ooyang0325/Hi-Res-DAC/hardware/FUNCTIONAL_ECO_LAYOUT_REVIEW.md

# Functional-ECO board: manual placement and route review

**Capture baseline:** [DAC_HPA_120x100_FUNCTIONAL_ECO_STUDY_ONLY.kicad_pcb](DAC_HPA_120x100_FUNCTIONAL_ECO_STUDY_ONLY.kicad_pcb), 120 × 100 mm, four layers, aligned with the [v1.1-ECO1 schematic](FUNCTIONAL_ECO_2026-09-28.md). The newer [integrated-audio route study](INTEGRATED_AUDIO_ROUTE_STUDY.md) has the same footprint/pad population and is the preferred audio-routing review candidate; its bypass, power and L3 return remain open. The older `DAC_HPA.kicad_pcb`, macro study and separate J702 TVS option are historical comparisons.

The [machine-checked summary](FUNCTIONAL_ECO_LAYOUT_SUMMARY.json) records **544 footprints, 250 named nets, zero footprint bounding-box overlaps and zero KiCad error/warning DRC findings**. The KiCad DRC JSON lists 499 missing connections; the full `pcbnew` ratsnest counts **1,144**. All populated pad nets match the ECO schematic. The conservative JLC package-pair/body-edge screens report zero classified findings, but exact machine access and JLC order DFM remain open. All 478 component bodies resolve to STEP/VRML models; 66 copper-only items intentionally have none.

## Hand changes in this iteration

| Group | Exact change | Measured effect and limit |
| --- | --- | --- |
| U605 MCU readback | U621 and C667 were placed by U605. R688/R689 stayed at 470 kΩ and were moved beside U621; R952/R953 isolate its strong outputs and R954/R955 provide MCU-side fail-high pulls. | The two high-impedance R688/R689→U621 input pad distances are **1.687/1.856 mm**. C667 supply/return pad distances are **2.229/2.229 mm**. Actual traces, ground vias, rail corners and fault timing remain unverified. |
| U301 supply row | C305/C306/C307/C308/C309 were placed in a pin-ordered HF bypass row; C303/C304 sit behind it. | DAC pin-to-100 nF pad distances are **2.236/1.863/1.888/2.296/2.236 mm** for AVCC_L/AVCC_R/VCCA/DVCC/1V3. Supply-and-return loop inductance needs routed copper and L2 via inspection. |
| I/V hold-up | C442/C443 and D411/D412 moved south-east by explicit coordinates in `manual_functional_eco_layout.py`. | Opens the strip below K601 for audio routing while preserving zero courtyard/spacing findings. Diode-reservoir rail routing, access and voltage hold-up still require verification. |
| J702 ESD | D707/D708 are now captured on JACK_RP/JACK_LP. One RP relay→TVS→J702 trial and both local signal/GND-via branches are drawn. | The [independent named-pad audit](LOCAL_TVS_ROUTE_AUDIT.json) measures D707→J702 at **3.864 mm** and D708→J702 at **3.255 mm**, under the provisional 4.2 mm screen. It also checks all four J701 contacts. Full LP output, jack sleeves, return-current geometry and IEC system ESD remain open. |
| X201 80 MHz clock | R203 was rotated; R227 was moved beside its oscillator-side node and given a short L2 GND via. The X201→R203→U301 top-layer trunk now passes through TP711, and the R665→U607 monitor input is connected. R703 remains a distant DNF footprint without copper. | Routed X201→R203 is **1.832 mm**, R203→U301 **6.479 mm**, total **8.311 mm**, inside the 2/8/10 mm screens. The R227 signal branch is **1.509 mm**. The actual pad groups pass `pcbnew` connectivity and KiCad custom-rule DRC. Clock edge integrity, loading/duty, oscillator supply return, full monitor circuit and L2 return geometry still need extraction and measurement. |

The board has **28 F.Cu track segments, seven through vias** and one filled L2 GND zone. These are local TVS branches/returns and the clock trunk, pull-down return and monitor-input branch. There is no USB pair, I²S, complete DAC/I/V, output, power or protection routing. A clean DRC on this partial copper is only a geometry and rule result.

## Output-stage route blocker found by hand probes

U401/U402 output links and relay contacts are vertically opposed: LP/RP links leave above their lower relays K601/K603, while LN/RN links leave below their upper relays K602/K604. Four independent straight-line length checks therefore hid a topological crossing. The VSON-10 output pad pitch is 0.50 mm with 0.30 mm pads, so a 0.50 mm trace directly at a pad leaves only 0.10 mm to its neighbour, below the 0.20 mm rule. A **0.25 mm local escape** leaves 0.225 mm by ideal geometry; it must widen promptly to ≥0.50 mm. The current board's custom rule permits that local width, with final length/DFM inspection still required.

The older temporary route probes under `/private/tmp` are **not** part of the current KiCad board. Their initial "DRC-clean" reports were made in temporary projects that omitted the matching `.kicad_dru` file, so those reports checked only generic clearances. They cannot establish compliance with this board's L1-only headphone LEG/JACK policy or 2 mm left/right separation. I reran the 180° RP-bridge trial with the former rules: it had **15 physical errors** (three disallowed inner-layer/via items and 12 left/right clearance errors). A sixteenth `length` error counted an unrelated branch on `JACK_LP`; the current [named-pad TVS audit](LOCAL_TVS_ROUTE_AUDIT.json) replaces that unreliable branched-net rule. The newer, separate [270° output macro study](OUTPUT_MACRO_ROUTE_STUDY.md) passes the actual rules for four amplifier-to-relay inputs and local feedback; its jack, supply, return and remaining board routes are still open.

| Probe | Result | Disposition |
| --- | --- | --- |
| Original 0° amplifiers, all four LEG links | A roughly 31 mm L3 crossover for LP cleared generic spacing; the shorter LP crossing obstructed RN. | Violates the current L1-only/no-via policy and does not establish a compact complete output layout. |
| Older 270° amplifiers with A/B unit swaps | Four LEG links and Rf/Cf pairs could be drawn against generic clearances, but RN needed a 23.26 mm B.Cu crossover and T-node/bypass nets were still undrawn. | Violates the current L1-only/no-via policy. It would also require a schematic pin-net ECO. This is unrelated to the new 270° study, which keeps the original A/B pin mapping. |
| 180° amplifiers, corrected link ordering | An all-L1 RP detour forced JACK_LP through a 0.24 mm LP/RP pinch near K603. A separate trial used a **14.79 mm, 1.0 mm L3 RP bridge** with two Ø0.8/0.4 mm vias and kept the K601→J701/J702 JACK_LP branches about 18–19 mm. | Neither route is accepted. The bridge violates the current L1-only/no-via policy, and the rerun found 12 left/right spacing errors. Its L3 copper alone is estimated at **8.15 mΩ** at 50 °C, before vias/pad necks. The former 9.575 mm KiCad J702 TVS warning was a branched-net length artefact, not the direct named-pad path. |

No temporary trial was promoted to the captured baseline. The separate 270° macro study proved the amplifier-to-relay inputs; the [integrated study](INTEGRATED_AUDIO_ROUTE_STUDY.md) now connects them through both jack types. It still needs local VPOS/VNEG/EP bypass, input/T networks, L3/L4 return and measured R-15 before it can replace the baseline for full routing. The next accepted iteration must prove those networks **together** and pass DRC with the matching `.kicad_dru` file. Keep L2 continuous and measure actual widths, length, crosstalk and stability. The source 20 mm blanket audio rule is an engineering screen; [constraint disposition](CONSTRAINT_DISPOSITION_V2.md) explains the resistance and return-current criteria. Manual coordinate decisions are required; no placement search was used here.

## Remaining release holds

- [F01 all-rate SPI2 capture](MCU_SPI2_CAPTURE_ECO.md) is a feasible clock-rate *proposal*, with no firmware/RTL or proven DAC-side WS fault coverage. The R-28 high-rate frozen-word energy credit remains open.
- [F02/F04 schematic ECO](FUNCTIONAL_ECO_2026-09-28.md) passes netlist/ERC but needs rail/fault tests, JLC U621 G-3 land resolution, nonlinear TVS loading/THD and IEC system ESD.
- [3V3M charge](ATTACH_CHARGE_RECONCILIATION.json) is 6.5 µF nominal and 43.695 µC in the stated no-load-credit planning bound; measure C(V,T), U502 effective output capacitance and USB attach current/region overlap.
- G-3/G-4 sample overlays and polarity, connector soldering process, all critical concurrent routes, extracted clock/audio returns and JLC order DFM are open. **This is not Gerber/CPL/PCBA release data.**

For visual review, run [the command-line export](PCB_CLI_VISUAL_REVIEW.md) on this board. The GitLab `deliver_review_package` artifact includes a current zoomable SVG, GLB 3D assembly, schematic PDF and the audit JSON files for the same commit.
