ooyang0325/Hi-Res-DAC/hardware/LAYOUT_HANDOVER_REPORT.md

# DAC-HPA layout handover for engineering review

For an engineer **continuing** the layout, start with the
[29 September 2026 execution handoff](LAYOUT_ENGINEER_HANDOFF_2026-09-29.md).
This report remains the detailed area-by-area peer-review guide.

**Review snapshot:** 29 September 2026 · KiCad 10 · 120 × 100 mm, four layers. Review the commit accompanying this report and record its full SHA before making findings. Obtain the matching PDF, layer views, 3D model and audits from that commit's [GitLab pipeline](https://gitlab.com/ooyang0325/Hi-Res-DAC/-/pipelines?ref=codex%2Fschematic-v1.1).

**Release state: HOLD.** The [integrated study PCB](DAC_HPA_120x100_INTEGRATED_AUDIO_STUDY_ONLY.kicad_pcb) is the current schematic-aligned layout review candidate. It has **855 track/via items (143 vias), 864 full ratsnest links, zero KiCad DRC violations and 499 DRC-reported unconnected items**. It remains partial copper for engineering review, not a Gerber, CPL, or JLCPCB PCBA order package. Full routing, system ESD, EMI and audio tests remain open. The [functional-ECO board](DAC_HPA_120x100_FUNCTIONAL_ECO_STUDY_ONLY.kicad_pcb) is the earlier placement baseline; `DAC_HPA.kicad_pcb`, the 100 × 80/100 × 100 mm boards, and the older macro studies are comparisons.

A live working checkout may contain uncommitted workbook or KiCad project-setting changes. Record `git status --short` and review the board from the same commit or working tree as its audits; a pipeline archive represents only its source revision.

## Start the review

| Order | Open | Purpose |
| --- | --- | --- |
| 1 | [Reviewer start](REVIEWER_START_HERE.md), [nine-page schematic PDF](DAC_HPA_review_only.pdf), [schematic guide](SCHEMATIC_REVIEW_GUIDE.md), [schematic simplification review](SCHEMATIC_SIMPLIFICATION_REVIEW.md), [discharge capture review](DISCHARGE_CAPTURE_REVIEW.md) | Learn the signal chain and the v1.1-ECO1 pin map. Both headphone jacks and USB High mode remain required; the DNF reduction ideas are proposals only. Check the newly identified U303 EN calculation mismatch and use [source reconciliation](SOURCE_RECONCILIATION.md) and the [functional ECO](FUNCTIONAL_ECO_2026-09-28.md) where the older Office set differs. |
| 2 | [Integrated PCB](DAC_HPA_120x100_INTEGRATED_AUDIO_STUDY_ONLY.kicad_pcb), [DAC/core route checkpoint](DAC_CORE_ROUTE_STUDY.md), [integrated route study](INTEGRATED_AUDIO_ROUTE_STUDY.md), [constraint disposition](CONSTRAINT_DISPOSITION_V2.md), [Freerouting probe](FREEROUTING_PROBE.md) | Inspect the current DAC/CPLD paths and wider partial routes, returns, component access and provisional limits. The whole-board Freerouting result was rejected; two local low-speed paths were selected and validated separately. Compare the earlier functional-ECO board only when a placement change needs context. |
| 3 | [Placement review guide](PLACEMENT_REVIEW_GUIDE.md), [summary JSON](INTEGRATED_AUDIO_SUMMARY.json), [3D-model review](3D_MODEL_REVIEW.md) | Check the measured screens and their limits. The current board has 478 resolvable component bodies; four VRML film-capacitor envelopes show in KiCad's 3D Viewer but not the exported GLB. |
| 4 | [PCBA process review](PCBA_PROCESS_REVIEW.md), [JLC DFA/DFM rules](JLCPCB_DFA_DFM_RULES.md), [G-3 overlays](G3_OVERLAY_INDEX.md), [G-4 checklist](G4_POLARITY_CHECKLIST.md), [discharge fit option](DAC_HPA_120x100_DISCHARGE_FIT_OPTION_ONLY.kicad_pcb) | Separate physical sample and JLC order questions from KiCad geometry checks. The three-2512 option is a package trial only, with 0.05 mm nominal body-edge margin at R530 and no schematic/BOM ECO. |
| 5 | [Findings template](REVIEW_FINDINGS_TEMPLATE.md) | Return a disposition tied to the reviewed SHA, reference/pad/net, PCB coordinates and layer, evidence, and the action needed to close each issue. |

### Export and zoom into the PCB from a terminal

From the repository root, explicitly pass the **integrated** PCB. The script otherwise defaults to the older functional-ECO baseline:

```sh
git rev-parse HEAD
git status --short
KICAD_CLI=/Applications/KiCad/KiCad.app/Contents/MacOS/kicad-cli \
  bash hardware/make_review_views.sh /tmp/dac-hpa-integrated-review \
  hardware/DAC_HPA_120x100_INTEGRATED_AUDIO_STUDY_ONLY.kicad_pcb
```

On a KiCad 10 Linux installation, use `KICAD_CLI=kicad-cli`. Open `01_body_courtyard.svg`, `02_top_copper.svg`, `03_l2_ground.svg`, **`10_l3_power.svg`**, mirrored `07_bottom_copper.svg`, `08_board_3d.glb`, and `09_drc.json` in the output directory. The [CLI visual guide](PCB_CLI_VISUAL_REVIEW.md) explains mask, paste, legend, image tiling and the commands for rerunning the read-only audits. Inspect the L3 VPOS bridge together with L4, rather than inferring its coupling from the top plot. Open the PCB in KiCad's 3D Viewer for the film-capacitor envelopes omitted from GLB.

## What the present board establishes

| Checked fact | Current result and evidence boundary |
| --- | --- |
| Capture and geometry | 544 footprints, 250 named nets, 855 track/via items (143 vias) and one saved filled L2 GND polygon. The current [route delta](INTEGRATED_AUDIO_MANUAL_DELTA.json) contains 138 hand-chosen footprint moves, eight removed source-copper items and 828 added items. Seven added segments form two individually reviewed Freerouting-assisted low-speed paths; all other added waypoints were chosen manually. |
| DAC/CPLD and local power routes | BCLK/LRCLK/SDATA measure **22.213/22.324/22.879 mm**, with **0.666 mm** spread; MCLK is **8.381 mm** and R215→U202 FAM_CLK is **3.039 mm**. C213/C214/C215 local U202 paths measure **1.103/2.056/3.057 mm**; U302 VIN→C301 is **0.875 mm**, OUT→C302 **2.131 mm**; U303→DAC 1V3 is connected at **25.393 mm with two vias**. C622 at (108.65, 105.50) has a 4.615 mm U604.8→C622.1 path and a 1.020 mm C622.2→GND-via path; saved L2 supports both local paths, while the global 3V3D feed remains open. Thirty-five local GND pads reach L2. Two U202 and five U301 EP vias are filled/capped. The [via-pad audit](INTEGRATED_AUDIO_VIA_PAD_PROCESS_AUDIT.json) leaves 45 unfilled nearby sites for JLC mask/process review. See the [DAC/core route audit](DAC_CORE_ROUTE_AUDIT.json) and [study](DAC_CORE_ROUTE_STUDY.md). |
| Schematic and CAD checks | The pipeline verifies 34 documented workbook-to-schematic pin/net deltas, 0 ERC violations, pad/net identity and the manual board replay. KiCad DRC reports **0 violations and 499 unconnected items**; the full `pcbnew` ratsnest has **864** links. These are partial-board checks and do not prove full-board routability. |
| U609/U610 timer and film bypass | All 12 named-pad timer branches pass the ≤8 mm screen without timer-net vias. U609 LP C/Q/R routes measure **6.089/5.340/4.943 mm** and LN **6.038/5.814/6.685 mm**; U610 LP is **6.442/7.607/1.789 mm** and LN **7.177/7.712/7.787 mm**. KiCad's native U609.10→R921.2 rule measures **7.885 mm** because it includes 1.20 mm of the C632 sibling branch; both methods pass. R921's 0.055/0.092 mm courtyard gaps to U609/Q624 still need G-3 body overlay. C631/C632/C633/C634 GND returns reach L2 in **3.580/3.656/2.650/2.650 mm**. C635/C636 U609 VPOS/VNEG local bypasses connect through 11 new vias (six GND, three VPOS, two VNEG). Upstream rail feeds and U609 VT/control escapes remain open. C636 has a pair-specific **0.60 mm** side-courtyard gap to C631/C632; the four film-cap north/south solder approaches pass at ≥1.5 mm (minimum **3.045 mm**) in the [film solder-access audit](INTEGRATED_AUDIO_FILM_SOLDER_ACCESS_AUDIT.json). U605/R675/R676/R679/R677 moved left **1.2 mm** and C625 moved near R666, clearing six measured 5 mm I²S/protection gaps. C638 uses a two-via L3 VNEG bridge. |
| Track shape and placement screens | The integrated checker finds **0 exact or near-90° bends**, zero footprint bounding-box overlaps and zero classified JLC spacing findings. It counts eight near-orthogonal joins at component pad centres; straight-through T/cross junctions are classified separately. The timer pair-specific **0.60 mm** film-cap side-courtyard exception retains at least **1.5 mm** north/south solder approach per the [film solder-access audit](INTEGRATED_AUDIO_FILM_SOLDER_ACCESS_AUDIT.json). These screens do not replace JLC order review or assembly inspection. |
| Selective routing assist | The rejected whole-board [Freerouting probe](FREEROUTING_PROBE.md) supplied only two individually checked low-speed local paths: `N2_AUD_EN_MCU` R237.1→U201.51 at **4.285 mm** and `N7_LEDR_A` R702.2→D706.1 at **4.649 mm**. They add seven 0.20 mm F.Cu segments, no vias and no right-angle bends; saved L2 remains directly below both. |
| DAC and I/V | Four U301→U403/U404 input routes are 4.294/6.030/6.837/4.786 mm with no vias; DACR has only **0.163 mm** under the provisional 7 mm ceiling. Saved L2 lies beneath those routes at 0.01 mm centreline samples and ±0.05/0.10 mm offsets. The largest projected **2D** I/V feedback area is 4.875 mm². These screens do not extract stability or return impedance. |
| Output and ESD | Four amplifier legs reach their J701 contacts; LP/RP also branch to J702. Six named-pad TVS routes measure 3.255–4.03 mm against the provisional 4.2 mm limit. Loaded output impedance, ESD return and system tests remain open. |
| JLC/3D screens | The classified package/edge proxy and via-ring audit report zero findings. Of 463 JLC-placed references, **447** are classified by the package-spacing proxy and **16** need individual review. The model-path audit resolves 478 component bodies. None of these screens is JLC order approval or a physical fit measurement. |

The detailed measurements and conditional R-15 output-impedance model are in the [route study](INTEGRATED_AUDIO_ROUTE_STUDY.md) and [trace budget](INTEGRATED_AUDIO_TRACE_BUDGET.json). Treat those model values as planning estimates: the assumed 50 mΩ jack contact has no maker maximum, the 3.5 mm sleeve return is not extracted, and neither jack has a completed loaded measurement.

## Reviewer decisions to return

| Priority | Location and question | Evidence needed to close it |
| --- | --- | --- |
| 1 · Analog return and stability | U301 (90.5, 81), U403 (96.3, 77.2), U404 (96.3, 84.8). DACL's U403.6→C417.1 feedback branch lacks direct L2 under **1.9426 mm** of its centreline near the `N4_IVL_P` via at **(96.625, 78.170)**. The DACR input route is 6.837 mm, and VREF reaches 14.422 mm. Is the feedback, bypass and reference geometry acceptable after extraction? | Review the actual 3D feedback and return-current path, summing capacitance, VREF noise and I/V stability/step response. A new via or placement proposal must still pass the 7 mm DAC input screen, courtyard clearances and DRC. |
| 2 · Cross-layer audio and power | The `N4_IVR_P`→R409 feed is **47.752 mm**. L3 local VPOS crosses the two right I/V L4 feeds around **x = 115–121, y = 74–76 mm**. U501 is at **(72, 132)**; local copper exists but main VPOS/VNEG source feeds to U401/U402 and their exposed-pad thermal routes do not. The seven filled/capped EP vias are at U202/U301; they do not close U401/U402 EP thermal routes. | Co-route the rails and returns with the audio feeds, extract coupling and shared impedance, and test loaded stability, noise, THD+N and crosstalk. Examine U501 C510/C511 ground-via spacing of 8.160/6.767 mm as geometry, not an extracted loop length. Full audio/EMI tests remain open. |
| 3 · Remaining route feasibility | USB D+/D−, I²S branches beyond the drawn source-to-DAC paths, U609 VT/control escapes, upstream rail feeds, much of the power/protection network and most of the 864 ratsnest links remain. All 12 U609/U610 timer signal branches pass the named-pad 8 mm screen. | Trial the USB 90 Ω pair against the quoted JLC stack-up, complete remaining I²S branches and U609 VT/control escapes with L2 returns and timing checks, and draw remaining bleed/reset branches before accepting the placement. Demonstrate that critical paths coexist. |
| 4 · Connectors, DFA and JLC process | J701 (146.5, 76), J702 (150.84, 109.5), J101 (45, 75). J101 shell stakes and J702 plated slots 1/2 have **no F.Paste apertures**. J101 overhangs the left edge by 0.05 mm; J702 is 0.33 mm from the right edge. C423/C426 courtyard gaps are 0.150–0.194 mm. | Record G-3 1:1 physical overlays and remaining G-4 polarities; obtain JLC acceptance for slot soldering, enlarged lands, panel rails, mask and component access. Inspect the C437/J701/K602 corridor and 16 unclassified package references in the actual order preview. |
| 5 · Function and measured outputs | The all-rate post-CPLD capture/guard, DAC-side WS fault coverage, readback corners, attach current, 3V3D/1V3 discharge and system ESD are still qualification holds. R-15 depends on estimated contacts and an unextracted jack return. | Review [F01 capture proposal](MCU_SPI2_CAPTURE_ECO.md) as unimplemented, the [discharge capture/model mismatch](DISCHARGE_CAPTURE_REVIEW.md), [pre-layout gates](PRELAYOUT_GATES.md), and the [PCBA process record](PCBA_PROCESS_REVIEW.md). Require operating firmware/RTL, fault and power-sequence tests, jack impedance measurements and ESD results before functional or order release. |

G-1/G-2 connector continuity reports were accepted by the owner for layout planning with the raw measurement log waived. **That waiver does not close G-3 footprint overlays or G-4 polarity checks.** The 3.5 mm output is for TRS plugs only; J702 pins 5/6 are unused break contacts and must remain unconnected. J701 switch pads 9/10 likewise remain unconnected in this candidate.

Return each finding as **pass**, **issue**, **needs evidence**, or **not reviewed** in the [findings template](REVIEW_FINDINGS_TEMPLATE.md). A proposal to change the board should cite the affected schematic/PCB net and controlled constraint, preserve the explicit manual route record, and rerun the integrated checker and GitLab pipeline. Do not use the historical automatic `place_board.py --force` flow to regenerate this manual candidate.
