ooyang0325/Hi-Res-DAC/hardware/PRELAYOUT_GATES.md

# Pre-layout gate record — design set v1.1

Design Spec v1.1 permits **provisional placement on a 100 × 80 mm board**. The owner later selected 100 × 100 mm, then allowed the 120 × 100 mm manual placement. The [functional ECO](FUNCTIONAL_ECO_2026-09-28.md) makes the 544-footprint candidate schematic-aligned, including the explicit U403/U404 A/B-channel reassignment; the former primary is historical. The Spec originally held schematic freeze and routing until G-1–G-4 passed with signed measurement records. On 27 September 2026 the owner explicitly waived the G-1/G-2 measurement log after reporting the two-sample checks below. Treat G-1/G-2 as owner-accepted for layout planning, **not** as independently evidenced passes. The [integrated-audio study](INTEGRATED_AUDIO_ROUTE_STUDY.md) draws four DAC→I/V inputs, I/V feedback, eight I/V→first-T feeds, the local T cells, output paths through both jack types and U501 local switching/feedback copper. The newer [DAC/core checkpoint](DAC_CORE_ROUTE_STUDY.md) measures the U202→U301 I²S paths at 22.213/22.324/22.879 mm and MCLK at 8.381 mm, plus local U202/U302 and U303→DAC power paths. The current board has 855 track/via items (143 vias), 864 full ratsnest links, zero DRC violations and 499 DRC-reported unconnected items. True I/V loop and return extraction, upstream source feeds, U401/U402 output-amplifier EP thermal routing and L3/L4 returns remain open. Two U202 and five U301 EP vias are filled and capped; 45 unfilled via-to-SMT-pad sites remain for JLC mask/process review. Full routing, system ESD, EMI and audio tests, G-3/G-4, measured R-15 and F01–F04 continue to hold release. KiCad netlist/ERC and a passing GitLab pipeline establish capture consistency, not operating function or route quality.

| Gate | Evidence needed before schematic freeze and routing | Current record |
| --- | --- | --- |
| G-1 — J101 USB-C | Original protocol: two identified USB4105-GF-A samples; DMM continuity of all 12 GCT solder lands, the four shell stakes and both plug orientations against the 16 JLC pad IDs; signed pad-to-contact table. | **Owner-accepted with evidence waiver.** Owner reports both samples fully match the KiCad map, including both plug orientations. Sample IDs, raw readings and signed table were explicitly waived; no independent record exists. |
| G-2 — J701/J702 jacks | Original protocol: two identified samples of each jack; pad-to-plug contact table with no plug, fully inserted and slow insertion/removal; all internally common pairs; J701 tabs 11/12 versus sleeve/bushing; J702 break contacts 5/6. Only TRS use is permitted for J702. | **Owner-accepted with evidence waiver.** Owner reports both J702 samples match 3–5 and 4–6 closed without a plug and open with TRS inserted; pads 1/2 = sleeve, 3 = right ring, 4 = left tip. Both insertion sweeps showed only expected break transitions; pads 5/6 never touched sleeve or opposite channel; there is no accessible metal shell. Owner reports both J701 samples match pad 1 = sleeve, 2/3 = R−, 4/5 = R+, 6 = L−, 7/8 = L+; tabs 11↔12 and each ↔bushing short, each ↔sleeve open; pads 9↔10 short without plug, open inserted and change during insertion/removal while isolated from audio pads 1–8 in both end states. Sample IDs, raw readings and signed table were explicitly waived; no independent record exists. |
| G-3 — 1:1 footprints | Drawing/sample overlay of J101/J701/J702, K601–K604, X201–X203, U202 exposed pad, the other new/changed lands in Spec §9.6, including U611/U612, Q627, C647–C654, TI DGK U613–U620, and **new U621 C507231**. Record pin-1 marks, slots, pegs, copper clearance and ≥0.1 mm terminal overlap; obtain JLCPCB DFM acceptance of the enlarged jack copper and U621's TI/JLC DCK land difference. | Open. Owner reports all originally listed physical samples are ready. Two review-only 1:1 overlay sheets and a 30-footprint checklist are prepared, including U621 and D707/D708; no overlay results are recorded. Owner chose copper-only enlargement: J701 2.15 × 1.25 mm pads around unchanged 1.40 × 0.50 mm slots; J702 pads 1/2 2.25 × 1.35 mm around unchanged 1.50 × 0.60 mm slots. Both reach ≥0.31 mm worst copper ring at JLCPCB's +0.13 mm plated-slot tolerance. |
| G-4 — polarity | DMM diode/continuity checks on two samples against body/tape marks for D705/D706, BAT54S, D102, D104/D105, D411/D412, D609/D610, C442/C443, Q623–Q627, K601–K604 and the other pin-1 parts in Notes §9.6. | Partial: owner reports two physical samples each of D705 and D706 diode-test as pad 1 anode (+), pad 2 cathode (−), matching KiCad. Sample IDs/readings and the remaining polarity/pin-1 parts are still open. |

## Decisions already in force

- The owner allowed a 120 × 100 mm primary, four-layer manual placement after the 100 × 100 mm comparison. The 100 × 80 mm and 100 × 100 mm automatic boards remain review comparisons. Top-side Standard PCBA and the owner-fitted list remain as in Spec v1.1. The source document's outline needs revision before manufacturing freeze.
- U403/U404 use the owner-approved OPA2210IDGKR VSSOP-8, JLCPCB C2876414, with positive DAC legs on physical B and negative legs on A. DACL/DACLB/DACR/DACRB routed lengths are **4.294/6.030/6.837/4.786 mm** on F.Cu without vias, under the provisional ≤7 mm target; DACR has only **0.163 mm** margin. Saved L2 GND is directly beneath all four inputs at 0.01 mm route samples and offsets 0, ±0.05, ±0.10 mm. The source documents still specify SOIC-8, the earlier A/B assignment and ≤5 mm; extracted capacitance, 3D feedback/return geometry and step response must close the reassessment.
- The 3.5 mm output is for TRS plugs only. The HRO jack has a TRRS body, but TRRS headphones are outside the supported use; G-2 needs the intended TRS test, which the owner reports matched on both samples. The PCB silkscreen/user instructions should say “3.5 SE · TRS only”.
- The v1.1 defaults remain adopted: pairwise boot self-test with production per-leg injection, the Spec's DC-energy definition, and the High-mode 32 Ω frozen-full-scale engineering estimate with a bring-up energy test. Reopening self-test coverage would add parts and must happen before routing.
- The v1.1 model assumed 50 mΩ per jack contact and per 0 Ω output link. The [review-only R417–R420 BOM candidate](OUTPUT_LINK_BOM_ECO.md) has a 1 mΩ manufacturer maximum per link; the unchanged contact estimate has no maker maximum. With that candidate, the integrated board's conditional worst 4.4 mm estimates are **0.3862/0.3737 Ω (L/R) at 1 kHz** and **0.3990/0.3864 Ω at 20 kHz**. The latter is a model sensitivity if the same ≤0.5 Ω limit applies there. Measure both jacks over the intended audio band, extract the 3.5 mm sleeve return and confirm R-15's frequency scope; this is not a pre-layout measurement.
- The owner chose at least a 0.30 mm worst copper ring by enlarging copper only. Using JLCPCB's +0.13 mm plated-slot tolerance, J701/J702 now reach ≥0.31 mm worst ring. Slots, pad centres and peg holes do not move. G-3 overlay and JLCPCB DFM acceptance remain required.
- The ring calculation does not include slot-to-copper registration error; JLCPCB must confirm the final land in DFM. The nearest J701 pad-to-pad copper gap is 0.25 mm.
- The integrated study's custom DRC enforces **2 mm F.Cu left/right clearance for pre-link `N4_*_OUT` copper** against the opposite channel's output/leg/jack copper, in addition to the existing post-link 2 mm rule. The J701 fixed-contact fanout retains its narrow courtyard exception. This partial-copper screen does not close L4 coupling or measured crosstalk.
- The integrated board has **138 explicit moves, eight removed source-copper items and 828 added copper items** against the functional-ECO baseline. Eight local T triplets and amplifier input/shunt connections are drawn on F.Cu; R444/C433 rotations avoid T/ground crossings, while K601/R417 moved 2.4 mm with rerouted copper and J701/J702 stayed fixed. The longest local T branches are 6.53/7.25/8.29 mm (Rin→Rout/capacitor→Rout/Rout→amplifier). Four I/V outputs now feed all eight first T resistors; the longest is **47.752 mm** on the right, and R411/R413 feeds are **27.289/41.648 mm**. The projected 2D I/V feedback model reaches **4.875 mm²**, excluding vertical and return-current area. DACL's U403→C417 feedback branch still lacks direct L2 for **1.9426 mm** of centreline, **0.0597 mm** more than the like-for-like prior baseline, so its return/stability extraction remains on HOLD. Central VREF copper reaches **14.422 mm**. Inspect C423/C426's 0.150–0.194 mm courtyard gaps and the C437/J701/K602 corridor in JLC DFM; extract the long cross-layer feeds.
- U501 local switching, VIN, cap and feedback groups have copper, with three short **0.20 mm** WSON VIN escapes. Its B.Cu `5V_ANA_F` feeder now detours around F.Cu `N5_FBP`, removing projected track and unshielded pad-inclusive overlap; the original power-via antipad remains. VIN3→C507 is **6.014 mm** against a 6.1 mm bound. C510/C511 GND vias are **8.160/6.767 mm** from the IC GND via by straight L2 via spacing; this is not a return-current extraction or a completed source-to-amplifier rail route.
- All 12 U609/U610 timer signal branches now meet the named-pad ≤8 mm screen without timer-net vias. U609 LP C/Q/R routes are 6.089/5.340/4.943 mm and LN routes 6.038/5.814/6.685 mm; C631/C632 GND returns reach L2 in 3.580/3.656 mm. C635/C636 local bypasses connect through 11 new vias (six GND, three VPOS, two VNEG), while upstream rails and U609 VT/control escapes remain open.
- The owner approved a provisional ≤4.2 mm J701 TVS signal route with short L2 GND returns and a system IEC ESD test. The four J701 paths measure 3.83–4.03 mm; both J702 branches also meet the provisional screen. The functional-ECO baseline had an 8.311 mm hand-routed clock trunk and 1,144 full ratsnest gaps. The current board's MCLK is 8.381 mm and its BCLK/LRCLK/SDATA paths are 22.213/22.324/22.879 mm, with 0.666 mm spread. The current board has 544 footprints, 250 named nets, 855 track/via items (143 vias), zero DRC violations, 499 DRC-reported unconnected items and 864 full `pcbnew` ratsnest links; G-3/G-4 and the other functional gates keep routing release on HOLD.

## Holds after layout

| Gate | Remaining work |
| --- | --- |
| G-5 — netlist/BOM freeze | Re-run the design, stress and PCBA checks after layout; confirm value-locked Rf, VREF and leg parts; review routed geometry and manufacturing outputs. |
| G-6 — order release | Obtain JLCPCB's written method for soldering J101 stakes S1–S4 and J702 slots 1/2, or invoke the owner bottom-side solder fallback. Confirm J702 reflow suitability and C631–C634 film-capacitor dwell or owner fitting; resolve stock/private-library lines, order remarks, quote, X-ray and placement rotation. |

Although G-6 is later, provisional placement must leave L4 access to J101 stakes and J702 slots, allow hand-solder clearance if J702 becomes entirely owner-fitted, and preserve 1.5 mm iron clearance around C631–C634 for their owner-fit fallback. These choices prevent an order-stage answer from forcing a board redesign.

The 22 open qualification rows in the Evidence register are bring-up obligations, not 22 additional pre-layout gates. Important thin margins include Default current, X201 duty/load, High-mode 32 Ω fault energy, timer leakage/reset level, and output power; the designed-in tests and fallbacks remain in Spec §9.1 and Notes Chapter 10.

For physical G-3 work, print `G3_CONNECTOR_OVERLAY_REVIEW_ONLY.svg` and `G3_PART_OVERLAY_REVIEW_ONLY.svg` at actual size, verify the 10 mm bars, use `G3_OVERLAY_INDEX.md` for cell-to-part mapping, then enter sample IDs and measured results in `G3_OVERLAY_CHECKLIST.md`. This record does not substitute for G-1/G-2 continuity or G-4 polarity.

`G1_G2_CONTINUITY_RECORD.md` preserves the original measurement template for traceability, but the owner waived completing it for G-1/G-2. Use `G4_POLARITY_CHECKLIST.md` for the still-open diode, capacitor and pin-1 results; the waiver does not cover G-3 or G-4.
