ooyang0325/Hi-Res-DAC/hardware/REVIEWER_START_HERE.md

# DAC-HPA peer review: start here

For the layout review sequence and decisions to return, first read the [layout handover report](LAYOUT_HANDOVER_REPORT.md). An engineer resuming placement and routing should also read the [29 September execution handoff](LAYOUT_ENGINEER_HANDOFF_2026-09-29.md).

**Review snapshot:** schematic capture **v1.1-ECO1** and the current 120 × 100 mm partial-routing board. Record the Git commit SHA you review; use the PDF, board and documents from that revision. The board has 544 footprints, 250 named nets, 855 track/via items (143 vias), zero DRC violations, 499 DRC-unconnected items and **864 full `pcbnew` ratsnest links**. The manual delta is 138 moves, eight source-copper removals and 828 additions. The [DAC/core checkpoint](DAC_CORE_ROUTE_STUDY.md) records BCLK/LRCLK/SDATA at 22.213/22.324/22.879 mm, MCLK at 8.381 mm, U202 bypass paths at 1.103/2.056/3.057 mm, connected U303→DAC 1V3 at 25.393 mm with two vias, and local C622 3V3D/GND bypass paths; the global 3V3D feed remains open. All 12 U609/U610 timer branches pass the named-pad ≤8 mm screen without timer-net vias. U609 LP C/Q/R routes measure 6.089/5.340/4.943 mm and LN routes 6.038/5.814/6.685 mm; U610 values are unchanged. C631/C632/C633/C634 GND returns reach L2 in 3.580/3.656/2.650/2.650 mm. C635/C636 U609 bypasses connect with 11 added vias (six GND, three VPOS, two VNEG). The upstream rail feed and U609 VT/control escapes remain open. C636 has a pair-specific 0.60 mm side-courtyard gap to C631/C632; the four film-cap north/south solder approaches pass the audit at ≥1.5 mm (minimum 3.045 mm). U605/R675/R676/R679/R677 shifted left 1.2 mm and C625 moved near R666, clearing six measured 5 mm I²S/protection gaps. C638 uses a two-via L3 VNEG bridge. The current route/placement checks report zero exact/near-90° bends, zero footprint bbox overlaps and zero classified JLC spacing findings. Two U202 and five U301 EP vias are filled/capped; U401/U402 output-amplifier EP thermal routes remain open. The 45 preexisting unfilled near-pad sites still need process review; the audit reports zero overlap and zero sub-0.10 mm gaps. Full routing, system ESD, EMI and audio tests remain open; DRC 0 applies to this partial board only.

For a repository checkout, run `git rev-parse HEAD` and record the result in the findings template. The CI artifact's `REVIEW_COMMIT.txt` names its exact source revision; the source ZIP contains committed files from that revision. If a KiCad installation lacks its stock 3D library, set `KICAD10_3DMODEL_DIR` to this checkout's `hardware/KICAD_STOCK_MODELS` directory before opening the board.

## Open the design in five minutes

| Need | Open |
| --- | --- |
| Read the circuit without KiCad | [Nine-page schematic PDF](DAC_HPA_review_only.pdf), or the PDF regenerated in the GitLab `deliver_review_package` artifact for the reviewed commit. |
| Edit or inspect the schematic | [KiCad project](DAC_HPA.kicad_pro) → [root schematic](DAC_HPA.kicad_sch), with eight linked sheets. |
| Inspect current DAC/CPLD routes and the wider audio placement | [DAC/core route checkpoint](DAC_CORE_ROUTE_STUDY.md), [integrated-audio board](DAC_HPA_120x100_INTEGRATED_AUDIO_STUDY_ONLY.kicad_pcb), [integrated route study](INTEGRATED_AUDIO_ROUTE_STUDY.md), [routing constraints](CONSTRAINT_DISPOSITION_V2.md), and the zoomable SVG/GLB from the `deliver_review_package` CI artifact. |
| Understand the routing experiment | [Freerouting probe](FREEROUTING_PROBE.md). The whole-board session was rejected; two short low-speed local paths were individually verified and added to the current board. |
| Review component reduction proposals | [Schematic simplification review](SCHEMATIC_SIMPLIFICATION_REVIEW.md). Both headphone jacks and USB High mode remain required; the three small DNF options are documented for later disposition. |
| Review the discharge functional hold | [Discharge capture review](DISCHARGE_CAPTURE_REVIEW.md), [source-derived audit](DISCHARGE_CAPTURE_AUDIT.json), and the separate [2512 physical fit option](DAC_HPA_120x100_DISCHARGE_FIT_OPTION_ONLY.kicad_pcb). U303 EN is intentionally tied to 3V3D, while the shipped C06/C12 scripts assume AUD_EN; their 1V3 timing claim is not validated for this capture. The option board is not schematic/BOM aligned. |
| Compare the capture baseline and intermediate macro | [Functional-ECO board](DAC_HPA_120x100_FUNCTIONAL_ECO_STUDY_ONLY.kicad_pcb), [2D baseline preview](DAC_HPA_FUNCTIONAL_ECO_PLACEMENT_REVIEW.png), [layout review](FUNCTIONAL_ECO_LAYOUT_REVIEW.md), and the [earlier output-macro study](OUTPUT_MACRO_ROUTE_STUDY.md). All share the same schematic pad map. |
| Compare the earlier placement | [Former primary PCB](DAC_HPA.kicad_pcb) and [macro-placement study](DAC_HPA_120x100_MACRO_STUDY_ONLY.kicad_pcb). Both have 536 footprints and predate the new schematic ECO. |
| Export zoomable PCB layer views from a terminal | Follow [CLI visual inspection](PCB_CLI_VISUAL_REVIEW.md) to generate courtyard, copper, mask, paste, legend, 3D and DRC views from the reviewed commit. |
| Inspect J101 at the mating edge | [USB-C 3D closeup](DAC_HPA_J101_3D_detail.png). Its model offset was corrected; the copper footprint stayed at the maker's PCB-edge datum. |
| Obtain a portable snapshot | Use the `deliver_review_package` artifact for the reviewed GitLab pipeline. It contains a current PDF, GLB 3D view, key audits and a ZIP of the committed source. The editable KiCad project is also in the Git repository. |

The signal chain is USB-C input → USB audio bridge/CPLD and clocks → ES9018K2M DAC → I/V and output legs → protection/output switching → 4.4 mm balanced and 3.5 mm single-ended jacks. The power and protection sheets cross these blocks. The 3.5 mm output supports **TRS only**.

## Choose a review path

1. **Circuit and pin mapping:** follow [Schematic review guide](SCHEMATIC_REVIEW_GUIDE.md). Check datasheet pin functions, signal paths, power sequencing, protection fail states, and the explicit source-document corrections. ERC and workbook agreement are already checked, but do not establish electrical correctness.
2. **Placement, routing feasibility, audio/EMI and PCBA:** follow [Placement review guide](PLACEMENT_REVIEW_GUIDE.md). Inspect the integrated board for physical access and realistic simultaneous routes, especially clocks, DACR's tight 7 mm margin, DACL's feedback return detour, long right-side I/V→T feeds, U501's remaining via antipad and supply return, headphone outputs and JLCPCB assembly exceptions. Check the 0.150–0.194 mm courtyard gaps near C423/C426, the tight C437/J701/K602 corridor and via mask. D707/D708 at J702 are now in the schematic/BOM; the [older board-only trial](J702_LOCAL_TVS_OPTION.md) is a historical geometry comparison.
3. **Physical samples:** use the [G-3 overlay checklist](G3_OVERLAY_CHECKLIST.md) and [G-4 polarity checklist](G4_POLARITY_CHECKLIST.md). The two-sample connector results for G-1/G-2 were reported by the owner and accepted for layout planning with the raw log waived; G-3/G-4 are still open.

Put each actionable issue in [Review findings template](REVIEW_FINDINGS_TEMPLATE.md). State the reference/net or board coordinate and layer, the expected condition, what you found, the evidence, and whether it blocks routing, fabrication or assembly. A review can conclude “conditional” when a physical measurement or JLCPCB answer is still required.

## Baseline and decision record

The pin-level baseline is [Parts List v0.9](../doc/DAC_HPA_Parts_List_v0.9.xlsx) and [Calculation Package v1.1](../doc/DAC_HPA_Calculation_Package_v1.1.zip); functional requirements also come from [Design Spec v1.1](../doc/DAC_HPA_Design_Spec_v1.1.docx), [Schematic Design Notes v1.0](../doc/DAC_HPA_Schematic_Design_Notes_v1.0.docx) and [Capture Update Note v1.0](../doc/DAC_HPA_Capture_Update_Note_v1.0.docx). The current KiCad capture applies the explicit [functional ECO](FUNCTIONAL_ECO_2026-09-28.md) after asserting that baseline. Use [Source reconciliation](SOURCE_RECONCILIATION.md) and [Pre-layout gates](PRELAYOUT_GATES.md) to distinguish a controlled change from a new defect.

The controlled changes include VSSOP OPA2210IDGKR at U403/U404, their equivalent A/B-channel reassignment, a **provisional** 7 mm DAC-to-I/V route target, a **provisional** 4.2 mm J701 TVS path, no J703 PCB pads, enlarged J701/J702 slot copper, the D705/D706 polarity correction, the buffered U605 readbacks and D707/D708 local J702 TVS. The [R417–R420 YAGEO output-link substitution](OUTPUT_LINK_BOM_ECO.md) is a review-only BOM candidate with a 1 mΩ manufacturer maximum per link; it retains the 0 Ω value and footprint. The CH32V307 I²S limit and [proposed SPI2 capture path](MCU_SPI2_CAPTURE_ECO.md) remain a functional hold. The [attach-charge reconciliation](ATTACH_CHARGE_RECONCILIATION.json) is a planning bound pending measurement.

## What the existing checks establish

The GitLab pipeline checks schematic regeneration, the exact **34-pin/net** ECO delta, **1,002** selected design-note assertions, critical footprints, 3V3M charge arithmetic, the SPI2 rate/framing contract, pad/net identity, placement geometry, JLC spacing/fabrication proxies, local TVS and clock copper, 3D model paths and KiCad DRC. The integrated-audio job also checks the current manual record of **138 moves, eight removed source copper items and 828 added copper items**; four no-via DAC→I/V routes under 7 mm with saved-L2 support sampled at 0.01 mm and ±0.05/0.10 mm offsets, projected 2D I/V feedback areas under 5 mm², eight I/V→first-T feeds, U501 local switching/feedback connectivity and three bounded 0.20 mm VIN escapes, output-amplifier feedback, relay-to-jack paths, local bypass/EN copper, all 12 U609/U610 timer branches and the conditional output-impedance budget. Local geometry gates include zero exact/near-90° bends, zero bbox overlaps and zero classified JLC spacing findings. A successful pipeline does not close DACL's 1.9426 mm feedback L2 gap, true 3D I/V feedback/return extraction, long right-side feed coupling, U501 return-current extraction, the remaining U609 VT/control escapes and upstream rail feeds, F01's physical WS fault coverage, G-3/G-4, the **864** remaining ratsnest links, upstream source feeds and output-amplifier EP thermal routing, L3/L4 return, measured R-15, system ESD, EMI/audio tests, or JLCPCB's order-specific DFM and via process review. With the review output-link candidate, the conditional 4.4 mm worst paths are 0.3862/0.3737 Ω (L/R) at 1 kHz and 0.3990/0.3864 Ω in the 20 kHz model sensitivity. Jack-contact maxima and complete return paths remain open.

**Review decision requested:** identify defects and required changes before routing proceeds, and mark each open physical or manufacturing condition with the evidence needed to close it. The current source is not a Gerber/CPL/PCBA release.
