ooyang0325/Hi-Res-DAC/hardware/SCHEMATIC_SIMPLIFICATION_REVIEW.md

# Schematic simplification review — 29 September 2026

## Conclusion

Only three high-confidence **review candidates** emerged from the current capture: the DNF MCLK monitor link R703, DNF debugger power link R241, and DNF shield capacitor C101. Each occupies one small PCB footprint while unpopulated. Removing one would also discard its stated measurement, debugging, or EMI option, so treat these as candidates for an owner decision and board-level review, not as approved deletions. Their combined gain is small and cannot resolve the main layout work.

Keep J701 (4.4 mm) and J702 (3.5 mm), and retain USB High power mode, per the owner's decisions. Retain the populated R417–R420 output links, output relays and TVS protection, protection comparators/timers, and amplifier hold-up parts unless a separate functional redesign is analyzed and validated.

## Candidates

| Ref. | Current capture and board evidence | Option lost if removed | Physical and routing gain |
| --- | --- | --- | --- |
| **R703**, 1 kΩ, DNF | On `07_outputs.kicad_sch`, between `MCLK` and `N7_MCLK_MON`. The current integrated study board carries the 0402 at (95, 93.5) mm with those same pad nets. The monitor bus reaches TP732; J703 is schematic-only (`on_board no`). | Optional series-isolated MCLK access at the monitor/test bus. The main MCLK path remains required; R703 provides the branch to TP732. | Frees one 0402 courtyard (1.86 × 0.94 mm, about 1.75 mm²) and its two pad sites; removes this optional branch from netlist and routing. |
| **R241**, 0 Ω, DNF | On `02_usb_bridge.kicad_sch`, between `3V3M` and `N2_J201_3V3`. The current integrated study board carries the 0402 at (54.5, 46.5) mm with those same pad nets. J201 is the debugger pad block. Its symbol description says the link is DNF because the WCH-LinkE 3V3 pin is a power output. | Optional board-side 3V3M reference at J201 pin 1 for a debugger. The DNF state avoids tying the board rail to the WCH-LinkE power output; confirm the debugger's electrical direction and current limits before fitting the link. | Frees one 0402 courtyard (1.86 × 0.94 mm, about 1.75 mm²) and two pad sites; removes this optional power branch while retaining debugger signal access. |
| **C101**, 4.7 nF, DNF | On `01_usb_input.kicad_sch`, between `N1_SHIELD` and GND, in parallel with fitted R107 (0 Ω) on the same nets. The current integrated study board places C101 at (41, 81) mm next to R107 at (43, 81) mm; both footprints confirm the same two nets. The schematic description limits C101's role to the case where R107 becomes a bleed resistor. | An optional high-frequency shield-to-ground bypass for an alternate R107 bleed-resistor experiment. With the present fitted 0 Ω bond, C101 is redundant in the nominal captured configuration; parasitic RF behavior still needs measurement to rule out a useful bypass. | Frees one 0402 capacitor courtyard (1.82 × 0.92 mm, about 1.67 mm²) and two pad sites beside R107; removes one optional parallel branch. The shield bond through R107 remains. |

All three are currently marked DNF in the schematic. Their removal would reclaim PCB courtyard and routing space, not remove three assembled parts from the populated BOM. The current board is only partially routed, so do not count the un-routed option branch as measured track-length savings. Actual usable space depends on neighboring clearances and any replacement routing.

## Congestion evidence

The [`DAC_HPA_120x100_INTEGRATED_AUDIO_STUDY_ONLY.kicad_pcb`](DAC_HPA_120x100_INTEGRATED_AUDIO_STUDY_ONLY.kicad_pcb) is the current 544-footprint, 250-net routing candidate. The review snapshot reports 864 remaining ratsnest links and identifies tight placement/routing areas around C423/C426, C437/J701/K602, the DAC/I/V paths, and output routing ([reviewer start](REVIEWER_START_HERE.md), [integrated audio study](INTEGRATED_AUDIO_ROUTE_STUDY.md)). The dominant congestion is placement and routing. These three DNF 0402 sites, each with roughly 1.7–1.75 mm² of courtyard, are local cleanup opportunities among a small number of unpopulated options. Their removal offers little area beside the larger escape, return-path, and simultaneous-routing constraints.

Board-version limit: the root [`DAC_HPA.kicad_pcb`](DAC_HPA.kicad_pcb) and its 536-footprint / 246-net review are historical and predate the eight-part schematic ECO ([reviewer start](REVIEWER_START_HERE.md)). Candidate pad nets and coordinates above were checked on the 544-footprint integrated study board and against the linked live schematic sheets. These checks establish capture/board identity and footprint occupancy; they do not prove that deleting any branch improves a completed route, EMC, debugger compatibility, or audio performance. The integrated board remains a routing study, not a release board.

## If a candidate is approved later

The sheets are generated: [`generate_schematic.py`](generate_schematic.py) reads the workbook, asserts the pin maps and ECO, and rewrites schematic sources. Represent an approved change in the controlled source/generator flow; a sheet-only edit will be overwritten. Then regenerate and review the schematic/netlist and assembly exports; run `verify_schematic.py`, `verify_design_notes.py`, critical-footprint and ERC checks; update the current integrated-board source/manifest and pad-map checks; and rerun the relevant placement, DRC, route/connectivity, DFM and CI gates. Confirm the three removed refs and affected nets in the netlist-to-board pad comparison, and refresh the PDF and BOM/assembly outputs from the same capture. The existing schematic CI job performs generation and capture checks, while the functional-ECO/integrated-board jobs verify board pad nets and layout assumptions ([`.gitlab-ci.yml`](../.gitlab-ci.yml)). ERC/CI establish capture consistency; functional acceptability of a discarded option requires separate evidence.
