ooyang0325/Hi-Res-DAC/hardware/sim/ems_budget_summary.txt

Headphone-output RF demodulation (output-referred, OPA2210 EMIRR proxy / proxy-10 dB)
noise reference 1.56 uV rms (20 kHz); CM->DM conversion -20 dB; square law invalid above ~0.1 V RF
as built (R417 = 0 \Omega)   E= 3 V/m VHF 30-80 MHz              EMIRR-0   worst      711 uV  ( +53.2 dB re noise)
as built (R417 = 0 \Omega)   E= 3 V/m FM broadcast               EMIRR-0   worst 1.63e+03 uV  ( +60.4 dB re noise)
as built (R417 = 0 \Omega)   E= 3 V/m VHF 150-300 MHz            EMIRR-0   worst      345 uV  ( +46.9 dB re noise)
as built (R417 = 0 \Omega)   E= 3 V/m TETRA/433 ISM/DVB-T        EMIRR-0   worst      519 uV  ( +50.4 dB re noise)
as built (R417 = 0 \Omega)   E= 3 V/m LTE800/GSM900              EMIRR-0   worst    0.542 uV  (  -9.2 dB re noise)
as built (R417 = 0 \Omega)   E= 3 V/m GSM1800/DECT               EMIRR-0   worst  9.8e-07 uV  (-124.0 dB re noise)
as built (R417 = 0 \Omega)   E= 3 V/m Wi-Fi 2.4                  EMIRR-0   worst 3.12e-07 uV  (-134.0 dB re noise)
as built (R417 = 0 \Omega)   E= 3 V/m Wi-Fi 5                    EMIRR-0   worst 3.49e-07 uV  (-133.0 dB re noise)
as built (R417 = 0 \Omega)   E= 3 V/m VHF 30-80 MHz              EMIRR-10  worst 2.25e+03 uV  ( +63.2 dB re noise)
as built (R417 = 0 \Omega)   E= 3 V/m FM broadcast               EMIRR-10  worst 5.15e+03 uV  ( +70.4 dB re noise)
as built (R417 = 0 \Omega)   E= 3 V/m VHF 150-300 MHz            EMIRR-10  worst 1.09e+03 uV  ( +56.9 dB re noise)
as built (R417 = 0 \Omega)   E= 3 V/m TETRA/433 ISM/DVB-T        EMIRR-10  worst 1.64e+03 uV  ( +60.4 dB re noise)
as built (R417 = 0 \Omega)   E= 3 V/m LTE800/GSM900              EMIRR-10  worst     1.71 uV  (  +0.8 dB re noise)
as built (R417 = 0 \Omega)   E= 3 V/m GSM1800/DECT               EMIRR-10  worst  3.1e-06 uV  (-114.0 dB re noise)
as built (R417 = 0 \Omega)   E= 3 V/m Wi-Fi 2.4                  EMIRR-10  worst 9.87e-07 uV  (-124.0 dB re noise)
as built (R417 = 0 \Omega)   E= 3 V/m Wi-Fi 5                    EMIRR-10  worst  1.1e-06 uV  (-123.0 dB re noise)
as built (R417 = 0 \Omega)   E=10 V/m VHF 30-80 MHz              EMIRR-0   worst 7.91e+03 uV  ( +74.1 dB re noise)
as built (R417 = 0 \Omega)   E=10 V/m FM broadcast               EMIRR-0   worst 1.81e+04 uV  ( +81.3 dB re noise)
as built (R417 = 0 \Omega)   E=10 V/m VHF 150-300 MHz            EMIRR-0   worst 3.83e+03 uV  ( +67.8 dB re noise)
as built (R417 = 0 \Omega)   E=10 V/m TETRA/433 ISM/DVB-T        EMIRR-0   worst 5.76e+03 uV  ( +71.3 dB re noise)
as built (R417 = 0 \Omega)   E=10 V/m LTE800/GSM900              EMIRR-0   worst     6.02 uV  ( +11.7 dB re noise)
as built (R417 = 0 \Omega)   E=10 V/m GSM1800/DECT               EMIRR-0   worst 1.09e-05 uV  (-103.1 dB re noise)
as built (R417 = 0 \Omega)   E=10 V/m Wi-Fi 2.4                  EMIRR-0   worst 3.47e-06 uV  (-113.1 dB re noise)
as built (R417 = 0 \Omega)   E=10 V/m Wi-Fi 5                    EMIRR-0   worst 3.88e-06 uV  (-112.1 dB re noise)
as built (R417 = 0 \Omega)   E=10 V/m VHF 30-80 MHz              EMIRR-10  worst  2.5e+04 uV  ( +84.1 dB re noise)
as built (R417 = 0 \Omega)   E=10 V/m FM broadcast               EMIRR-10  worst 5.73e+04 uV  ( +91.3 dB re noise)
as built (R417 = 0 \Omega)   E=10 V/m VHF 150-300 MHz            EMIRR-10  worst 1.21e+04 uV  ( +77.8 dB re noise)
as built (R417 = 0 \Omega)   E=10 V/m TETRA/433 ISM/DVB-T        EMIRR-10  worst 1.82e+04 uV  ( +81.3 dB re noise)
as built (R417 = 0 \Omega)   E=10 V/m LTE800/GSM900              EMIRR-10  worst       19 uV  ( +21.7 dB re noise)
as built (R417 = 0 \Omega)   E=10 V/m GSM1800/DECT               EMIRR-10  worst 3.44e-05 uV  ( -93.1 dB re noise)
as built (R417 = 0 \Omega)   E=10 V/m Wi-Fi 2.4                  EMIRR-10  worst  1.1e-05 uV  (-103.1 dB re noise)
as built (R417 = 0 \Omega)   E=10 V/m Wi-Fi 5                    EMIRR-10  worst 1.23e-05 uV  (-102.1 dB re noise)
as built (R417 = 0 \Omega)   E=30 V/m VHF 30-80 MHz              EMIRR-0   worst 7.11e+04 uV  ( +93.2 dB re noise)
as built (R417 = 0 \Omega)   E=30 V/m FM broadcast               EMIRR-0   worst 1.63e+05 uV  (+100.4 dB re noise)
as built (R417 = 0 \Omega)   E=30 V/m VHF 150-300 MHz            EMIRR-0   worst 3.45e+04 uV  ( +86.9 dB re noise)
as built (R417 = 0 \Omega)   E=30 V/m TETRA/433 ISM/DVB-T        EMIRR-0   worst 5.19e+04 uV  ( +90.4 dB re noise)
as built (R417 = 0 \Omega)   E=30 V/m LTE800/GSM900              EMIRR-0   worst     54.2 uV  ( +30.8 dB re noise)
as built (R417 = 0 \Omega)   E=30 V/m GSM1800/DECT               EMIRR-0   worst  9.8e-05 uV  ( -84.0 dB re noise)
as built (R417 = 0 \Omega)   E=30 V/m Wi-Fi 2.4                  EMIRR-0   worst 3.12e-05 uV  ( -94.0 dB re noise)
as built (R417 = 0 \Omega)   E=30 V/m Wi-Fi 5                    EMIRR-0   worst 3.49e-05 uV  ( -93.0 dB re noise)
as built (R417 = 0 \Omega)   E=30 V/m VHF 30-80 MHz              EMIRR-10  worst 2.25e+05 uV  (+103.2 dB re noise)
as built (R417 = 0 \Omega)   E=30 V/m FM broadcast               EMIRR-10  worst 5.15e+05 uV  (+110.4 dB re noise)
as built (R417 = 0 \Omega)   E=30 V/m VHF 150-300 MHz            EMIRR-10  worst 1.09e+05 uV  ( +96.9 dB re noise)
as built (R417 = 0 \Omega)   E=30 V/m TETRA/433 ISM/DVB-T        EMIRR-10  worst 1.64e+05 uV  (+100.4 dB re noise)
as built (R417 = 0 \Omega)   E=30 V/m LTE800/GSM900              EMIRR-10  worst      171 uV  ( +40.8 dB re noise)
as built (R417 = 0 \Omega)   E=30 V/m GSM1800/DECT               EMIRR-10  worst  0.00031 uV  ( -74.0 dB re noise)
as built (R417 = 0 \Omega)   E=30 V/m Wi-Fi 2.4                  EMIRR-10  worst 9.87e-05 uV  ( -84.0 dB re noise)
as built (R417 = 0 \Omega)   E=30 V/m Wi-Fi 5                    EMIRR-10  worst  0.00011 uV  ( -83.0 dB re noise)
bead in R417                 E= 3 V/m VHF 30-80 MHz              EMIRR-0   worst      146 uV  ( +39.4 dB re noise)
bead in R417                 E= 3 V/m FM broadcast               EMIRR-0   worst      121 uV  ( +37.8 dB re noise)
bead in R417                 E= 3 V/m VHF 150-300 MHz            EMIRR-0   worst     44.9 uV  ( +29.2 dB re noise)
bead in R417                 E= 3 V/m TETRA/433 ISM/DVB-T        EMIRR-0   worst     70.6 uV  ( +33.1 dB re noise)
bead in R417                 E= 3 V/m LTE800/GSM900              EMIRR-0   worst   0.0784 uV  ( -26.0 dB re noise)
bead in R417                 E= 3 V/m GSM1800/DECT               EMIRR-0   worst 1.66e-06 uV  (-119.5 dB re noise)
bead in R417                 E= 3 V/m Wi-Fi 2.4                  EMIRR-0   worst 4.83e-07 uV  (-130.2 dB re noise)
bead in R417                 E= 3 V/m Wi-Fi 5                    EMIRR-0   worst    4e-07 uV  (-131.8 dB re noise)
bead in R417                 E= 3 V/m VHF 30-80 MHz              EMIRR-10  worst      463 uV  ( +49.4 dB re noise)
bead in R417                 E= 3 V/m FM broadcast               EMIRR-10  worst      381 uV  ( +47.8 dB re noise)
bead in R417                 E= 3 V/m VHF 150-300 MHz            EMIRR-10  worst      142 uV  ( +39.2 dB re noise)
bead in R417                 E= 3 V/m TETRA/433 ISM/DVB-T        EMIRR-10  worst      223 uV  ( +43.1 dB re noise)
bead in R417                 E= 3 V/m LTE800/GSM900              EMIRR-10  worst    0.248 uV  ( -16.0 dB re noise)
bead in R417                 E= 3 V/m GSM1800/DECT               EMIRR-10  worst 5.25e-06 uV  (-109.5 dB re noise)
bead in R417                 E= 3 V/m Wi-Fi 2.4                  EMIRR-10  worst 1.53e-06 uV  (-120.2 dB re noise)
bead in R417                 E= 3 V/m Wi-Fi 5                    EMIRR-10  worst 1.27e-06 uV  (-121.8 dB re noise)
bead in R417                 E=10 V/m VHF 30-80 MHz              EMIRR-0   worst 1.63e+03 uV  ( +60.4 dB re noise)
bead in R417                 E=10 V/m FM broadcast               EMIRR-0   worst 1.34e+03 uV  ( +58.7 dB re noise)
bead in R417                 E=10 V/m VHF 150-300 MHz            EMIRR-0   worst      499 uV  ( +50.1 dB re noise)
bead in R417                 E=10 V/m TETRA/433 ISM/DVB-T        EMIRR-0   worst      784 uV  ( +54.0 dB re noise)
bead in R417                 E=10 V/m LTE800/GSM900              EMIRR-0   worst    0.871 uV  (  -5.1 dB re noise)
bead in R417                 E=10 V/m GSM1800/DECT               EMIRR-0   worst 1.84e-05 uV  ( -98.6 dB re noise)
bead in R417                 E=10 V/m Wi-Fi 2.4                  EMIRR-0   worst 5.37e-06 uV  (-109.3 dB re noise)
bead in R417                 E=10 V/m Wi-Fi 5                    EMIRR-0   worst 4.45e-06 uV  (-110.9 dB re noise)
bead in R417                 E=10 V/m VHF 30-80 MHz              EMIRR-10  worst 5.14e+03 uV  ( +70.4 dB re noise)
bead in R417                 E=10 V/m FM broadcast               EMIRR-10  worst 4.24e+03 uV  ( +68.7 dB re noise)
bead in R417                 E=10 V/m VHF 150-300 MHz            EMIRR-10  worst 1.58e+03 uV  ( +60.1 dB re noise)
bead in R417                 E=10 V/m TETRA/433 ISM/DVB-T        EMIRR-10  worst 2.48e+03 uV  ( +64.0 dB re noise)
bead in R417                 E=10 V/m LTE800/GSM900              EMIRR-10  worst     2.75 uV  (  +4.9 dB re noise)
bead in R417                 E=10 V/m GSM1800/DECT               EMIRR-10  worst 5.83e-05 uV  ( -88.6 dB re noise)
bead in R417                 E=10 V/m Wi-Fi 2.4                  EMIRR-10  worst  1.7e-05 uV  ( -99.3 dB re noise)
bead in R417                 E=10 V/m Wi-Fi 5                    EMIRR-10  worst 1.41e-05 uV  (-100.9 dB re noise)
bead in R417                 E=30 V/m VHF 30-80 MHz              EMIRR-0   worst 1.46e+04 uV  ( +79.4 dB re noise)
bead in R417                 E=30 V/m FM broadcast               EMIRR-0   worst 1.21e+04 uV  ( +77.8 dB re noise)
bead in R417                 E=30 V/m VHF 150-300 MHz            EMIRR-0   worst 4.49e+03 uV  ( +69.2 dB re noise)
bead in R417                 E=30 V/m TETRA/433 ISM/DVB-T        EMIRR-0   worst 7.06e+03 uV  ( +73.1 dB re noise)
bead in R417                 E=30 V/m LTE800/GSM900              EMIRR-0   worst     7.84 uV  ( +14.0 dB re noise)
bead in R417                 E=30 V/m GSM1800/DECT               EMIRR-0   worst 0.000166 uV  ( -79.5 dB re noise)
bead in R417                 E=30 V/m Wi-Fi 2.4                  EMIRR-0   worst 4.83e-05 uV  ( -90.2 dB re noise)
bead in R417                 E=30 V/m Wi-Fi 5                    EMIRR-0   worst    4e-05 uV  ( -91.8 dB re noise)
bead in R417                 E=30 V/m VHF 30-80 MHz              EMIRR-10  worst 4.63e+04 uV  ( +89.4 dB re noise)
bead in R417                 E=30 V/m FM broadcast               EMIRR-10  worst 3.81e+04 uV  ( +87.8 dB re noise)
bead in R417                 E=30 V/m VHF 150-300 MHz            EMIRR-10  worst 1.42e+04 uV  ( +79.2 dB re noise)
bead in R417                 E=30 V/m TETRA/433 ISM/DVB-T        EMIRR-10  worst 2.23e+04 uV  ( +83.1 dB re noise)
bead in R417                 E=30 V/m LTE800/GSM900              EMIRR-10  worst     24.8 uV  ( +24.0 dB re noise)
bead in R417                 E=30 V/m GSM1800/DECT               EMIRR-10  worst 0.000525 uV  ( -69.5 dB re noise)
bead in R417                 E=30 V/m Wi-Fi 2.4                  EMIRR-10  worst 0.000153 uV  ( -80.2 dB re noise)
bead in R417                 E=30 V/m Wi-Fi 5                    EMIRR-10  worst 0.000127 uV  ( -81.8 dB re noise)
220 pF at LEG                E= 3 V/m VHF 30-80 MHz              EMIRR-0   worst      222 uV  ( +43.1 dB re noise)
220 pF at LEG                E= 3 V/m FM broadcast               EMIRR-0   worst     19.9 uV  ( +22.1 dB re noise)
220 pF at LEG                E= 3 V/m VHF 150-300 MHz            EMIRR-0   worst     46.5 uV  ( +29.5 dB re noise)
220 pF at LEG                E= 3 V/m TETRA/433 ISM/DVB-T        EMIRR-0   worst   0.0851 uV  ( -25.3 dB re noise)
220 pF at LEG                E= 3 V/m LTE800/GSM900              EMIRR-0   worst   0.0107 uV  ( -43.3 dB re noise)
220 pF at LEG                E= 3 V/m GSM1800/DECT               EMIRR-0   worst  6.8e-11 uV  (-207.2 dB re noise)
220 pF at LEG                E= 3 V/m Wi-Fi 2.4                  EMIRR-0   worst 4.21e-12 uV  (-231.4 dB re noise)
220 pF at LEG                E= 3 V/m Wi-Fi 5                    EMIRR-0   worst 3.28e-13 uV  (-253.5 dB re noise)
220 pF at LEG                E= 3 V/m VHF 30-80 MHz              EMIRR-10  worst      701 uV  ( +53.1 dB re noise)
220 pF at LEG                E= 3 V/m FM broadcast               EMIRR-10  worst     62.8 uV  ( +32.1 dB re noise)
220 pF at LEG                E= 3 V/m VHF 150-300 MHz            EMIRR-10  worst      147 uV  ( +39.5 dB re noise)
220 pF at LEG                E= 3 V/m TETRA/433 ISM/DVB-T        EMIRR-10  worst    0.269 uV  ( -15.3 dB re noise)
220 pF at LEG                E= 3 V/m LTE800/GSM900              EMIRR-10  worst   0.0339 uV  ( -33.3 dB re noise)
220 pF at LEG                E= 3 V/m GSM1800/DECT               EMIRR-10  worst 2.15e-10 uV  (-197.2 dB re noise)
220 pF at LEG                E= 3 V/m Wi-Fi 2.4                  EMIRR-10  worst 1.33e-11 uV  (-221.4 dB re noise)
220 pF at LEG                E= 3 V/m Wi-Fi 5                    EMIRR-10  worst 1.04e-12 uV  (-243.5 dB re noise)
220 pF at LEG                E=10 V/m VHF 30-80 MHz              EMIRR-0   worst 2.46e+03 uV  ( +64.0 dB re noise)
220 pF at LEG                E=10 V/m FM broadcast               EMIRR-0   worst      221 uV  ( +43.0 dB re noise)
220 pF at LEG                E=10 V/m VHF 150-300 MHz            EMIRR-0   worst      516 uV  ( +50.4 dB re noise)
220 pF at LEG                E=10 V/m TETRA/433 ISM/DVB-T        EMIRR-0   worst    0.945 uV  (  -4.4 dB re noise)
220 pF at LEG                E=10 V/m LTE800/GSM900              EMIRR-0   worst    0.119 uV  ( -22.4 dB re noise)
220 pF at LEG                E=10 V/m GSM1800/DECT               EMIRR-0   worst 7.56e-10 uV  (-186.3 dB re noise)
220 pF at LEG                E=10 V/m Wi-Fi 2.4                  EMIRR-0   worst 4.68e-11 uV  (-210.5 dB re noise)
220 pF at LEG                E=10 V/m Wi-Fi 5                    EMIRR-0   worst 3.65e-12 uV  (-232.6 dB re noise)
220 pF at LEG                E=10 V/m VHF 30-80 MHz              EMIRR-10  worst 7.79e+03 uV  ( +74.0 dB re noise)
220 pF at LEG                E=10 V/m FM broadcast               EMIRR-10  worst      698 uV  ( +53.0 dB re noise)
220 pF at LEG                E=10 V/m VHF 150-300 MHz            EMIRR-10  worst 1.63e+03 uV  ( +60.4 dB re noise)
220 pF at LEG                E=10 V/m TETRA/433 ISM/DVB-T        EMIRR-10  worst     2.99 uV  (  +5.6 dB re noise)
220 pF at LEG                E=10 V/m LTE800/GSM900              EMIRR-10  worst    0.376 uV  ( -12.4 dB re noise)
220 pF at LEG                E=10 V/m GSM1800/DECT               EMIRR-10  worst 2.39e-09 uV  (-176.3 dB re noise)
220 pF at LEG                E=10 V/m Wi-Fi 2.4                  EMIRR-10  worst 1.48e-10 uV  (-200.5 dB re noise)
220 pF at LEG                E=10 V/m Wi-Fi 5                    EMIRR-10  worst 1.15e-11 uV  (-222.6 dB re noise)
220 pF at LEG                E=30 V/m VHF 30-80 MHz              EMIRR-0   worst 2.22e+04 uV  ( +83.1 dB re noise)
220 pF at LEG                E=30 V/m FM broadcast               EMIRR-0   worst 1.99e+03 uV  ( +62.1 dB re noise)
220 pF at LEG                E=30 V/m VHF 150-300 MHz            EMIRR-0   worst 4.65e+03 uV  ( +69.5 dB re noise)
220 pF at LEG                E=30 V/m TETRA/433 ISM/DVB-T        EMIRR-0   worst     8.51 uV  ( +14.7 dB re noise)
220 pF at LEG                E=30 V/m LTE800/GSM900              EMIRR-0   worst     1.07 uV  (  -3.3 dB re noise)
220 pF at LEG                E=30 V/m GSM1800/DECT               EMIRR-0   worst  6.8e-09 uV  (-167.2 dB re noise)
220 pF at LEG                E=30 V/m Wi-Fi 2.4                  EMIRR-0   worst 4.21e-10 uV  (-191.4 dB re noise)
220 pF at LEG                E=30 V/m Wi-Fi 5                    EMIRR-0   worst 3.28e-11 uV  (-213.5 dB re noise)
220 pF at LEG                E=30 V/m VHF 30-80 MHz              EMIRR-10  worst 7.01e+04 uV  ( +93.1 dB re noise)
220 pF at LEG                E=30 V/m FM broadcast               EMIRR-10  worst 6.28e+03 uV  ( +72.1 dB re noise)
220 pF at LEG                E=30 V/m VHF 150-300 MHz            EMIRR-10  worst 1.47e+04 uV  ( +79.5 dB re noise)
220 pF at LEG                E=30 V/m TETRA/433 ISM/DVB-T        EMIRR-10  worst     26.9 uV  ( +24.7 dB re noise)
220 pF at LEG                E=30 V/m LTE800/GSM900              EMIRR-10  worst     3.39 uV  (  +6.7 dB re noise)
220 pF at LEG                E=30 V/m GSM1800/DECT               EMIRR-10  worst 2.15e-08 uV  (-157.2 dB re noise)
220 pF at LEG                E=30 V/m Wi-Fi 2.4                  EMIRR-10  worst 1.33e-09 uV  (-181.4 dB re noise)
220 pF at LEG                E=30 V/m Wi-Fi 5                    EMIRR-10  worst 1.04e-10 uV  (-203.5 dB re noise)
bead + 220 pF (ECO)          E= 3 V/m VHF 30-80 MHz              EMIRR-0   worst     12.1 uV  ( +17.8 dB re noise)
bead + 220 pF (ECO)          E= 3 V/m FM broadcast               EMIRR-0   worst     1.57 uV  (  +0.1 dB re noise)
bead + 220 pF (ECO)          E= 3 V/m VHF 150-300 MHz            EMIRR-0   worst     14.4 uV  ( +19.3 dB re noise)
bead + 220 pF (ECO)          E= 3 V/m TETRA/433 ISM/DVB-T        EMIRR-0   worst   0.0214 uV  ( -37.3 dB re noise)
bead + 220 pF (ECO)          E= 3 V/m LTE800/GSM900              EMIRR-0   worst    1e-05 uV  (-103.8 dB re noise)
bead + 220 pF (ECO)          E= 3 V/m GSM1800/DECT               EMIRR-0   worst 2.87e-11 uV  (-214.7 dB re noise)
bead + 220 pF (ECO)          E= 3 V/m Wi-Fi 2.4                  EMIRR-0   worst 1.05e-11 uV  (-223.5 dB re noise)
bead + 220 pF (ECO)          E= 3 V/m Wi-Fi 5                    EMIRR-0   worst 6.41e-13 uV  (-247.7 dB re noise)
bead + 220 pF (ECO)          E= 3 V/m VHF 30-80 MHz              EMIRR-10  worst     38.4 uV  ( +27.8 dB re noise)
bead + 220 pF (ECO)          E= 3 V/m FM broadcast               EMIRR-10  worst     4.96 uV  ( +10.1 dB re noise)
bead + 220 pF (ECO)          E= 3 V/m VHF 150-300 MHz            EMIRR-10  worst     45.6 uV  ( +29.3 dB re noise)
bead + 220 pF (ECO)          E= 3 V/m TETRA/433 ISM/DVB-T        EMIRR-10  worst   0.0677 uV  ( -27.3 dB re noise)
bead + 220 pF (ECO)          E= 3 V/m LTE800/GSM900              EMIRR-10  worst 3.17e-05 uV  ( -93.8 dB re noise)
bead + 220 pF (ECO)          E= 3 V/m GSM1800/DECT               EMIRR-10  worst 9.09e-11 uV  (-204.7 dB re noise)
bead + 220 pF (ECO)          E= 3 V/m Wi-Fi 2.4                  EMIRR-10  worst 3.31e-11 uV  (-213.5 dB re noise)
bead + 220 pF (ECO)          E= 3 V/m Wi-Fi 5                    EMIRR-10  worst 2.03e-12 uV  (-237.7 dB re noise)
bead + 220 pF (ECO)          E=10 V/m VHF 30-80 MHz              EMIRR-0   worst      135 uV  ( +38.7 dB re noise)
bead + 220 pF (ECO)          E=10 V/m FM broadcast               EMIRR-0   worst     17.4 uV  ( +21.0 dB re noise)
bead + 220 pF (ECO)          E=10 V/m VHF 150-300 MHz            EMIRR-0   worst      160 uV  ( +40.2 dB re noise)
bead + 220 pF (ECO)          E=10 V/m TETRA/433 ISM/DVB-T        EMIRR-0   worst    0.238 uV  ( -16.3 dB re noise)
bead + 220 pF (ECO)          E=10 V/m LTE800/GSM900              EMIRR-0   worst 0.000111 uV  ( -82.9 dB re noise)
bead + 220 pF (ECO)          E=10 V/m GSM1800/DECT               EMIRR-0   worst 3.19e-10 uV  (-193.8 dB re noise)
bead + 220 pF (ECO)          E=10 V/m Wi-Fi 2.4                  EMIRR-0   worst 1.16e-10 uV  (-202.6 dB re noise)
bead + 220 pF (ECO)          E=10 V/m Wi-Fi 5                    EMIRR-0   worst 7.12e-12 uV  (-226.8 dB re noise)
bead + 220 pF (ECO)          E=10 V/m VHF 30-80 MHz              EMIRR-10  worst      427 uV  ( +48.7 dB re noise)
bead + 220 pF (ECO)          E=10 V/m FM broadcast               EMIRR-10  worst     55.2 uV  ( +31.0 dB re noise)
bead + 220 pF (ECO)          E=10 V/m VHF 150-300 MHz            EMIRR-10  worst      506 uV  ( +50.2 dB re noise)
bead + 220 pF (ECO)          E=10 V/m TETRA/433 ISM/DVB-T        EMIRR-10  worst    0.752 uV  (  -6.3 dB re noise)
bead + 220 pF (ECO)          E=10 V/m LTE800/GSM900              EMIRR-10  worst 0.000352 uV  ( -72.9 dB re noise)
bead + 220 pF (ECO)          E=10 V/m GSM1800/DECT               EMIRR-10  worst 1.01e-09 uV  (-183.8 dB re noise)
bead + 220 pF (ECO)          E=10 V/m Wi-Fi 2.4                  EMIRR-10  worst 3.67e-10 uV  (-192.6 dB re noise)
bead + 220 pF (ECO)          E=10 V/m Wi-Fi 5                    EMIRR-10  worst 2.25e-11 uV  (-216.8 dB re noise)
bead + 220 pF (ECO)          E=30 V/m VHF 30-80 MHz              EMIRR-0   worst 1.21e+03 uV  ( +57.8 dB re noise)
bead + 220 pF (ECO)          E=30 V/m FM broadcast               EMIRR-0   worst      157 uV  ( +40.1 dB re noise)
bead + 220 pF (ECO)          E=30 V/m VHF 150-300 MHz            EMIRR-0   worst 1.44e+03 uV  ( +59.3 dB re noise)
bead + 220 pF (ECO)          E=30 V/m TETRA/433 ISM/DVB-T        EMIRR-0   worst     2.14 uV  (  +2.7 dB re noise)
bead + 220 pF (ECO)          E=30 V/m LTE800/GSM900              EMIRR-0   worst    0.001 uV  ( -63.8 dB re noise)
bead + 220 pF (ECO)          E=30 V/m GSM1800/DECT               EMIRR-0   worst 2.87e-09 uV  (-174.7 dB re noise)
bead + 220 pF (ECO)          E=30 V/m Wi-Fi 2.4                  EMIRR-0   worst 1.05e-09 uV  (-183.5 dB re noise)
bead + 220 pF (ECO)          E=30 V/m Wi-Fi 5                    EMIRR-0   worst 6.41e-11 uV  (-207.7 dB re noise)
bead + 220 pF (ECO)          E=30 V/m VHF 30-80 MHz              EMIRR-10  worst 3.84e+03 uV  ( +67.8 dB re noise)
bead + 220 pF (ECO)          E=30 V/m FM broadcast               EMIRR-10  worst      496 uV  ( +50.1 dB re noise)
bead + 220 pF (ECO)          E=30 V/m VHF 150-300 MHz            EMIRR-10  worst 4.56e+03 uV  ( +69.3 dB re noise)
bead + 220 pF (ECO)          E=30 V/m TETRA/433 ISM/DVB-T        EMIRR-10  worst     6.77 uV  ( +12.7 dB re noise)
bead + 220 pF (ECO)          E=30 V/m LTE800/GSM900              EMIRR-10  worst  0.00317 uV  ( -53.8 dB re noise)
bead + 220 pF (ECO)          E=30 V/m GSM1800/DECT               EMIRR-10  worst 9.09e-09 uV  (-164.7 dB re noise)
bead + 220 pF (ECO)          E=30 V/m Wi-Fi 2.4                  EMIRR-10  worst 3.31e-09 uV  (-173.5 dB re noise)
bead + 220 pF (ECO)          E=30 V/m Wi-Fi 5                    EMIRR-10  worst 2.03e-10 uV  (-197.7 dB re noise)

USB 100 Hz ripple 50 mV p-p -> ±rail 62.80 uV pk -> output 0.0247 nV; via 3V3A/VREF 7.91 nV
