ooyang0325/Hi-Res-DAC/doc/DAC_HPA_Capture_Update_Note_v1.0.docx

# DAC HPA Capture Update Note

Schematic capture v1.0 → Design Spec v1.1 / Notes v1.0 / Parts List v0.9

Author: Diego Yang (owner) Date: 27 Sep 2026 Note version: 1.0

For: the schematic engineer who captured the design in KiCad

# 1 Purpose and baseline

Your Schematic capture v1.0 (9 pages: a sheet index plus eight circuit sheets) was drawn from Design Spec v1.0, Schematic Design Notes v0.9 and Parts List v0.8. The design set is now Design Spec v1.1, Schematic Design Notes v1.0 and Parts List v0.9. This note lists what changed between the two sets and how to adjust the capture, sheet by sheet.

The connectivity reference is the Parts List v0.9 “Netlist” sheet. Its “Changes vs v0.8” sheet lists the part changes, and its “Nets” sheet gives the per-net pin counts. Where this note and the Netlist sheet appear to differ, follow the Netlist sheet and tell the owner.

Item | Capture v1.0 was built from | Current design set
Design Spec | v1.0 | v1.1
Schematic Design Notes | v0.9 | v1.0
Parts List | v0.8 | v0.9 (Netlist sheet = connectivity reference)
Designators | 483 (431 parts + 52 test pads) | 526 (474 parts + 52 one-pin test pads)
Designator changes | – | 22 removed, 65 added (all on sheet 6)
Part-number changes | – | 4 (Q623–Q626, same symbol, pinout and land)

A check of the capture PDF against the v1.0 release set found exactly its 483 designators. The capture still contains the retired leg-window stage (U601/U602, R601–R604, R607–R610, R649–R652, C601–C604, C612–C615) and none of the new parts. The capture was accurate to its baseline: every change below comes from the design update.

# 2 At a glance

Work through the sheets in the order 6, 2, 7, 4, then the rest. Sheet 6 carries almost all of the change; sheets 2 and 7 each need a small, exact edit. Every sheet also gets the new title-block reference and revision (Section 5).

Sheet | What changes | How much | Action
6 Protection, output switch | Retired leg-window stage out; per-leg over-range, low-level persistence and over-range self-test stages in; new part number on Q623–Q626 | 22 parts removed, 65 added, 4 part numbers; 23 nets added, 10 removed | Recapture (3.1)
2 USB audio bridge, CPLD, clocks | U201 pin 4 (PC15) joins N6_ORTEST | 1 pin | Remove the no-connect flag, add the label (3.2)
7 Outputs, indicators | J702 contact map from the maker drawing; J701 pad check; banner | J702: 6 pins; J701: 4 no-connect flags | Recapture J702, check J701 (3.3, 4.1, 4.2)
4 I/V converters, output legs | LEG_LP/LN/RP/RN gain the new sheet-6 loads | No part change | Confirm the leg nets leave by label (3.4)
1 USB-C input, OVP, sensing | No connectivity change; J101 footprint notes | None | Title block; footprint check (4.3)
3 ES9018K2M DAC | No change | None | Title block
5 Power domains, rails | No change | None | Title block
8 Test pads, PCB items | No change | None | Title block
Sheet index | Banner wording, title block | – | Section 5

# 3 Step-by-step changes per sheet

## 3.1 Sheet 6: protection and output switch (06_protection.kicad_sch)

Sheet 6 replaces the retired leg-window stage with two new detector types per leg and a self-test path for the over-range stages. Do the steps in order. Pin-to-net detail for every new part is in Appendix A; the former nets of every removed part are in Appendix B.

### Step 6.1 Delete the retired leg-window stage (22 parts)

Designators | Qty | Part | Role in the v1.0 set
U601, U602 | 2 | TLV1704, TI TLV1704AIPWR, TSSOP-14 | Leg-window comparators, outputs on N6_H
R601–R604 | 4 | 115 kΩ 0402 | Leg taps LEG_xx → N6_FLP/FLN/FRP/FRN
C601–C604 | 4 | 2.2 µF 0603 | Tap filters N6_Fxx → GND
R649–R652 | 4 | 100 kΩ 0402 | Series N6_Fxx → comparator inputs N6_CLP/CLN/CRP/CRN
R607–R610 | 4 | 121 kΩ, 115 kΩ, 10.0 kΩ, 10.0 kΩ, 0402 | Window threshold dividers N6_VTHP / N6_VTHN
C612–C615 | 4 | 100 nF 0402 | U601/U602 decoupling, VPOS/VNEG → GND

Delete the symbols with their wires and local labels. The ten nets N6_FLP, N6_FLN, N6_FRP, N6_FRN, N6_CLP, N6_CLN, N6_CRP, N6_CRN, N6_VTHP and N6_VTHN are left without members; remove any label that still carries one of these names. Keep N6_H: it loses only the U601/U602 output pins (1, 2, 13 and 14 of each) and keeps 18 members.

### Step 6.2 Set the new part number on Q623–Q626

Change the part-number field of Q623–Q626 from JSCJ MMBT3904 to onsemi MMBT3904LT1G (LCSC C81464). Symbol, pinout (1 B, 2 E, 3 C) and SOT-23 land stay the same, and the nets do not change. The onsemi datasheet gives VCE(sat) ≤ 0.2 V at 10 mA / 1 mA.

### Step 6.3 Place the per-leg over-range stages (U611, U612)

Each leg is tapped through 330 kΩ with a 1 nF C0G filter (τ 0.33 ms). A TLV1704 channel pair compares the tap with the upper threshold V_OR+ (N6_VORP) and the lower threshold V_OR− (N6_VORN). U611 serves the left legs, U612 the right legs. The open-collector outputs sink the reset-transistor bases through the existing timer-reset nets N6_OLP_L, N6_OLN_L, N6_OLP_R and N6_OLN_R of the pair-difference detectors (U609/U610 with Q623–Q626), so no new output net is created.

Designators | Value / part number (LCSC) | Pkg | Connection
U611, U612 | TLV1704, TI TLV1704AIPWR (C181596) | TSSOP-14 | Pin table below
R926–R929 | 330 kΩ 1 %, UNI-ROYAL 0402WGF3303TCE (C25778) | 0402 | LEG_LP/LN/RP/RN → N6_ORLP/ORLN/ORRP/ORRN
C639–C642 | 1 nF C0G 50 V, Samsung CL05C102JB5NNNC (C307441) | 0402 | N6_ORLP/ORLN/ORRP/ORRN → GND
R934 | 360 kΩ 1 %, UNI-ROYAL 0402WGF3603TCE (C45956) | 0402 | 3V3A → N6_VORP (V_OR+ divider top)
R935 | 470 kΩ 1 %, UNI-ROYAL 0402WGF4703TCE (C25790) | 0402 | N6_VORP → GND (V_OR+ divider bottom)
R936 | 470 kΩ 1 %, UNI-ROYAL 0402WGF4703TCE (C25790) | 0402 | VNEG → N6_VORN (V_OR− divider)
R937 | 470 kΩ 1 %, UNI-ROYAL 0402WGF4703TCE (C25790) | 0402 | N6_VORN → N6_ORTEST (V_OR− divider, returned to the self-test net)

U611/U612 pin table. Capture pin by pin: the outputs do not follow channel order. Channels 1 and 4 (pins 2 and 13) drive the P reset net; channels 2 and 3 (pins 1 and 14) drive the N reset net.

Pin | Name | U611 (left legs) | U612 (right legs)
1 | 2OUT | N6_OLN_L | N6_OLN_R
2 | 1OUT | N6_OLP_L | N6_OLP_R
3 | V+ | VPOS | VPOS
4 | 1IN− | N6_ORLP | N6_ORRP
5 | 1IN+ | N6_VORP | N6_VORP
6 | 2IN− | N6_VORN | N6_VORN
7 | 2IN+ | N6_ORLP | N6_ORRP
8 | 3IN− | N6_ORLN | N6_ORRN
9 | 3IN+ | N6_VORP | N6_VORP
10 | 4IN− | N6_VORN | N6_VORN
11 | 4IN+ | N6_ORLN | N6_ORRN
12 | V− | VNEG | VNEG
13 | 4OUT | N6_OLP_L | N6_OLP_R
14 | 3OUT | N6_OLN_L | N6_OLN_R

### Step 6.4 Place the low-level persistence stages (U613–U620)

Each leg gets two low-level persistence stages, one per polarity, each on a dual TLV3402 (VSSOP-8, DGK). Channel 1 compares the leg’s low-level tap (1.00 MΩ with a 3.3 nF C0G filter, τ 3.3 ms) with the threshold V_LL+ (N6_VLLP) or V_LL− (N6_VLLN) and drives its own timer node. The timer node charges from VPOS through 910 kΩ into 100 nF C0G. Channel 2 compares the timer node with GND and drives the pair-difference detector’s timer-reset net.

Designators | Value / part number (LCSC) | Pkg | Connection
U613–U620 | TLV3402, TI TLV3402IDGKR (C140314) | VSSOP-8 (DGK), 3.0 × 3.0 mm, 0.65 mm pitch | Stage table below
R930–R933 | 1.00 MΩ 1 %, UNI-ROYAL 0402WGF1004TCE (C26083) | 0402 | LEG_LP/LN/RP/RN → N6_LWLP/LWLN/LWRP/LWRN
C643–C646 | 3.3 nF C0G 50 V, FH 0603CG332J500NT (C190576) | 0603 | N6_LWLP/LWLN/LWRP/LWRN → GND
R938 | 1.00 MΩ 1 %, UNI-ROYAL 0402WGF1004TCE (C26083) | 0402 | 3V3A → N6_VLLP (V_LL+ divider top)
R939 | 100 kΩ 1 %, UNI-ROYAL 0402WGF1003TCE (C25741) | 0402 | N6_VLLP → GND (V_LL+ divider bottom)
R940 | 1.00 MΩ 1 %, UNI-ROYAL 0402WGF1004TCE (C26083) | 0402 | VNEG → N6_VLLN (V_LL− divider top)
R941 | 88.7 kΩ 1 %, UNI-ROYAL 0402WGF8872TCE (C25922) | 0402 | N6_VLLN → GND (V_LL− divider bottom)
R942–R949 | 910 kΩ 1 %, UNI-ROYAL 0402WGF9103TCE (C25800) | 0402 | VPOS → timer node (stage table)
C647–C654 | 100 nF C0G 50 V, FH 1206CG104J500NT (C46348) | 1206 | Timer node → GND (stage table)

Stage table. The stage names follow the Parts List (leg LP, LN, RP or RN; + or − polarity). Pins 1 and 6 of each IC share the timer node.

IC | Stage | Timer node (pins 1, 6) | IN1− (pin 2) | IN1+ (pin 3) | OUT2 (pin 7) | R_T / C_T
U613 | LP+ | N6_TWLPP | N6_VLLP | N6_LWLP | N6_OLP_L | R942 / C647
U614 | LP− | N6_TWLPN | N6_LWLP | N6_VLLN | N6_OLN_L | R943 / C648
U615 | LN+ | N6_TWLNP | N6_VLLP | N6_LWLN | N6_OLN_L | R944 / C649
U616 | LN− | N6_TWLNN | N6_LWLN | N6_VLLN | N6_OLP_L | R945 / C650
U617 | RP+ | N6_TWRPP | N6_VLLP | N6_LWRP | N6_OLP_R | R946 / C651
U618 | RP− | N6_TWRPN | N6_LWRP | N6_VLLN | N6_OLN_R | R947 / C652
U619 | RN+ | N6_TWRNP | N6_VLLP | N6_LWRN | N6_OLN_R | R948 / C653
U620 | RN− | N6_TWRNN | N6_LWRN | N6_VLLN | N6_OLP_R | R949 / C654

Common to all eight: pin 4 (GND) = VNEG, pin 5 (IN2+) = GND, pin 8 (VCC) = VPOS.

Three points need care. The TLV3402 GND pin goes to VNEG, not to GND. The LN and RN stages cross over: U615 (LN+) drives N6_OLN_L and U616 (LN−) drives N6_OLP_L, and U619/U620 do the same on the right; capture exactly as listed. C647–C654 must stay C0G in 1206 (the timer window needs C0G; X7R is too wide). The TLV3402 DGK pinout is checked against the TI drawing at G-3.

### Step 6.5 Place the over-range self-test (Q627, R950, R951)

The MCU tests the over-range stages through PC15 (U201 pin 4, net N6_ORTEST, Section 3.2). N6_ORTEST drives the Q627 base through R950; when Q627 conducts it pulls N6_VORP down through R951, which sets a defined positive test threshold V_OR+ of 0.086–0.141 V. In normal operation Q627 is off and R951 carries no current. N6_ORTEST is also the return of the V_OR− divider (R937).

Designator | Value / part number (LCSC) | Pkg | Pins → nets
Q627 | MMBT3904, onsemi MMBT3904LT1G (C81464) | SOT-23 | 1 (B) = N6_ORTB; 2 (E) = GND; 3 (C) = N6_ORQC
R950 | 100 kΩ 1 %, UNI-ROYAL 0402WGF1003TCE (C25741) | 0402 | 1 = N6_ORTEST; 2 = N6_ORTB (base resistor)
R951 | 10 kΩ 1 %, UNI-ROYAL 0402WGF1002TCE (C25744) | 0402 | 1 = N6_VORP; 2 = N6_ORQC (collector series resistor)

### Step 6.6 Place the decoupling (C655–C666)

All twelve are 100 nF X7R 16 V, Samsung CL05B104KO5NNNC (LCSC C1525), 0402. C659–C666 sit between VPOS and VNEG because the TLV3402 GND pin is on VNEG.

Designators | Pin 1 | Pin 2 | Decouples
C655, C657 | VPOS | GND | U611/U612 V+
C656, C658 | VNEG | GND | U611/U612 V−
C659–C666 | VPOS | VNEG | U613–U620, VCC to GND pin

### Step 6.7 Check the sheet-6 nets

After steps 6.1–6.6, sheet 6 has 23 new nets and 10 fewer. N6_ORTEST is the only new net that leaves the sheet (to sheet 2). The existing nets 3V3A (R934, R938), VPOS, VNEG, GND and N6_OLP_L / N6_OLN_L / N6_OLP_R / N6_OLN_R gain pins on this sheet, and LEG_LP/LN/RP/RN gain R926–R933. Target pin counts are in Section 6.

| Nets
Added (23) | N6_ORLP, N6_ORLN, N6_ORRP, N6_ORRN, N6_VORP, N6_VORN, N6_ORTB, N6_ORQC, N6_ORTEST (sheets 2 and 6), N6_LWLP, N6_LWLN, N6_LWRP, N6_LWRN, N6_VLLP, N6_VLLN, N6_TWLPP, N6_TWLPN, N6_TWLNP, N6_TWLNN, N6_TWRPP, N6_TWRPN, N6_TWRNP, N6_TWRNN
Removed (10) | N6_FLP, N6_FLN, N6_FRP, N6_FRN, N6_CLP, N6_CLN, N6_CRP, N6_CRN, N6_VTHP, N6_VTHN

## 3.2 Sheet 2: USB audio bridge, CPLD and clocks (02_usb_bridge.kicad_sch)

Pin | Name | Capture v1.0 | Now | Action
U201 pin 4 | PC15-OSC32_OUT | No-connect flag | N6_ORTEST (over-range self-test drive) | Remove the no-connect flag; wire pin 4 to a cross-sheet label N6_ORTEST

N6_ORTEST then has three members: U201 pin 4 here, and R937 pin 2 and R950 pin 1 on sheet 6. Use the same label type as the capture’s other cross-sheet nets. Nothing else changes on sheet 2.

## 3.3 Sheet 7: outputs and indicators (07_outputs.kicad_sch)

The capture’s J702 uses the old map (tip on pin 1, sleeve on pin 4, “Mount” GND on pins 5/6). The HRO PJ-332A drawing shows that map was wrong on pins 1–4: it would have put both driven legs on the plug’s sleeve contacts. J701 already uses the correct 12-pad G-Switch symbol and needs only a check.

Step | Action
7.1 Recapture J702 | Set the pins to the maker-drawing map (table in 4.1): 1 Sleeve → GND; 2 Ring 2 → GND; 3 Ring 1 → JACK_RP; 4 Tip → JACK_LP; 5 and 6 (break contacts) → no-connect flags. Rename the symbol pins to match the Netlist sheet.
7.2 Check J701 | Check every pad number and net against the table in 4.2. Put no-connect flags on pads 9–12. Pads 11/12 are the “Contact H” mounting tabs: no connection, but soldered.
7.3 Banner | Replace the out-of-date J702 banner text (Section 5).

Never tie J702 pins 5/6 to GND. They are break contacts that close to pins 3 and 4 when no plug is inserted. Tied to GND, they short JACK_LP and JACK_RP, which the 4.4 mm jack J701 shares, whenever the 3.5 mm jack is empty.

## 3.4 Sheet 4: I/V converters and output legs (04_iv_output_legs.kicad_sch)

No part changes. The four leg nets lose the retired taps and gain the new over-range and low-level taps on sheet 6. If LEG_LP, LEG_LN, LEG_RP and LEG_RN already leave sheet 4 by label, nothing changes on this sheet.

Net | Removed (sheet 6) | Added (sheet 6) | Pins now
LEG_LP | R601.1 | R926.1, R930.1 | 7
LEG_LN | R602.1 | R927.1, R931.1 | 7
LEG_RP | R603.1 | R928.1, R932.1 | 7
LEG_RN | R604.1 | R929.1, R933.1 | 7

## 3.5 Sheets 1, 3, 5 and 8

No part or connectivity change. Update the title block (Section 5). J101 on sheet 1 keeps its netlist; only the footprint notes in Section 4.3 apply.

# 4 Connectors and footprints

None of the footprint points below changes a net. They are listed so that the symbols carry the right footprint and paste settings before provisional placement.

Ref | Part | Footprint | Pads and holes | Paste and soldering
J701 | 4.4 mm 5-pole balanced jack, G-Switch GT-3321667P-01 (C2762984) | JLC_Imported:AUDIO-TH_GT-3321667P-01 | 12 plated slots 0.50 × 1.40 mm (+0.10/0) in 1.00 × 1.90 mm pads; two Ø1.20 mm locating holes for Ø1.00 mm pegs | Owner-fitted, hand-soldered: 12 through-hole joints including pads 11/12
J702 | 3.5 mm jack (TRRS body used with TRS plugs), HRO PJ-332A-6A (C2848643) | The JLCPCB footprint for C2848643 | Pads 1/2: plated slots 0.60 × 1.5 mm in 1.00 × 1.9 mm pads (the two GND terminals); pads 3–6: 1.6 × 1.5 mm lands; two Ø1.20 mm pegs | No F.Paste on pads 1/2 until JLCPCB confirms in writing (G-6); fallback: the owner hand-solders pads 1/2 from the bottom side
J101 | USB-C receptacle (USB 2.0), GCT USB4105-GF-A | DAC_HPA:J101_USB4105-GF-A_12lands_4stakes | 16 JLCPCB pad IDs on the 12 GCT lands (each shared land is two touching pads on one net); shell stakes S1–S4; two Ø0.65 mm NPTH | No F.Paste on S1–S4 until JLCPCB confirms in writing (G-6); fallback: the owner hand-solders S1–S4 from the bottom side before the first plug-in

Before the order, the owner asks JLCPCB whether it can solder the J101 shell stakes S1–S4 and the J702 slot pads 1/2 on a top-side Standard PCBA order, and which paste apertures or order remark it needs. The J702 reflow rating is also still open with JLCPCB (the maker drawing gives none).

## 4.1 J702 pin map (HRO PJ-332A drawing)

Pin | In capture v1.0 | Now: contact | Now: net | Note
1 | Tip (L+) → JACK_LP | Sleeve | GND | Plated slot terminal; dedicated sleeve return, ≥ 4 vias
2 | Ring 1 (R+) → JACK_RP | Ring 2 | GND | Plated slot terminal; TRRS body used with TRS plugs
3 | Ring 2 → GND | Ring 1 (R+) | JACK_RP
4 | Sleeve (GND) → GND | Tip (L+) | JACK_LP
5 | Mount → GND | Ring-1 break contact | No connection (flag) | Closed to pin 3 with no plug; never GND
6 | Mount → GND | Tip break contact | No connection (flag) | Closed to pin 4 with no plug; never GND

The map comes from the drawing’s PJ-332A-A schematic and PCB layout, and the JLCPCB footprint matches it. G-2 confirms it on two samples: continuity of tip, ring 1, ring 2 and sleeve, and the break contacts opening on insertion.

## 4.2 J701 pad map (G-Switch drawing C-GT03321667P-01)

Pad | Contact | Net | Note
1 | GND (sleeve) | GND | Dedicated sleeve return, ≥ 4 vias
2, 3 | R− | JACK_RN | Switched by K604
4, 5 | R+ | JACK_RP | Switched by K603
6 | L− | JACK_LN | Switched by K602
7, 8 | L+ | JACK_LP | Switched by K601
9 | SWITCH | No connection (flag) | No detect circuit
10 | DETECT | No connection (flag) | No detect circuit
11, 12 | EP (“Contact H” mounting tabs, Ni-plated) | No connection (flags) | Soldered; not in the maker schematic. G-2 checks whether they are common with the sleeve or bushing

The G-Switch drawing confirms the owner-approved map. G-2 confirms it on two samples, including pads 11/12. The hole and peg sizes are confirmed at the G-3 overlay.

## 4.3 J101 (sheet 1): netlist unchanged

J101 keeps the 12 composite GCT land labels plus S1–S4 in the netlist. Only the footprint carries 16 JLCPCB pad IDs, where each shared land is two touching pads on one net. The shell connects to GND through R107. G-1 (continuity on two samples) and the G-3 1:1 overlay decide the footprint.

Label (contact) | Net | Label (contact) | Net
A1/B12 (GND) | GND | B1/A12 (GND) | GND
A4/B9 (VBUS) | VBUS | B4/A9 (VBUS) | VBUS
A5 (CC1) | CC1 | B5 (CC2) | CC2
A6 (DP1) | USB_DP | B6 (DP2) | USB_DP
A7 (DN1) | USB_DN | B7 (DN2) | USB_DN
A8 (SBU1) | No connection | B8 (SBU2) | No connection
S1 (shell stake) | N1_SHIELD | S3 (shell stake) | N1_SHIELD
S2 (shell stake) | N1_SHIELD | S4 (shell stake) | N1_SHIELD

## 4.4 Open point for the owner: slot-pad copper ring

The maker slot pads leave a narrow copper ring around each plated slot. The ring is above JLCPCB’s 0.18 mm minimum, at or below its 0.25 mm recommendation, and below this design’s 0.30 mm rule. The owner decides this before the G-3 overlay. Until then, keep the J701 and J702 pads exactly as the maker drawings give them: do not enlarge the pads or shrink the slots.

Connector | Slot (mm) | Pad (mm) | Copper ring (mm) | JLCPCB min. 0.18 | JLCPCB rec. 0.25 | Design rule 0.30
J701 (all 12) | 0.50 × 1.40 (+0.10/0) | 1.00 × 1.90 | 0.25 nominal; 0.20 at +0.10 mm | Above | At (nominal); below (+0.10) | Below
J702 pads 1/2 | 0.60 × 1.5 | 1.00 × 1.9 | 0.20 | Above | Below | Below

# 5 Title block, banners and revision

Where | Capture v1.0 text | Change to
Title block, all sheets: reference | Design Spec v1.0 / Notes v0.9 / Parts List v0.8 | Design Spec v1.1 / Notes v1.0 / Parts List v0.9
Title block, all sheets: revision | Rev: Schematic capture v1.0 | Raise the revision; suggested: Rev: Schematic capture v1.1
Sheet index banner | Connector pin maps and footprint/polarity gates remain open | Suggested: J701/J702 contact maps documented from the maker drawings (G-2 confirms on two samples); G-1 to G-4 remain open
Sheet 7 banner | REVIEW ONLY: G-1 to G-4 and J702 contact map remain open | Suggested: REVIEW ONLY: G-1 to G-4 remain open; J701/J702 contact maps documented from the maker drawings, G-2 confirms on two samples

The J702 part of the sheet-7 banner is out of date: the J701 and J702 contact maps are now documented from the maker drawings, and G-2 confirms them on two samples. The gates themselves are still open (Section 7), so the review-only marking stays. The revision number and banner wording are suggestions; keep your own revision scheme if it differs.

# 6 Checks after recapture

1. Run ERC. It must be clean.
2. Export the netlist and compare it with the Parts List v0.9 Netlist sheet against the target figures below.
3. Compare the per-net pin counts with the Nets sheet; the new and changed nets are listed in the second table.
4. Check that the J701 and J702 rows (pin number, pin name, net) match the Netlist sheet exactly.

Figure | Target | Note
Designators | 526 | 474 parts + 52 one-pin test pads (TP701–TP731, TP733–TP753; TP732 counts as a part)
Nets | 247 | As on the Nets sheet, where the 43 no-connect pins form one NC entry (246 named nets + NC). A KiCad export may list each no-connect pin as its own unconnected net; exclude those before comparing
Pin rows | 1445 | 1393 component pins + 52 test-pad pins
No-connect pins | 43 | Includes J701 pads 9–12 and J702 pins 5/6
Change vs capture v1.0 | −22 / +65 | 483 − 22 + 65 = 526; plus 4 part-number changes (Q623–Q626)
ERC | Clean

Per-net targets for the new nets and for the existing nets this update touches.

Net | Pins | Members (Netlist sheet)
N6_ORLP | 4 | C639.1, R926.2, U611.4, U611.7
N6_ORLN | 4 | C640.1, R927.2, U611.8, U611.11
N6_ORRP | 4 | C641.1, R928.2, U612.4, U612.7
N6_ORRN | 4 | C642.1, R929.2, U612.8, U612.11
N6_VORP | 7 | R934.2, R935.1, R951.1, U611.5, U611.9, U612.5, U612.9
N6_VORN | 6 | R936.2, R937.1, U611.6, U611.10, U612.6, U612.10
N6_ORTB | 2 | Q627.1, R950.2
N6_ORQC | 2 | Q627.3, R951.2
N6_ORTEST | 3 | R937.2, R950.1, U201.4
N6_LWLP | 4 | C643.1, R930.2, U613.3, U614.2
N6_LWLN | 4 | C644.1, R931.2, U615.3, U616.2
N6_LWRP | 4 | C645.1, R932.2, U617.3, U618.2
N6_LWRN | 4 | C646.1, R933.2, U619.3, U620.2
N6_VLLP | 6 | R938.2, R939.1, U613.2, U615.2, U617.2, U619.2
N6_VLLN | 6 | R940.2, R941.1, U614.3, U616.3, U618.3, U620.3
N6_TWLPP | 4 | C647.1, R942.2, U613.1, U613.6
N6_TWLPN | 4 | C648.1, R943.2, U614.1, U614.6
N6_TWLNP | 4 | C649.1, R944.2, U615.1, U615.6
N6_TWLNN | 4 | C650.1, R945.2, U616.1, U616.6
N6_TWRPP | 4 | C651.1, R946.2, U617.1, U617.6
N6_TWRPN | 4 | C652.1, R947.2, U618.1, U618.6
N6_TWRNP | 4 | C653.1, R948.2, U619.1, U619.6
N6_TWRNN | 4 | C654.1, R949.2, U620.1, U620.6
N6_OLP_L (existing) | 7 | Q623.1, R916.2, U609.2, U611.2, U611.13, U613.7, U616.7
N6_OLN_L (existing) | 7 | Q624.1, R917.2, U609.1, U611.1, U611.14, U614.7, U615.7
N6_OLP_R (existing) | 7 | Q625.1, R918.2, U610.2, U612.2, U612.13, U617.7, U620.7
N6_OLN_R (existing) | 7 | Q626.1, R919.2, U610.1, U612.1, U612.14, U618.7, U619.7
LEG_LP (existing) | 7 | K601.4, R417.2, R624.1, R900.1, R904.1, R926.1, R930.1
LEG_LN (existing) | 7 | K602.4, R418.2, R625.1, R902.1, R906.1, R927.1, R931.1
LEG_RP (existing) | 7 | K603.4, R419.2, R626.1, R908.1, R912.1, R928.1, R932.1
LEG_RN (existing) | 7 | K604.4, R420.2, R627.1, R910.1, R914.1, R929.1, R933.1
JACK_LP (existing) | 5 | D701.1, J701.7, J701.8, J702.4, K601.6
JACK_LN (existing) | 3 | D703.1, J701.6, K602.6
JACK_RP (existing) | 5 | D702.1, J701.4, J701.5, J702.3, K603.6
JACK_RN (existing) | 4 | D704.1, J701.2, J701.3, K604.6
N6_H (existing) | 18 | Loses U601/U602 pins 1, 2, 13, 14; members otherwise unchanged
3V3A (existing) | 21 | Gains R934.1 and R938.1
VPOS (existing) | 67 | Changes with the removed and added sheet-6 parts
VNEG (existing) | 43 | Changes with the removed and added sheet-6 parts
GND (existing) | 286 | Changes with the removed and added sheet-6 parts; J702 now has pins 1/2 on GND instead of pins 3–6

ERC and a netlist compare confirm that the capture is consistent with the Parts List. They do not verify a connector’s physical contact map; that is G-2.

# 7 What stays on hold

The stage table is unchanged by this update.

Stage | Verdict | Condition
Schematic capture | GO | Update the capture to Parts List v0.9 as described in this note
Provisional placement | GO | 100 × 80 mm
Schematic freeze | HOLD | G-1…G-4. J701 and J702 contact maps are documented from the maker drawings and confirmed on two samples at G-2 (including J701 pads 11/12 and the J702 break contacts); J101 at G-1
Routing | HOLD | No manufacturing data from provisional connector assignments
Fabrication and assembly order | HOLD | Layout review and G-5/G-6, including JLCPCB’s written confirmation of how the J101 shell stakes S1–S4 and the J702 pads 1/2 are soldered (or the owner fallback), and the 2416 film-capacitor reflow

If G-2 finds a contact that differs from the maker drawings, the nets are revised from the G-2 record before routing.

# Appendix A Added parts (65, all on sheet 6)

Pin → net exactly as on the Parts List v0.9 Netlist sheet. Resistors are 1 %.

Ref | Value | Part number | Pkg | LCSC | Pins → nets
C639 | 1 nF C0G 50 V | Samsung CL05C102JB5NNNC | 0402 | C307441 | 1=N6_ORLP; 2=GND
C640 | 1 nF C0G 50 V | Samsung CL05C102JB5NNNC | 0402 | C307441 | 1=N6_ORLN; 2=GND
C641 | 1 nF C0G 50 V | Samsung CL05C102JB5NNNC | 0402 | C307441 | 1=N6_ORRP; 2=GND
C642 | 1 nF C0G 50 V | Samsung CL05C102JB5NNNC | 0402 | C307441 | 1=N6_ORRN; 2=GND
C643 | 3.3 nF C0G 50 V | FH 0603CG332J500NT | 0603 | C190576 | 1=N6_LWLP; 2=GND
C644 | 3.3 nF C0G 50 V | FH 0603CG332J500NT | 0603 | C190576 | 1=N6_LWLN; 2=GND
C645 | 3.3 nF C0G 50 V | FH 0603CG332J500NT | 0603 | C190576 | 1=N6_LWRP; 2=GND
C646 | 3.3 nF C0G 50 V | FH 0603CG332J500NT | 0603 | C190576 | 1=N6_LWRN; 2=GND
C647 | 100 nF C0G 50 V | FH 1206CG104J500NT | 1206 | C46348 | 1=N6_TWLPP; 2=GND
C648 | 100 nF C0G 50 V | FH 1206CG104J500NT | 1206 | C46348 | 1=N6_TWLPN; 2=GND
C649 | 100 nF C0G 50 V | FH 1206CG104J500NT | 1206 | C46348 | 1=N6_TWLNP; 2=GND
C650 | 100 nF C0G 50 V | FH 1206CG104J500NT | 1206 | C46348 | 1=N6_TWLNN; 2=GND
C651 | 100 nF C0G 50 V | FH 1206CG104J500NT | 1206 | C46348 | 1=N6_TWRPP; 2=GND
C652 | 100 nF C0G 50 V | FH 1206CG104J500NT | 1206 | C46348 | 1=N6_TWRPN; 2=GND
C653 | 100 nF C0G 50 V | FH 1206CG104J500NT | 1206 | C46348 | 1=N6_TWRNP; 2=GND
C654 | 100 nF C0G 50 V | FH 1206CG104J500NT | 1206 | C46348 | 1=N6_TWRNN; 2=GND
C655 | 100 nF X7R 16 V | Samsung CL05B104KO5NNNC | 0402 | C1525 | 1=VPOS; 2=GND
C656 | 100 nF X7R 16 V | Samsung CL05B104KO5NNNC | 0402 | C1525 | 1=VNEG; 2=GND
C657 | 100 nF X7R 16 V | Samsung CL05B104KO5NNNC | 0402 | C1525 | 1=VPOS; 2=GND
C658 | 100 nF X7R 16 V | Samsung CL05B104KO5NNNC | 0402 | C1525 | 1=VNEG; 2=GND
C659 | 100 nF X7R 16 V | Samsung CL05B104KO5NNNC | 0402 | C1525 | 1=VPOS; 2=VNEG
C660 | 100 nF X7R 16 V | Samsung CL05B104KO5NNNC | 0402 | C1525 | 1=VPOS; 2=VNEG
C661 | 100 nF X7R 16 V | Samsung CL05B104KO5NNNC | 0402 | C1525 | 1=VPOS; 2=VNEG
C662 | 100 nF X7R 16 V | Samsung CL05B104KO5NNNC | 0402 | C1525 | 1=VPOS; 2=VNEG
C663 | 100 nF X7R 16 V | Samsung CL05B104KO5NNNC | 0402 | C1525 | 1=VPOS; 2=VNEG
C664 | 100 nF X7R 16 V | Samsung CL05B104KO5NNNC | 0402 | C1525 | 1=VPOS; 2=VNEG
C665 | 100 nF X7R 16 V | Samsung CL05B104KO5NNNC | 0402 | C1525 | 1=VPOS; 2=VNEG
C666 | 100 nF X7R 16 V | Samsung CL05B104KO5NNNC | 0402 | C1525 | 1=VPOS; 2=VNEG
Q627 | MMBT3904 | onsemi MMBT3904LT1G | SOT-23 | C81464 | 1 B=N6_ORTB; 2 E=GND; 3 C=N6_ORQC
R926 | 330 kΩ | UNI-ROYAL 0402WGF3303TCE | 0402 | C25778 | 1=LEG_LP; 2=N6_ORLP
R927 | 330 kΩ | UNI-ROYAL 0402WGF3303TCE | 0402 | C25778 | 1=LEG_LN; 2=N6_ORLN
R928 | 330 kΩ | UNI-ROYAL 0402WGF3303TCE | 0402 | C25778 | 1=LEG_RP; 2=N6_ORRP
R929 | 330 kΩ | UNI-ROYAL 0402WGF3303TCE | 0402 | C25778 | 1=LEG_RN; 2=N6_ORRN
R930 | 1.00 MΩ | UNI-ROYAL 0402WGF1004TCE | 0402 | C26083 | 1=LEG_LP; 2=N6_LWLP
R931 | 1.00 MΩ | UNI-ROYAL 0402WGF1004TCE | 0402 | C26083 | 1=LEG_LN; 2=N6_LWLN
R932 | 1.00 MΩ | UNI-ROYAL 0402WGF1004TCE | 0402 | C26083 | 1=LEG_RP; 2=N6_LWRP
R933 | 1.00 MΩ | UNI-ROYAL 0402WGF1004TCE | 0402 | C26083 | 1=LEG_RN; 2=N6_LWRN
R934 | 360 kΩ | UNI-ROYAL 0402WGF3603TCE | 0402 | C45956 | 1=3V3A; 2=N6_VORP
R935 | 470 kΩ | UNI-ROYAL 0402WGF4703TCE | 0402 | C25790 | 1=N6_VORP; 2=GND
R936 | 470 kΩ | UNI-ROYAL 0402WGF4703TCE | 0402 | C25790 | 1=VNEG; 2=N6_VORN
R937 | 470 kΩ | UNI-ROYAL 0402WGF4703TCE | 0402 | C25790 | 1=N6_VORN; 2=N6_ORTEST
R938 | 1.00 MΩ | UNI-ROYAL 0402WGF1004TCE | 0402 | C26083 | 1=3V3A; 2=N6_VLLP
R939 | 100 kΩ | UNI-ROYAL 0402WGF1003TCE | 0402 | C25741 | 1=N6_VLLP; 2=GND
R940 | 1.00 MΩ | UNI-ROYAL 0402WGF1004TCE | 0402 | C26083 | 1=VNEG; 2=N6_VLLN
R941 | 88.7 kΩ | UNI-ROYAL 0402WGF8872TCE | 0402 | C25922 | 1=N6_VLLN; 2=GND
R942 | 910 kΩ | UNI-ROYAL 0402WGF9103TCE | 0402 | C25800 | 1=VPOS; 2=N6_TWLPP
R943 | 910 kΩ | UNI-ROYAL 0402WGF9103TCE | 0402 | C25800 | 1=VPOS; 2=N6_TWLPN
R944 | 910 kΩ | UNI-ROYAL 0402WGF9103TCE | 0402 | C25800 | 1=VPOS; 2=N6_TWLNP
R945 | 910 kΩ | UNI-ROYAL 0402WGF9103TCE | 0402 | C25800 | 1=VPOS; 2=N6_TWLNN
R946 | 910 kΩ | UNI-ROYAL 0402WGF9103TCE | 0402 | C25800 | 1=VPOS; 2=N6_TWRPP
R947 | 910 kΩ | UNI-ROYAL 0402WGF9103TCE | 0402 | C25800 | 1=VPOS; 2=N6_TWRPN
R948 | 910 kΩ | UNI-ROYAL 0402WGF9103TCE | 0402 | C25800 | 1=VPOS; 2=N6_TWRNP
R949 | 910 kΩ | UNI-ROYAL 0402WGF9103TCE | 0402 | C25800 | 1=VPOS; 2=N6_TWRNN
R950 | 100 kΩ | UNI-ROYAL 0402WGF1003TCE | 0402 | C25741 | 1=N6_ORTEST; 2=N6_ORTB
R951 | 10 kΩ | UNI-ROYAL 0402WGF1002TCE | 0402 | C25744 | 1=N6_VORP; 2=N6_ORQC
U611 | TLV1704 | TI TLV1704AIPWR | TSSOP-14 | C181596 | 1 2OUT=N6_OLN_L; 2 1OUT=N6_OLP_L; 3 V+=VPOS; 4 1IN−=N6_ORLP; 5 1IN+=N6_VORP; 6 2IN−=N6_VORN; 7 2IN+=N6_ORLP; 8 3IN−=N6_ORLN; 9 3IN+=N6_VORP; 10 4IN−=N6_VORN; 11 4IN+=N6_ORLN; 12 V−=VNEG; 13 4OUT=N6_OLP_L; 14 3OUT=N6_OLN_L
U612 | TLV1704 | TI TLV1704AIPWR | TSSOP-14 | C181596 | 1 2OUT=N6_OLN_R; 2 1OUT=N6_OLP_R; 3 V+=VPOS; 4 1IN−=N6_ORRP; 5 1IN+=N6_VORP; 6 2IN−=N6_VORN; 7 2IN+=N6_ORRP; 8 3IN−=N6_ORRN; 9 3IN+=N6_VORP; 10 4IN−=N6_VORN; 11 4IN+=N6_ORRN; 12 V−=VNEG; 13 4OUT=N6_OLP_R; 14 3OUT=N6_OLN_R
U613 | TLV3402 | TI TLV3402IDGKR | VSSOP-8 (DGK) | C140314 | 1 OUT1=N6_TWLPP; 2 IN1−=N6_VLLP; 3 IN1+=N6_LWLP; 4 GND=VNEG; 5 IN2+=GND; 6 IN2−=N6_TWLPP; 7 OUT2=N6_OLP_L; 8 VCC=VPOS
U614 | TLV3402 | TI TLV3402IDGKR | VSSOP-8 (DGK) | C140314 | 1 OUT1=N6_TWLPN; 2 IN1−=N6_LWLP; 3 IN1+=N6_VLLN; 4 GND=VNEG; 5 IN2+=GND; 6 IN2−=N6_TWLPN; 7 OUT2=N6_OLN_L; 8 VCC=VPOS
U615 | TLV3402 | TI TLV3402IDGKR | VSSOP-8 (DGK) | C140314 | 1 OUT1=N6_TWLNP; 2 IN1−=N6_VLLP; 3 IN1+=N6_LWLN; 4 GND=VNEG; 5 IN2+=GND; 6 IN2−=N6_TWLNP; 7 OUT2=N6_OLN_L; 8 VCC=VPOS
U616 | TLV3402 | TI TLV3402IDGKR | VSSOP-8 (DGK) | C140314 | 1 OUT1=N6_TWLNN; 2 IN1−=N6_LWLN; 3 IN1+=N6_VLLN; 4 GND=VNEG; 5 IN2+=GND; 6 IN2−=N6_TWLNN; 7 OUT2=N6_OLP_L; 8 VCC=VPOS
U617 | TLV3402 | TI TLV3402IDGKR | VSSOP-8 (DGK) | C140314 | 1 OUT1=N6_TWRPP; 2 IN1−=N6_VLLP; 3 IN1+=N6_LWRP; 4 GND=VNEG; 5 IN2+=GND; 6 IN2−=N6_TWRPP; 7 OUT2=N6_OLP_R; 8 VCC=VPOS
U618 | TLV3402 | TI TLV3402IDGKR | VSSOP-8 (DGK) | C140314 | 1 OUT1=N6_TWRPN; 2 IN1−=N6_LWRP; 3 IN1+=N6_VLLN; 4 GND=VNEG; 5 IN2+=GND; 6 IN2−=N6_TWRPN; 7 OUT2=N6_OLN_R; 8 VCC=VPOS
U619 | TLV3402 | TI TLV3402IDGKR | VSSOP-8 (DGK) | C140314 | 1 OUT1=N6_TWRNP; 2 IN1−=N6_VLLP; 3 IN1+=N6_LWRN; 4 GND=VNEG; 5 IN2+=GND; 6 IN2−=N6_TWRNP; 7 OUT2=N6_OLN_R; 8 VCC=VPOS
U620 | TLV3402 | TI TLV3402IDGKR | VSSOP-8 (DGK) | C140314 | 1 OUT1=N6_TWRNN; 2 IN1−=N6_LWRN; 3 IN1+=N6_VLLN; 4 GND=VNEG; 5 IN2+=GND; 6 IN2−=N6_TWRNN; 7 OUT2=N6_OLP_R; 8 VCC=VPOS

# Appendix B Removed parts (22, all on sheet 6)

Former pin → net as in the v1.0 release set (Parts List v0.8); see Step 6.1. Makers: Samsung (capacitors), UNI-ROYAL (R601–R604, R649–R652), YAGEO (R607–R610), TI (U601/U602).

Ref | Value | Part number | Pkg | Former pins → nets
C601 | 2.2 µF | CL10A225KO8NNNC | 0603 | 1=N6_FLP; 2=GND
C602 | 2.2 µF | CL10A225KO8NNNC | 0603 | 1=N6_FLN; 2=GND
C603 | 2.2 µF | CL10A225KO8NNNC | 0603 | 1=N6_FRP; 2=GND
C604 | 2.2 µF | CL10A225KO8NNNC | 0603 | 1=N6_FRN; 2=GND
C612 | 100 nF | CL05B104KO5NNNC | 0402 | 1=VPOS; 2=GND
C613 | 100 nF | CL05B104KO5NNNC | 0402 | 1=VNEG; 2=GND
C614 | 100 nF | CL05B104KO5NNNC | 0402 | 1=VPOS; 2=GND
C615 | 100 nF | CL05B104KO5NNNC | 0402 | 1=VNEG; 2=GND
R601 | 115 kΩ | 0402WGF1153TCE | 0402 | 1=LEG_LP; 2=N6_FLP
R602 | 115 kΩ | 0402WGF1153TCE | 0402 | 1=LEG_LN; 2=N6_FLN
R603 | 115 kΩ | 0402WGF1153TCE | 0402 | 1=LEG_RP; 2=N6_FRP
R604 | 115 kΩ | 0402WGF1153TCE | 0402 | 1=LEG_RN; 2=N6_FRN
R607 | 121 kΩ | RT0402BRD07121KL | 0402 | 1=VPOS; 2=N6_VTHP
R608 | 115 kΩ | RT0402BRD07115KL | 0402 | 1=VNEG; 2=N6_VTHN
R609 | 10.0 kΩ | RT0402BRD0710KL | 0402 | 1=N6_VTHP; 2=GND
R610 | 10.0 kΩ | RT0402BRD0710KL | 0402 | 1=N6_VTHN; 2=GND
R649 | 100 kΩ | 0402WGF1003TCE | 0402 | 1=N6_FLP; 2=N6_CLP
R650 | 100 kΩ | 0402WGF1003TCE | 0402 | 1=N6_FLN; 2=N6_CLN
R651 | 100 kΩ | 0402WGF1003TCE | 0402 | 1=N6_FRP; 2=N6_CRP
R652 | 100 kΩ | 0402WGF1003TCE | 0402 | 1=N6_FRN; 2=N6_CRN
U601 | TLV1704 | TLV1704AIPWR | TSSOP-14 | 1=N6_H; 2=N6_H; 3=VPOS; 4=N6_CLP; 5=N6_VTHP; 6=N6_VTHN; 7=N6_CLP; 8=N6_CLN; 9=N6_VTHP; 10=N6_VTHN; 11=N6_CLN; 12=VNEG; 13=N6_H; 14=N6_H
U602 | TLV1704 | TLV1704AIPWR | TSSOP-14 | 1=N6_H; 2=N6_H; 3=VPOS; 4=N6_CRP; 5=N6_VTHP; 6=N6_VTHN; 7=N6_CRP; 8=N6_CRN; 9=N6_VTHP; 10=N6_VTHN; 11=N6_CRN; 12=VNEG; 13=N6_H; 14=N6_H
