ooyang0325/Hi-Res-DAC/hardware/sim/dac_1v3_bypass_sweep.csv

frequency_hz | local_5nH_ohm | remote_20nH_ohm
100000 | 0.477758703613598 | 0.476903368619039
100167.255008615 | 0.476945845070234 | 0.476089113329385
100334.78975961 | 0.476134318660467 | 0.475276188006708
100502.604720867 | 0.475324122118707 | 0.474464590382642
100670.700361052 | 0.474515253183079 | 0.473654318192534
100839.077149614 | 0.473707709595425 | 0.47284536917545
101007.735556788 | 0.47290148910129 | 0.472037741074154
101176.676053596 | 0.472096589449922 | 0.471231431635117
101345.899111847 | 0.471293008394259 | 0.470426438608497
101515.405204138 | 0.470490743690929 | 0.469622759748144
101685.194803858 | 0.469689793100241 | 0.468820392811586
101855.268385188 | 0.468890154386179 | 0.468019335560027
102025.626423101 | 0.468091825316394 | 0.467219585758338
102196.269393365 | 0.467294803662202 | 0.466421141175056
102367.197772544 | 0.466499087198574 | 0.465623999582369
102538.412037998 | 0.465704673704133 | 0.46482815875612
102709.912667886 | 0.464911560961142 | 0.464033616475791
102881.700141168 | 0.464119746755507 | 0.463240370524507
103053.774937603 | 0.463329228876761 | 0.462448418689019
103226.137537753 | 0.462540005118067 | 0.461657758759709
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
