ooyang0325/Hi-Res-DAC/hardware/sim/ems_rf_demod.csv

10000000 | 5.52318522758982e-06 | 5.58661132509287e-06 | 6.1658494677635e-06 | 8.75075559954103e-06
10115794.542599 | 5.67268946765116e-06 | 5.73930127338054e-06 | 6.34943068140871e-06 | 9.09155722439282e-06
10232929.9228075 | 5.82732973679042e-06 | 5.89729892143279e-06 | 6.54012168195968e-06 | 9.45023376864514e-06
10351421.6667934 | 5.98730022230199e-06 | 6.06080818894258e-06 | 6.73823947423864e-06 | 9.82791768737642e-06
10471285.480509 | 6.15280283998007e-06 | 6.23004120736832e-06 | 6.94411692100784e-06 | 1.02258243090785e-05
10592537.2517729 | 6.32404735546558e-06 | 6.4052186561321e-06 | 7.15810338327619e-06 | 1.06452585671716e-05
10715193.0523761 | 6.50125190026019e-06 | 6.58657011265219e-06 | 7.38056589219594e-06 | 1.1087622306638e-05
10839269.140212 | 6.6846431157812e-06 | 6.77433441647142e-06 | 7.61188989549487e-06 | 1.15544222117264e-05
10964781.9614319 | 6.87445659316698e-06 | 6.96876004818657e-06 | 7.85248042004537e-06 | 1.20472784036501e-05
11091748.152624 | 7.0709373077242e-06 | 7.1701055237957e-06 | 8.10276327953501e-06 | 1.25679337589885e-05
11220184.5430196 | 7.27433975357983e-06 | 7.37863980492605e-06 | 8.36318594774476e-06 | 1.31182640006246e-05
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
