ooyang0325/Hi-Res-DAC/doc/DAC_HPA_Design_Spec_v0.7.docx

# USB DAC + Balanced Headphone Amplifier — Design Specification v0.7

Product requirements and architecture for a personal PCB project

Author | Date | Version | Document type
Diego Yang | 24 Sep 2026 | v0.7 (draft for review) | Product requirements + architecture

Companion documents: “Schematic Design Notes v0.6” holds the block-level circuit guidance, and “Parts List v0.5” (DAC_HPA_Parts_List_v0.5.xlsx) is the source of truth for cost. This specification states the requirements and architecture they implement.

# 1. Purpose and scope

This specification defines the requirements and architecture of a single USB-C, bus-powered Hi-Res DAC with one ESS ES9018K2M DAC chip and a balanced headphone amplifier. The outputs are a 3.5 mm unbalanced jack and a 4.4 mm balanced jack, for one headphone at a time.

v0.7 answers the sixth review round (R6-A, R6-B, R6-C and R6-D of Spec v0.6: four reviews; Appendix C). The architecture stays: CH32V307 + AGRV2K USB bridge with our own USB firmware and CPLD logic, ES9018K2M in differential current mode with one OPA2210 I/V converter per pin, 2 × OPA1622 difference-amplifier legs, LM27762 charge-pump rails and a hardware fault latch. What changed: the latch captures a PGOOD fault in ≈ 35 µs and stretches every set request (C605 moved to node F), Q609 becomes a slow interlock and the new Q611 also turns the DAC analog supply off; the DC detector is specified by its worst case (R601–R604 100 kΩ, R609/R610 10 kΩ) and a slow firmware DC tier on every leg sets the same latch; the firmware captures the fault cause first at the interrupt; VREF tracks AVCC (C421 330 pF; D401 and C422 removed); a new power order enables the legs before AVCC and turns the DAC analog supply off first, so a controlled power-down, including USB suspend, completes within 4 ms; USB suspend ≤ 2.5 mA is a v1 requirement; pop is defined separately from the DC offset; a regulator dissipation table adds a 3V3D input dropper (R519, R520) and bulk capacitor (C512); the MCU–CPLD link is SPI with chip-select framing; and the Stage 2 board carries the real regulators with dummy loads.

Goal: “best measured performance for the money”, proven by published measurements; not “beats every product”, which a hobby analyzer cannot prove (QuantAsylum itself says its QA403 won’t match a US$30,000 analyzer).

Budget: the target is ≤ 1,500 NTD per board for the 5-board sample run (what the owner actually pays: ≈ 7,500 NTD for five assembled boards at the target, including the bare PCBs and JLCPCB assembly fees); it is not a 100-unit average. Ceiling 1,700 NTD per board, set when the third oscillator was added; on 24 Sep 2026 the owner confirmed the budget is flexible as long as it does not surge. The ceiling is the hard order gate and covers every JLCPCB line of the real quote: PCBs, PCBA fees (including any fixture or other assembly line that appears in the quote) and parts; when the quote is approved, both the gated subtotal and the total payable (gated subtotal + shipping + tax from the quote) are recorded. Shipping, import tax, programmers, enclosure and proof-of-concept hardware are outside the ceiling. The sentence “A PCB assembly fixture is needed to protect and support this part during the assembly process” appears on every JLCPCB part page, including unrelated parts (checked on the OPA2209AIDR page) and an empty part-page template, so it is standard page text and not a part-specific requirement for X202 or the OPA2210; no fixture fee is expected for Economic PCBA. The current estimate is 1,650 NTD per board (8,248 NTD for five boards), a conservative planning figure (Section 6). Pending owner decision: the residual DC blind region below 0.2 V per leg (≤ 2.5 mW into 16 Ω, ≤ 1.25 mW into 32 Ω; proposed: accept; Section 5.3).

Portfolio context is kept in the repository README.

In scope for v1 | Out of scope for v1
USB-C Hi-Res DAC with a single ES9018K2M DAC chip, bus-powered from one USB-C port (data + 5 V) | DSD in v1 (stretch goal: the ES9018K2M supports DSD; depends on firmware)
Balanced headphone amplifier: 4.4 mm balanced jack plus 3.5 mm unbalanced jack (one headphone at a time) | K1000-class 1 W drive (v0.7 gives ≈ 95.9 mW into the K1000 in High mode, Section 5)
PCM 44.1–384 kHz (including 352.8 kHz; all eight rates with exact integer clock ratios), 16–32 bit, USB Audio Class 2.0 High-Speed | USB PD power
USB power modes: Default (≤ 500 mA, hardware-limited) and High (only with a ≥ 1.5 A Type-C advertisement); USB suspend ≤ 2.5 mA within 10 ms of the last bus activity | Fast rail-proximity DC detector (v2 option; a rail-stuck failure in High mode stays within the v1 energy limits)
DC-fault protection: hardware fault latch (DC detect, firmware slow DC tier, PGOOD loss, sustained overcurrent) that disables the amplifiers and turns the headphone rails and the DAC analog supply off | Output relays
Host volume in the DAC’s attenuator; per-unit level calibration at the end-of-line test | Hardware volume knob
Design automation: CI checks, BOM cost gate, DFF/DFA/DFT rules, AI datasheet review, automated measurement and calibration | Enclosure design (3D-printed case for prototypes only)

# 2. Key targets

All values below are proposed targets for v0.7, based on the ES9018K2M, OPA2210, OPA1622, LM27762 and TPS2553 datasheets and the v0.7 design calculations; every board revision is measured against this table (Section 8). Design estimates and assumptions are labelled as such; the protection limits are worst-case values.

Parameter | Target | Minimum | Conditions | How verified
PCM sample rate | 44.1–384 kHz, 16–32 bit: all eight rates (44.1, 48, 88.2, 96, 176.4, 192, 352.8 and 384 kHz) with exact integer clock ratios and a 50:50 bit clock | 384 kHz | USB Audio Class 2.0, High-Speed; DAC bit-clock duty 45:55 to 55:45 (Section 5.3); absolute rate within the oscillator tolerance (X203: ±20 ppm tolerance + ±30 ppm stability), absorbed by the asynchronous USB feedback | Host playback sweep at every rate; all eight rates bit-perfect in the proof of concept (Stage 2)
DSD | Not in v1 (stretch: the ES9018K2M supports DSD; depends on firmware) | — | — | —
Hosts | Windows 10/11 built-in UAC2 driver, macOS, Linux; Android over USB-C (High-Speed) | — | — | Host playback on each OS
THD+N at 1 kHz | ≤ −105 dB | ≤ −100 dB | Calibrated 0 dBFS, 300 Ω, both jacks, 20 Hz–20 kHz (proposed) | QA403 via Python (Section 8)
Dynamic range | ≥ 115 dB(A) | ≥ 112 dB(A) | Both jacks (estimate ≈ 119.5 dB(A) unbalanced, ≈ 120.3 dB(A) balanced; correlated I/V noise, Section 5.3) | QA403 (results recorded with the analyzer loopback floor)
Level at 0 dBFS | 1.75 Vrms unbalanced / 3.5 Vrms balanced after calibration (± 0.1 dB) | — | Per-unit master trim stored in MCU flash; before calibration −3.5 dB (≤ 1.73 Vrms), a safety setting that keeps an untrimmed highest-gain unit below the OPA2210 output swing | Automated end-of-line test (Section 7)
Output power, High mode | 3.5 mm ≥ 65 mW at 32 Ω; 4.4 mm ≥ 140 mW at 60 Ω, ≥ 85 mW at 120 Ω, ≥ 36 mW at 300 Ω (worst unit, both channels) | — | 1 kHz, both channels, worst-case rail; rated at 1 % THD+N or calibrated 0 dBFS, whichever comes first; estimates in Section 5.2 | QA403 + dummy loads
Output power, Default mode | 3.5 mm ≥ 38 mW at 32 Ω; 4.4 mm ≥ 17 mW at 60 Ω, ≥ 35 mW at 120 Ω, ≥ 36 mW at 300 Ω; 32 Ω balanced not rated (worst unit, both channels) | — | As High mode; rated by the instantaneous peak analog current within the TPS2553 Default minimum (157 mA) | QA403 + dummy loads
Output impedance | ≤ 0.5 Ω | — | 1 kHz, both jacks, including contacts | Load/no-load method, 32 Ω and 300 Ω
Frequency response | +0.1/−0.3 dB, 20 Hz–20 kHz | — | 44.1, 48 and 384 kHz sample rates; estimate −0.05 dB at 20 kHz | QA403
Crosstalk at 1 kHz | Balanced ≤ −100 dB (300 Ω); unbalanced ≤ −75 dB (32 Ω, at the jack) | — | Layout rule for the shared ground (Section 7) | QA403
Channel balance | ≤ 0.3 dB; per-channel fine trim to ±0.05 dB by MCU digital scaling at calibration | — | — | Automated end-of-line test
DC offset | ≤ ±10 mV unbalanced, ≤ ±20 mV balanced | — | Worst-case estimate 7.0 / 14.0 mV (unbalanced ≈ 3.9 mV RSS); ≤ 8.6 / 17.2 mV if the DAC null is 1.65 V (R433 option, Section 5.3); 100 % screening | Automated test on every board with a DC-capable DMM
Protection | Hardware detector, worst case: a DC fault ≥ 2 V on any leg is removed within 100 ms and ≥ 1 V within 250 ms; firmware tier (same latch): ≥ 0.8 V within 1 s and ≥ 0.2 V within 3 s; terminal energy ≤ 30 mJ at 16 Ω and ≤ 15 mJ at 32 Ω for a rail-stuck failure in High mode, worst case, including the after-trip energy (≤ 0.6 mJ); starts latched at power-up; residual below 0.2 V per leg: owner decision pending | — | Defined at the headphone terminals; removed = RAIL_EN, AMP_EN and AVCC_EN pulled low; worst case 2 V → 59 ms, 1 V → 183 ms (leg trip 0.47–0.81 V, τ 84–111 ms); energy 26.2 / 13.3 mJ worst case; no false trip for full-scale content above 9.9 Hz (hardware, worst case) and ≈ 2 Hz (firmware) | Digital DC test signal, firmware-tier test, detector test, failed-output emulation with dummy loads (worst-case envelope, no allowance), short-PGOOD-pulse test and SPICE of a failed output stage (Section 7)
Pop | ≤ 5 mV peak for controlled transitions; ≤ 20 mV peak at unplug or brownout (target) | — | Pop = peak of the transient at the jack beyond the settled DC step, band-limited 20 Hz–20 kHz (AC-coupled analyzer input); the DC before and after each transition is bounded separately by the offset limits (±10 / ±20 mV). Controlled: power-on after configuration, suspend/resume, rate and rate-family change, fault recovery; 32 Ω and 300 Ω | Oscilloscope with an AC-coupled, band-limited analyzer input
USB power and inrush | Before configuration ≤ 100 mA (estimate ≤ 83 mA); Default mode ≤ 500 mA, estimated maximum 0.469 A with hardware-limited analog current; High mode only with a ≥ 1.5 A Type-C advertisement (estimated maximum 0.754 A); attach charge ≤ 50 µC (estimate ≈ 40 µC) | — | Bus-powered descriptors (bmAttributes 0x80, bMaxPower 0xFA); the TPS2553 limits only the analog branch, the MCU, CPLD and DAC-core currents are estimates or datasheet values; attach charge at nominal capacitance, domains staggered and soft-started | Measured on the Stage 2 board before layout (gate) and on every main board: USB power meter in every state; Type-C 1.5 A source and USB-A port; charge at attach and VBUS droop at each domain enable
USB suspend | ≤ 2.5 mA within 10 ms of the last bus activity (v1 requirement) | — | Controlled power-down within 4 ms of the suspend interrupt (3 ms after the last bus activity); suspend level ≈ 7 ms after the last bus activity (3 ms margin); budget ≈ 2.2 mA, of which the MCU low-power current with USB wake-up (≤ 1.9 mA) is an assumption | Current vs time from the last bus activity, on the Stage 2 board (layout gate) and on every main board
Thermal | All parts within ratings; the board recovers | — | Overload tests, 30 min each, High mode, maximum volume (Section 7); regulator dissipation table (Section 5.3): U504 ≤ 0.20 W with the input dropper | Thermocouple / IR camera, including the regulators at bring-up
PCB | 4 layers, target ≤ 80 × 60 mm, all SMT parts on the top side except the 4.4 mm jack, 90 Ω USB pair | — | JLCPCB Economic PCBA | ERC/DRC and layout-rule checks in CI (Section 8)
Cost | ≤ 1,500 NTD per board for the 5-board run (target); ceiling 1,700 NTD per board, the hard order gate, with the owner statement of 24 Sep 2026 (estimate 1,650 NTD) | — | Every JLCPCB line of the real quote: PCBs, PCBA fees (including any fixture or other assembly line) and parts; excluding shipping, import tax, programmers, enclosure and proof-of-concept hardware | Cost gate: WARN > 1,500, FAIL > 1,700 (Section 8); the JLCPCB quote from the real BOM/CPL files must pass before ordering; gated subtotal and total payable recorded at quote approval

# 3. Architecture

## 3.1 Signal and control path

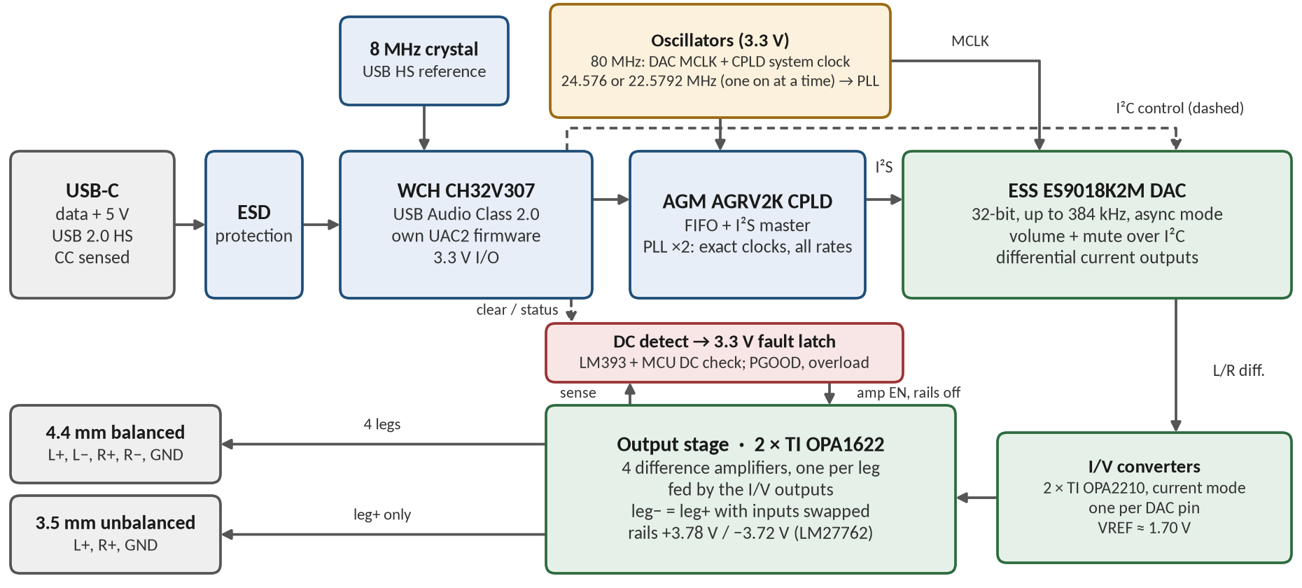
[picture p2: figure]
Block diagram of the signal and control path: a single USB-C port (USB 2.0 High-Speed data and 5 V; CC lines sensed by the MCU) with ESD protection feeds the WCH CH32V307 MCU running our own USB Audio Class 2.0 firmware, with an 8 MHz crystal as the USB High-Speed reference. Three 3.3 V oscillator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

Figure 1. Signal and control path (80 MHz oscillator for the DAC MCLK and the CPLD system clock; 24.576 MHz and 22.5792 MHz family oscillators, one at a time, into the CPLD PLL; OPA2210 I/V converters; +3.78 V / −3.72 V output legs; the LM393 DC detect, the MCU slow DC check, PGOOD and overload into the fault latch).

- The single USB-C port carries USB 2.0 High-Speed audio and the 5 V bus. D+, D− and VBUS pass through a USBLC6-2SC6 ESD array. CC1 and CC2 keep their 5.1 kΩ Rd pull-downs and also go through 10 kΩ to MCU ADC inputs, which read the Type-C current advertisement (Section 3.2).
- USB bridge: a WCH CH32V307RCT6 RISC-V MCU with a built-in USB 2.0 High-Speed PHY runs our own USB Audio Class 2.0 firmware, built on WCH’s register-level high-speed USB device examples; the CPLD logic is ours as well. The open-source USBAudioToI2S project (Apache-2.0; MCU + CPLD asynchronous USB audio) is kept only as a known-good comparison on the same hardware. v1 depends on a pre-layout firmware gate, run as a two-stage proof of concept (Section 8). The 8 MHz HSE crystal is confirmed (the firmware derives the 4 MHz USB HS PLL reference as HSE ÷ 2); the Basic 5.0 × 3.2 mm YXC X50328MSB2GI is used with 33 pF load capacitors.
- Clock: three 3.3 V oscillators on 3V3D. X201, 80 MHz (SCTF SX3M80.000B20F30TNN; ±20 ppm tolerance, ±30 ppm stability; tri-state pin 1 tied to 3V3D, so it is always enabled), drives the DAC MCLK directly and the 80 MHz CPLD system clock (SPI registers, FIFO write side), each through 33 Ω. It replaces the 100 MHz part, which sat at the ES9018K2M limit (MCLK cycle time ≥ 10 ns, pulse width high and low ≥ 4.5 ns, duty 45:55 to 55:45; datasheet “XI / MCLK Timing”). At 80 MHz the cycle is 12.5 ns and the pulse width ≥ 5.6 ns at 45:55, and 80 MHz ≈ 208 × 384 kHz (208.3; asynchronous mode needs no integer ratio), above the 192 × FSR minimum for PCM normal (asynchronous) mode (73.7 MHz at 384 kHz). The ES9018K2M runs in that mode, the one its datasheet performance is specified in; the external 1.3 V DVDD is still required (FSR > 192 kHz).
- An AGM AGRV2KQ32 CPLD makes BCLK = 64 × fs and LRCLK, and changes SDATA and LRCLK on the falling BCLK edge (≥ 20 ns half period at 24.576 MHz BCLK against the DAC’s 4.1 ns setup and 2 ns hold). X202, 24.576 MHz (YXC OT322524.576MJBA4SL), for the 48 kHz family and X203, 22.5792 MHz (SCTF SX2M22.5792M20F30TNN), for the 44.1 kHz family share one node at the CPLD’s dedicated PLL clock input, each through its own 33 Ω source termination (R210, R211). Both are off by default: R212 and R213 are 2.2 kΩ pull-downs on OSC48_EN and OSC44_EN, so neither oscillator is enabled at power-up, during CPLD configuration or reprogramming, or whenever the CPLD pins are high-impedance, and R214 (10 kΩ) holds the shared node low while both are off. Only one family oscillator drives the node at a time (a disabled output-enable oscillator may keep running internally; both are counted in the current budget). The CPLD’s single PLL doubles it to 49.152 MHz or 45.1584 MHz, divided by 2/4/8/16 for 384/192/96/48 kHz or 352.8/176.4/88.2/44.1 kHz: all eight rates have exact integer clock ratios, and the PLL ×2 also turns the oscillators’ 45–55 % duty into a 50:50 bit clock (Section 5.3). There is no PLL in the DAC MCLK path.
- Rate-family change, break-before-make, with the two enables mutually exclusive in the CPLD logic and never high in the same cycle: (1) DAC soft mute; (2) I²S output stopped (held low); (3) PLL held in reset; (4) old enable low; (5) wait ≥ 1 ms with both off; (6) new enable high; (7) wait ≥ 10 ms (start-up ≤ 3 ms X202, ≤ 5 ms X203); (8) PLL released, wait for lock; (9) output restarts, and the MCU checks the LRCLK rate with its feedback timer (within ±0.1 % of the target; otherwise it stays muted, retries once, then reports a fault); (10) DAC re-locks (lock_status, register 64) → soft unmute. After configuration the CPLD starts with both enables low and the PLL in reset, then enables X202 after ≥ 1 ms. MCLK (X201) is never touched, and both enable bits never change at the same time.
- Oscillator datasheets: the SCTF 2CM series datasheet (X203) gives pin 1 “Tri-State”, enabled when OE is logic 1 or open and disabled at logic 0 (≤ 0.3 VDD), start-up ≤ 5 ms, 10 mA max and duty 45–55 %, but no disable or enable time, internal pull-up value or disabled-output leakage; the YXC YSO110TR datasheet (X202) gives enable ≥ 70 % VDD or floating, disable ≤ 30 % VDD, start-up ≤ 3 ms, 5 mA max and duty 45–55 %, but no disable time. Both enable when pin 1 is open, so each has an internal pull-up of unknown strength: the 2.2 kΩ pull-downs keep pin 1 below 0.3 VDD against any combined pull-up ≥ 5.1 kΩ (oscillator and CPLD weak pull-up during configuration), and each enable draws 1.5 mA when driven high. Typical disable times are well under 1 µs, so the 1 ms gap is a large margin; the disable time is measured in the proof of concept. Fallback: the DNF 2:1 multiplexer U205 (74LVC1G157GW, select = OSC44_EN) with R215 33 Ω at the PLL pin and the DNF R216, R217 10 kΩ pull-downs on both mux inputs; to use it, fit U205, R215, R216 and R217 and remove R210 and R211 (with R210/R211 removed, a disabled oscillator output is high-impedance, so a mux input would otherwise float). One of the two Stage 2 boards is built with it.
- MCU → CPLD audio link: SPI with chip-select framing (MCU SPI master with DMA; one CS frame per block of samples); the 80 MHz system clock never samples the MCU’s serial clock. The CPLD captures the link in the SPI clock domain (SPI clock on a CPLD global-clock-capable input) and hands each complete 32-bit word to the 80 MHz system domain through a toggle synchronizer (word period ≥ 1.3 µs at 384 kHz, ≫ 3 system-clock cycles of 12.5 ns). I²S is not used for the link, because its frame rate is not locked to the audio rate. The FIFO stays dual-clock (written in the system domain, read in the PLL bit-clock domain, Gray-coded pointers). CPLD global clocks used: system clock (X201), PLL output and SPI clock (the AGRV2K has up to four). The payload at 384 kHz / 32-bit stereo is 24.576 Mbit/s; the CH32V307 SPI maximum clock is confirmed in Stage 1.
- The ESS ES9018K2M (32-bit, PCM to 384 kHz via I²S) is configured by the MCU over I²C (address 0x90) and runs in differential current mode. Each output pin is equivalent to a voltage source (3.05 Vpp around 1.65 V) in series with 806 Ω ±11 % (datasheet p. 31), and ESS specifies DNR and THD+N only in differential current mode, so the design follows the ESS application circuit (p. 27) with one I/V converter per pin. The MCU drives RESETB (100 kΩ pull-down) and reads the DPLL lock status.
- Signal chain: DAC (current mode) → 2 × OPA2210 I/V converters (one amplifier per DAC pin, VREF ≈ 1.70 V) → 2 × OPA1622 difference-amplifier legs → jacks, all on +3.78 V / −3.72 V. U403 serves DACL/DACLB and U404 DACR/DACRB. Each feedback is 836 Ω (1 kΩ ∥ 5.1 kΩ, 1 %) with 10 Ω + 660 pF (two 330 pF C0G in parallel), a 288 kHz pole. VREF = 1.703 V = 0.516 × 3V3A from a 15 kΩ over 15 kΩ + 1 kΩ divider (7.74 kΩ source) with C421 330 pF C0G only (τ ≈ 2.8 µs), so VREF tracks AVCC in every ramp. It sits at the DAC’s zero-DC-current point from the current-output formula (2.112 mA − 1000·Vg/806 = 0 at Vg ≈ 1.702 V); the ESS voltage-source model gives 1.65 V (AVCC/2), and R433 1 kΩ → 0 Ω sets VREF = 1.650 V if the null test on the proof boards shows that value (Section 5.3). The OPA2210 (single input pair, common-mode range (V−) + 1.5 V to (V+) − 1.5 V, Vos ±35 µV max, 2.2 nV/√Hz, 18 MHz) replaces the OPA2197, whose input-pair transition region, typically (V+) − 3 V to (V+) − 1.5 V (TI SBOS737C), contains VREF; VREF sits 0.47 V inside the common-mode range at the minimum +rail of 3.673 V (Appendix C, R5-A5). Its output swing at the ≈ 3 mA I/V load is estimated at (V+) − 0.3 V, 3.37 V at the minimum rail, against a calibrated peak of 2.94 V (0.43 V margin).
- Output stage: 2 × TI OPA1622, one amplifier per leg, with no paralleling. Each amplifier is a 4-resistor 2.00 kΩ (0.1 %) difference amplifier with 330 pF C0G (a 241 kHz pole), fed by the I/V outputs: leg+ = I/V(DAC−) − I/V(DAC+), leg− = the swap. The leg input common mode is VREF, so VREF errors are mostly common mode. U401 drives L+ and L−, U402 drives R+ and R−. The clean output envelope is ≤ 80 mA peak per leg within the OPA1622 swing curve (Section 5).
- Protection: an LM393 window comparator detects DC on any leg (worst-case leg trip 0.47–0.81 V, τ 84–111 ms) and sets an N-MOSFET fault latch on the always-on 3V3M domain; PGOOD-bad (Q610) and a sustained TPS2553 overcurrent (FAULT through D606, after its 5–10 ms deglitch) set it too. C605 sits on node F, so the latch captures a PGOOD fault in ≈ 35 µs (budget 0.1 ms), every set request is stretched to 1.5–7.4 ms, and the board powers up latched. The latch pulls RAIL_EN (LM27762 EN+/EN−), AMP_EN (both OPA1622 EN pins) and, through Q611, AVCC_EN (LP5907) low and stays set until the firmware clears it (FLT_CLR). Q609 is a slow static interlock (on 6–32 ms after PGOOD goes bad) that keeps AMP_EN low whenever the rails are off, so a short PGOOD glitch either latches or does nothing. A slow firmware tier reads every leg through its own 1 MΩ network on an MCU ADC pin and sets the same latch through ANA_FAULT and D606 (≥ 0.8 V within 1 s, ≥ 0.2 V within 3 s); at the FLT interrupt the firmware first stores the leg readings and the fault flags, which identify the cause. The set path is armed 25–133 ms after PGOOD goes good, without clearing the latch; there are no relays (Section 5.3).
- The 4.4 mm balanced jack carries L+, L−, R+, R− and GND; the 3.5 mm unbalanced jack carries L+, R+ and GND. Both jacks are live, so only one headphone is connected at a time.

## 3.2 Power path

- The single USB-C port supplies data and 5 V; the board is bus-powered (bmAttributes 0x80, bMaxPower 0xFA = 500 mA). Only 5 × 1 µF sit on VBUS before any switch (connector and the inputs of ME6211 #1, ME6211 #2, LP5907 and TPS2553). At attach only 3V3M starts (4.4 µF behind it, including C212, C605, C606 and C607), so the attach charge is ≈ 40 µC against the 50 µC USB-IF limit (nominal values; DC-bias derating lowers the real figure).
- 3V3M, always on: ME6211C33 #1 (U502) powers the MCU, the fault latch, the slow DC-sense networks and the LEDs. Before USB configuration only this domain runs (62 / 83 mA typical / maximum estimate; assumption on the MCU current).
- 3V3D, switched: ME6211C33 #2 (U504, CE = AUD_EN) is fed through R519 + R520 (2 × 2.2 Ω 0805 in series, 4.4 Ω), which move ≈ 0.11 W out of the LDO (U504 ≤ 0.20 W at VBUS 5.25 V against the ME6211’s 300 mW SOT-23 rating; LDO input ≥ 3.71 V at VBUS 4.40 V), and C512 10 µF is its bulk capacitor. It powers the CPLD, the three oscillators (80 MHz, 24.576 MHz and 22.5792 MHz), the I²C pull-ups and the DAC DVCC (through the GZ1608D601TF ferrite, ≈ 14 mA). A fixed, ceramic-stable 1.3 V LDO (ME6216A13M3G, ±1 %, 300 mA) fed from 3V3D makes the external DVDD, so DVDD cannot exceed DVCC during the ramps.
- 3V3A, switched: the LP5907-3.3 (EN = AVCC_EN, also pulled low by the latch through Q611) supplies VCCA, AVCC_L/AVCC_R and the VREF divider. VREF = 0.516 × 3V3A with only C421 330 pF (τ ≈ 2.8 µs), so VREF follows AVCC: the lag is ≤ 4 mV in controlled ramps (3V3A falls through the LP5907’s 230 Ω output auto-discharge) and ≤ 0.15 V for a few microseconds at the fastest unplug slope (0.1 V/µs). D401 and C422 are removed.
- Headphone rails: a TI TPS2553 current-limited switch (EN = ANA_EN; built-in soft start; FAULT open drain with a 5/7.5/10 ms deglitch) feeds 5V_ANA through the Murata BLM18PG121SN1D ferrite (2 A, 50 mΩ) to the LM27762, which makes +3.780 V (3.673–3.890 V) and −3.722 V (3.618–3.828 V magnitude), both ranges including VFB and the 1 % divider resistors, with 215 kΩ/100 kΩ and 205.1 kΩ/100 kΩ feedback. Each top resistor is built from Basic values: 100 kΩ + 100 kΩ + 15 kΩ, and 100 kΩ + 100 kΩ + 5.1 kΩ (R518). EN = RAIL_EN; PGOOD (95 % thresholds +3.59 V / −3.54 V) goes to the MCU, the fault latch (Q610) and the Q609 interlock.
- Current limit: RILIM = 100 kΩ + 47 kΩ = 147 kΩ gives the Default limit (157 / 183 / 213 mA minimum / nominal / maximum, including 1 % resistors); a 2N7002 switches 100 kΩ in parallel for High mode (59.5 kΩ: 393 / 442 / 498 mA). The TPS2553 acts on the instantaneous current (short-circuit response ≈ 2 µs, then constant-current limiting) and limits only the analog branch, so the board figures are estimated maxima with hardware-limited analog current: 0.469 A in Default mode (31 mA below 0.5 A) and 0.754 A in High mode. High mode is used only when the Type-C advertisement read on CC1/CC2 is ≥ 1.5 A (bands: Default 0.25–0.61 V, 1.5 A 0.70–1.16 V, 3.0 A 1.31–2.04 V). A USB-A-to-C cable reads as Default, and many phones limit OTG to ≤ 500 mA and run in Default mode.
- CC monitoring (firmware requirement): while configured, the MCU samples CC1/CC2 at least every 5 ms and treats a change as valid after tRpValueChange (10–20 ms). On a drop from ≥ 1.5 A to Default it soft-mutes, sets ILIM_HI low and continues in Default mode within tSinkAdj (60 ms max) of the change; it switches up to High only after the new advertisement is stable (USB Type-C timing, as quoted in the Zephyr USB-C stack and the Chromium EC documentation).
- Supply headroom at the design corner (VBUS 4.60 V at the receptacle: host minimum 4.75 V minus 150 mV cable and connector drop, assumption): LM27762 VIN 4.544 V with the TPS2553 (135 mΩ max), the ferrite (60 mΩ) and traces (20 mΩ) in the path. At the worst clean load (4.4 mm 32 Ω, High mode, 80 mA per leg; negative-rail peak 184 mA, average analog input 260 mA) the negative-rail capability is −3.936 V, 0.11 V beyond the maximum |V−| of 3.828 V, and the positive 4.460 V, 0.57 V above the maximum V+ of 3.890 V, with a 3.0 Ω charge-pump resistance (assumption; 2.5 Ω is specified only at 5.5 V). With the v0.5 divider and resistor tolerance this margin would have been only 46 mV. At the 4.40 V stress corner (VIN 4.344 V) the negative rail is 92 mV short at current peaks (brief dropout, measured on the bench), while the positive rail keeps 0.37 V.
- VBUS sense: 100 kΩ / 47 kΩ into an ADC (5.0 V → 1.60 V) with an analog watchdog at 4.10 V nominal (3.95–4.25 V with the ADC reference 3V3M ±2 %, the divider ±1.4 % and the ADC error: ≥ 0.15 V below the 4.40 V stress corner and ≥ 0.35 V below the 4.60 V design corner). On unplug or brownout it drops AMP_EN and RAIL_EN (target < 5 µs); the PGOOD latch is the backstop. At 0.47 A with ≈ 4.5 µF on VBUS, VBUS falls at up to ≈ 0.1 V/µs: 4.10 V → 3.46 V (3.3 V LDO dropout) in ≈ 6 µs, so the watchdog has ≈ 1 µs margin; PGOOD goes bad at VBUS ≈ 3.70 V and sets the latch. At full load the logic rails may droop before the sequence completes, so the unplug pop stays a measured target (≤ 20 mV peak), and the watchdog-to-GPIO latency is measured on the Stage 2 board. DAC-pin safety does not depend on this timing, because VREF tracks AVCC: at a sudden unplug the DAC pins are at most ≈ 0.15 V above AVCC for microseconds, below the voltage at which a silicon protection junction conducts (ES9018K2M absolute maximum: GND < Vout < AVCC; bench check TP709 VREF vs TP710 AVCC_L).
- Power sequence (steps in Section 5.3): power-up enables the legs while AVCC is still off (VREF = 0 V), then AVCC_EN, so VREF rises in common mode while the legs hold the jack at ≈ 0 V. Controlled power-down, including USB suspend, takes ≤ 4 ms: at t0 (the suspend interrupt, 3 ms after the last bus activity, or a host or fault command) soft mute, then RESETB, AVCC_EN and AUD_EN low together, so the DAC turns off first while the I/V converters and legs stay powered and hold ≈ 0 V; 3V3A falls below 0.3 V within ≈ 3.2 ms and VREF follows. At t0 + 3.5 ms AMP_EN goes low, then RAIL_EN and ANA_EN (the rails decay on their own, and nothing is left that could back-power the I/V stage); at t0 + 4 ms the MCU enters low-power mode, and the VBUS current reaches the suspend level ≈ 7 ms after the last bus activity (USB limit 10 ms, 3 ms margin). No “rails off, DAC powered” window remains in a controlled sequence; the latch sets as the rails go off, which the firmware expects and masks.
- Fault shutdown: when the latch sets, Q607, Q608 and Q611 pull RAIL_EN, AMP_EN and AVCC_EN low within ≈ 35 µs. 3V3A collapses within ≈ 3.2 ms, about when the I/V rails (≈ 13 mA load with the amplifiers off) fall to the OPA2210 minimum supply (≈ 3.6 ms); any residual back-power is ≤ 1.7 mA per DAC pin (806 Ω − 11 %), inside the OPA2210’s 10 mA input-current rating (TI datasheet, absolute maximum ratings and section 7.3.5). The firmware then sets RESETB, AUD_EN and ANA_EN low.

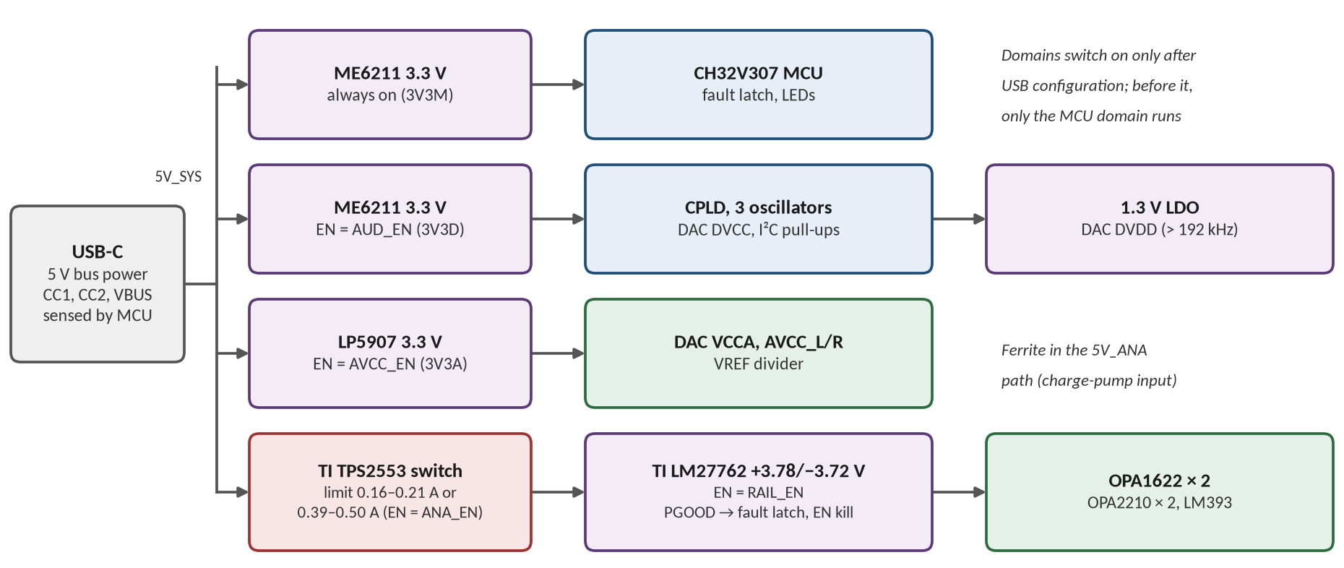
[picture p3: figure]
Power path diagram: the USB-C 5 V bus power (CC1, CC2 and VBUS sensed by the MCU) feeds four branches. An ME6211 3.3 V LDO is always on (3V3M) for the CH32V307 MCU, the fault latch and the LEDs. A second ME6211 3.3 V LDO, enabled by AUD_EN (3V3D), supplies the CPLD, the three oscillators (80 MHz, 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

Figure 2. Power path (switched power domains with the three oscillators on 3V3D, TPS2553 current limit, LM27762 +3.78 V / −3.72 V rails; PGOOD and the TPS2553 overcurrent flag set the fault latch).

## 3.3 Volume, gain and level

Gain is fixed. Volume comes from the host via USB Audio Class (Feature Unit volume and mute) and is applied in the ES9018K2M attenuator (0 to −127.5 dB in 0.5 dB steps), with MCU fine scaling for channel trim; a hardware knob is out of scope. Per leg, L = (Rf/Rs) × 2.156 Vrms with Rf = 836 Ω and Rs = 806 Ω ±11 %: nominal 2.236 Vrms, unit spread 1.955–2.589 Vrms including Rf 1 % and AVCC ±2 %. Every unit is therefore calibrated to 1.75 Vrms per leg at 0 dBFS with the ES9018K2M 32-bit master trim, stored in MCU flash at the automated end-of-line test.

Parameter | Value | Basis
Calibrated full scale | 1.75 Vrms per leg (2.475 V peak): 3.5 mm 1.75 Vrms, 4.4 mm 3.5 Vrms | End-of-line calibration to ± 0.1 dB
Master trim | −0.96 dB (lowest-gain unit) to −3.40 dB (highest-gain unit); nominal −2.13 dB | ES9018K2M 32-bit master trim, stored in MCU flash
Before calibration | −3.5 dB, so ≤ 1.73 Vrms on any unit (2.92 V peak at the I/V output) | Firmware safety default, active until a calibration is stored: an untrimmed highest-gain unit at 0 dBFS would reach 3.53 V at the I/V output and clip
Channel trim | ±0.05 dB | MCU digital scaling
Output envelope | ≤ 80 mA peak per leg; Vpk ≤ (|rail|min − 0.9 V)/(1 + 8 Ω/Rleg) | OPA1622 Fig. 38/39 (typical, 25 °C); bench-verify at +3.78 V / −3.72 V

# 4. Key parts

Part | Role | Key specs | Package / assembly note | Unit price (run tier) | Source
WCH CH32V307RCT6 | USB audio bridge (MCU) | 144 MHz RISC-V, 3.3 V; built-in USB 2.0 High-Speed PHY; runs our own UAC2 firmware; sends the samples to the CPLD over SPI with chip-select framing (MCU master, DMA); ADC inputs for CC, VBUS and the four slow DC-sense channels | LQFP-64, 10 × 10 mm; leaded; JLCPCB Extended | US$3.45 | LCSC C2988083 (119 in stock; reserve)
AGM AGRV2KQ32 | CPLD: FIFO, I²S master, oscillator enables, bit clocks for all eight rates | 2K LUTs; one PLL (×2 on the selected family oscillator: 49.152 or 45.1584 MHz); 80 MHz system clock; SPI link captured in the SPI clock domain; up to four global clocks (three used); 3.3 V LVCMOS; JTAG/ISP; instant-on non-volatile | QFN-32, 4 × 4 mm; leadless, X-ray fee; Extended | US$1.65 | LCSC C18208899 (980 in stock)
SCTF SX3M80.000B20F30TNN (X201) | 80 MHz: DAC MCLK and the CPLD system clock (always enabled) | 3.3 V CMOS; ±20 ppm tolerance, ±30 ppm stability; 40 mA max (SCTF 3C datasheet, 80–160 MHz); duty 45–55 %; tri-state pin 1 tied to 3V3D; 12.5 ns cycle and ≥ 5.6 ns pulse width at 45:55 against the DAC limits of ≥ 10 ns and ≥ 4.5 ns | 3.2 × 2.5 mm, 4-pad; leadless, X-ray fee (counted conservatively); JLCPCB Extended | US$0.8916 (1+) | LCSC C5179978 (2,503 in stock); replaces the 100 MHz YXC part (C4353707)
YXC OT322524.576MJBA4SL (X202) | 24.576 MHz: 48 kHz family, OSC48_EN (off by default through the R212 2.2 kΩ pull-down; PLL ×2 = 49.152 MHz) | 1.8–3.3 V CMOS; tri-state pin 1 (YXC YSO110TR datasheet: enable ≥ 70 % VDD or floating, disable ≤ 30 % VDD; no disable time specified); start-up ≤ 3 ms; 5 mA max; duty 45–55 %; ±10 ppm tolerance, ±20 ppm stability; 33 Ω (R210) into the shared PLL input node | 3.2 × 2.5 mm, 4-pad; leadless, X-ray fee (counted conservatively); Extended assumed (class not shown on the JLCPCB page; its fixture sentence is standard page text) | US$0.51 | LCSC C2831388 (1,755 in stock)
SCTF SX2M22.5792M20F30TNN (X203) | 22.5792 MHz: 44.1 kHz family, OSC44_EN (off by default through the R213 2.2 kΩ pull-down; PLL ×2 = 45.1584 MHz) | 1.62–3.63 V CMOS; pin 1 “Tri-State” (SCTF 2CM datasheet: enabled when OE is logic 1 or open, disabled at logic 0, ≤ 0.3 VDD; no disable or enable time, internal pull-up value or disabled-output leakage specified); start-up ≤ 5 ms; 10 mA max; duty 45–55 %; ±20 ppm tolerance, ±30 ppm stability; 33 Ω (R211) into the shared PLL input node | 2.5 × 2.0 mm, 4-pad; leadless, X-ray fee (counted conservatively); Extended (JLCPCB part page) | US$0.55 | LCSC C5452663 (1,426 in stock)
ESS ES9018K2M | DAC | 32-bit; PCM to 384 kHz; DNR 127 dB-A and THD+N −120 dB (datasheet, current mode); each pin ≈ 3.05 Vpp source behind 806 Ω ±11 %; asynchronous (PCM normal) mode needs MCLK > 192 × FSR, MCLK cycle ≥ 10 ns and pulse width ≥ 4.5 ns; external 1.3 V DVDD above 192 kHz (50 mA at MCLK 80 MHz and 192 kHz); output pins GND < Vout < AVCC (absolute maximum); I²C 0x90/0x92; attenuator 0 to −127.5 dB in 0.5 dB steps; 32-bit master trim | QFN-28, 5 × 5 mm; leadless, X-ray fee; Extended | US$3.47 | LCSC C2688377 (724 in stock; reserve); ESS datasheet v3.7
TI OPA2210IDR (× 2, U403 and U404) | I/V converters, one amplifier per DAC pin | Single input pair, common-mode range (V−) + 1.5 V to (V+) − 1.5 V (VREF 0.47 V inside at the minimum +rail); Vos ±35 µV max; 2.2 nV/√Hz; 18 MHz; 2.2 / 2.5 mA per channel; ±2.25 V to ±18 V; output swing ≈ (V+) − 0.3 V at the ≈ 3 mA I/V load (estimate; TI: (V+) − 0.2 V at 10 kΩ, (V+) − 0.6 V at 600 Ω), 0.43 V margin at the calibrated peak; input current 10 mA (absolute maximum); same dual pinout as the OPA2197 it replaces | SOIC-8; leaded; Extended; the fixture sentence on its JLCPCB page is standard text on every part page | US$1.0035 (JLCPCB 10+; 1+ US$1.2180, 100+ US$0.7530) | LCSC C1849415; JLCPCB available 76 (reserve 12: 10 + 2 spares); no qualified second source (OPA2209AIDR: JLCPCB stock 0, US$6.11 at 1+; OPA1612: common-mode limit (V+) − 2 V = 1.67 V at the minimum rail, below VREF 1.703 V); LCSC price US$2.67 at 10+ would give ≈ 1,755 NTD per board; TI SBOS924H
TI OPA1622IDRCR (× 2) | Output legs, one amplifier per leg | Vos ±0.5 mV max; Isc +145/−130 mA typ; swing to (rail − 0.8…0.9 V) at light load, falling ≈ 8 Ω × Iout; current limit ≈ 110–120 mA at 85 °C die; EN threshold ≈ 0.82 V referenced to its GND pin; continuous short rated for one amplifier per package; θJA 47.6 °C/W | VSON-10, 3 × 3 mm; leadless, X-ray fee; thermal pad to V−; Extended | US$1.79 (10+ tier) | LCSC C2876559; TI SBOS727B
TI LM27762DSSR | +3.78 V / −3.72 V headphone rails | VOUT+ = 1.2 V × (R1 + R2)/R2, VOUT− = −1.22 V × (R3 + R4)/R4: +3.780 V (3.673–3.890 V) and −3.722 V (3.618–3.828 V magnitude) including VFB and the 1 % resistors; ±250 mA; negative LDO dropout 30 mV and positive 45 mV at 100 mA; input current limit 500 mA typ; PGOOD open drain, low = both outputs ≥ 95 % (+3.59 V, −3.54 V), sets the latch (Q610) and drives the Q609 interlock; ≈ 0.22 W at the worst clean load (θJA checked at layout); 50 kΩ output pull-down in shutdown (not relied on) | WSON-12, 2 × 3 mm; leadless, X-ray fee; Extended | US$1.10 | LCSC C473398; TI SNVSAF7C
TI TPS2553DBVR | Current-limited switch for 5V_ANA (Default and High limits) | Limit set by RILIM (15–232 kΩ), acting on the instantaneous current (short-circuit response ≈ 2 µs, then constant-current limiting); rDS(on) 85 mΩ typ / 135 mΩ max; 9 mW in normal use, ≤ 2.6 W into a short for ≤ 10 ms before the latch or FAULT path acts (thermal shutdown protects); soft start; FAULT open drain, 5/7.5/10 ms deglitch, also sets the fault latch through D606; auto-retry version kept (the latch-off TPS2553-1 is listed as not recommended for new designs) | SOT-23-6; leaded; Extended | US$0.60 | LCSC C55266; TI SLVS841F
Microne ME6216A13M3G | 1.3 V external DVDD (from 3V3D) | Fixed 1.3 V, ±1 %, 300 mA, ceramic-stable, 6 µA Iq | SOT-23; leaded; Extended | US$0.06 | LCSC C236662 (≈ 410 in stock; reserve)
Murata BLM18PG121SN1D | 5V_ANA power ferrite | 120 Ω at 100 MHz; 2 A; 50 mΩ | 0603; JLCPCB Basic | US$0.016 | LCSC C14709

Not in the table: U205, a Nexperia 74LVC1G157GW,125 2:1 logic multiplexer (LCSC C135822, SOT-363, Extended), with R215 (33 Ω) and the R216/R217 10 kΩ input pull-downs, forms a DNF fallback footprint at the CPLD PLL clock input (select = OSC44_EN). To use it, fit U205, R215, R216 and R217 and remove R210 and R211; one of the two Stage 2 boards is built with it fitted.

All other parts are chosen in Schematic Design Notes v0.6 (part number, LCSC number, stock and price). Parts List v0.5 is the source of truth for cost; every line’s JLCPCB class is taken from its JLCPCB part page or the basic-parts list, except X202, whose class is not shown (assumed Extended).

# 5. Headphone drive and estimates

## 5.1 Load requirements

Current limits the low-impedance loads. The clean output envelope is ≤ 80 mA peak per leg within the OPA1622 swing; overload behaviour is handled separately by the TPS2553 current limit and the fault latch (Section 5.3). The OPA1622’s +145/−130 mA figure is a typical short-circuit current and its current limit is ≈ 110–120 mA at an 85 °C die, so neither is a linear output rating.

Requirement | Value | Basis
Loads | 16–600 Ω on both jacks | Load matrix in Section 5.2
Clean envelope | ≤ 80 mA peak per leg | One amplifier per leg (U401 = L+/L−, U402 = R+/R−)
Swing model | Vpk ≤ (|rail|min − 0.9 V)/(1 + 8 Ω/Rleg) | OPA1622 Fig. 38/39, typical, 25 °C; extrapolated to the worst-case rail |rail|min = 3.618 V (bench-verify)
Rails | +3.780 V (3.673–3.890 V), −3.722 V (−3.618 to −3.828 V) | LM27762 feedback reference (VFB) and the 1 % divider resistors
Full-scale level | 1.75 Vrms per leg (2.475 V peak) after calibration | Section 3.3
Output impedance | < 0.1 Ω plus jack contacts (the OPA1622 legs drive the jacks directly, no ballast); target ≤ 0.5 Ω on both jacks | Estimate
Reference headphones | HIFIMAN Susvara (60 Ω, 83 dB/mW); AKG K1000 (120 Ω, 74 dB/mW) | Maker specifications; SPL in Section 5.2

## 5.2 Output power and SPL

Rated power is defined at 1 kHz, both channels driven, at 1 % THD+N or calibrated 0 dBFS, whichever comes first, for the worst-case unit on the worst-case rail (|rail|min = 3.618 V; swing model Vpk ≤ (|rail|min − 0.9 V)/(1 + 8 Ω/Rleg), 80 mA clean envelope; calibrated full scale 1.75 Vrms per leg, 2.475 V peak). Default mode is now rated by the instantaneous peak current, because the TPS2553 limits instantaneous current: quiescent (53 mA max) + 2 × Ipk (unbalanced, both channels on one rail) or + 2 × Ipk × (1 + 1.03) (balanced, both rails) must stay ≤ 157 mA, the Default minimum. v0.5 used the average current, which overstated Default power. High-mode peaks stay below the 393 mA High minimum (worst 378 mA at 4.4 mm 32 Ω). Estimates, with the limiting factor in brackets:

Load | High mode (limit) | Default mode (limit) | Analog input current, average / instantaneous peak
3.5 mm 16 Ω | 51.2 mW (80 mA envelope) | 21.6 mW (Default limit) | 156 / 213 mA
3.5 mm 32 Ω | 73.9 mW (swing) | 43.1 mW (Default limit) | 141 / 189 mA
3.5 mm 60 Ω | 47.9 mW (swing) | 47.9 mW (swing) | 105 / 133 mA
3.5 mm 300 Ω | 10.2 mW (full scale) | 10.2 mW (full scale) | 64 / 70 mA
4.4 mm 32 Ω | 102.4 mW (80 mA envelope) | 10.5 mW (Default limit) | 260 / 378 mA
4.4 mm 60 Ω | 153.5 mW (swing) | 19.6 mW (Default limit) | 238 / 343 mA
4.4 mm 120 Ω | 95.9 mW (swing) | 39.2 mW (Default limit) | 156 / 215 mA
4.4 mm 300 Ω | 40.8 mW (full scale) | 40.8 mW (full scale) | 96 / 120 mA
4.4 mm 600 Ω | 20.4 mW (full scale) | 20.4 mW (full scale) | 74 / 87 mA

SPL from the maker sensitivity, 4.4 mm balanced at the rated power (estimates). The swing margin at full scale is small: at 120 Ω balanced (K1000) and 3.5 mm 60 Ω the worst-case unit reaches the swing limit 0.27 dB below full scale (nominal unit +0.05 dB), so these loads are rated as swing-limited and bench-verified, because the swing model is extrapolated from typical curves.

Headphone | Impedance, sensitivity | High mode: power, SPL | Default mode: power, SPL | Limit (High / Default)
HIFIMAN Susvara | 60 Ω, 83 dB/mW | 153.5 mW, ≈ 104.9 dB SPL | 19.6 mW, ≈ 95.9 dB SPL | Swing / Default limit
AKG K1000 | 120 Ω, 74 dB/mW | 95.9 mW, ≈ 93.8 dB SPL | 39.2 mW, ≈ 89.9 dB SPL | Swing / Default limit

## 5.3 Power, offset, noise, bit clock, thermal and protection

USB current per state (estimates at 5 V, typical / maximum). The TPS2553 limits only the analog branch; the MCU, CPLD and DAC-core currents are estimates or datasheet values, so the Default- and High-mode figures are estimated maxima with hardware-limited analog current. Digital loads: MCU 60 / 80 mA (assumption); LEDs, latch and pull-ups 2 / 3 mA; CPLD 15 / 25 mA (assumption); X201 80 MHz 15 / 40 mA (SCTF 3C datasheet: 40 mA max for 80–160 MHz; typical assumed); X202 3 / 5 mA; X203 5 / 10 mA (both family oscillators counted); DAC DVCC 13.5 / 14.2 mA; DAC external DVDD 50 / 60 mA (datasheet 50 mA at MCLK 80 MHz and 192 kHz; +20 % for 384 kHz and spread); AVCC_L + AVCC_R + VCCA + VREF divider 17 / 17.5 mA; enable and node pull-downs 1.6 / 1.7 mA:

State | Powered domains | Current | Limit / note
Attached, not configured | 3V3M only (MCU, latch, LEDs) | 62 / 83 mA | ≤ 100 mA unit load; measured on the Stage 2 board before layout (assumption on the MCU current)
Configured, idle | 3V3M, 3V3D, 3V3A and the headphone rails | 227 / 309 mA | Digital 182 / 256 mA + analog quiescent 45 / 53 mA (the OPA2210 adds ≈ 10 mA)
Playing, Default mode | All; analog current ≤ TPS2553 Default limit | Estimated maximum 0.469 A (0.256 + 0.213 A) | ≤ 500 mA with hardware-limited analog current (31 mA below 0.5 A); Stage 2 measurement is a layout gate
Playing, High mode | All; analog current ≤ TPS2553 High limit | Estimated maximum 0.754 A | Only with a ≥ 1.5 A Type-C advertisement; CC monitored while configured
Suspend | 3V3M only: MCU in low-power mode with USB wake-up; audio domains, DAC analog supply and rails off | Requirement ≤ 2.5 mA within 10 ms of the last bus activity; budget ≈ 2.2 mA | v1 requirement. Budget (mA): MCU low-power with USB wake-up ≤ 1.9 (assumption, measured); latch pull-up 0.07; node F pull-up 0.07; node S pull-up 0.03; VBUS divider 0.03; 3V3M LDO quiescent 0.04; slow DC-sense networks 0.007; regulators off 0.003; PGOOD pull-up 0.03. Current vs time measured on the Stage 2 board (gate) and on every main board

Analog input current per load, average / instantaneous peak, is listed in the power table (Section 5.2); the worst clean load is 4.4 mm 32 Ω in High mode (260 / 378 mA), which is why 32 Ω balanced is not rated in Default mode. The analog quiescent current is 45 / 53 mA (the OPA2210 adds ≈ 10 mA), and the analog input power is ≤ 1.06 W in Default mode and ≤ 2.49 W in High mode.

DC offset per leg, worst case at 25 °C with datasheet maxima (VREF at the design value 1.703 V):

Term | Per leg | Basis
Common-mode leakage | 3.40 mV | VREF 1.703 V × 0.2 % (0.1 % resistors, gain 1)
OPA1622 Vos | 1.00 mV | 0.5 mV max × 2
OPA1622 Ios | 0.10 mV | Ios × 1 kΩ × 2
OPA2210 Vos | 0.15 mV | 35 µV max × noise gain ≤ 2.17 × 2 (two amplifiers)
DAC pin-to-pin DC mismatch | 1.18 mV | ≤ 1 mV (assumption, measure) × Rf/Rs
VREF-to-null error | 1.17 mV | Divider tolerance and an assumed ±20 mV null-point uncertainty, × 3 % pair-gain mismatch
Total, unbalanced | ≤ 7.0 mV worst (≈ 3.9 mV RSS) | Limit ±10 mV (margin 3.0 mV); ≤ 8.6 mV if the DAC null is 1.65 V
Total, balanced | ≤ 14.0 mV worst | Limit ±20 mV (margin 6.0 mV; ≤ 17.2 mV if the DAC null is 1.65 V): 20 mV into 16 Ω balanced = 25 µW DC

Every board’s offset is measured by the automated test with a DC-capable DMM (≥ 4½ digits, SCPI over USB), because the QA403 inputs are AC-coupled (100 % screening); the DAC-mismatch assumption stays open until measured. DAC centre voltage: the ES9018K2M datasheet gives two values, 1.702 V (current-output formula 2.112 mA − 1000·Vg/806 = 0) and 1.65 V (voltage-source model, AVCC/2), and the design uses 1.703 V. If the null is 1.65 V, the VREF-to-null term becomes 2.8 mV and the worst case ≤ 8.6 mV unbalanced and ≤ 17.2 mV balanced (limits ±10 / ±20 mV); R433 1 kΩ → 0 Ω then sets VREF = 1.650 V, decided after the VREF null test on the proof boards.

Noise (estimates): the I/V output is 6.95 nV/√Hz (OPA2210 2.2 nV/√Hz × 2.04 plus the Rf and DAC-source thermal noise), the leg network adds 9.85 nV/√Hz of its own, and an unbalanced leg is 13.9 nV/√Hz. Balanced, both legs share the same two I/V converters (leg+ = I/V(DAC−) − I/V(DAC+), leg− the swap), so the I/V noise doubles with the signal and only the leg-network noise adds as √2: 24.1 nV/√Hz against a signal ×2, a balanced advantage of +0.85 dB, not +3 dB. VREF noise (LP5907 < 6.5 µVrms × 0.516) is common mode; the residual through the 3 % pair-gain mismatch is ≈ 0.2 µVrms per leg, negligible. Dynamic range (A-weighted, with the DAC’s 127 dB(A), which is also common to both legs): ≈ 119.5 dB(A) unbalanced and ≈ 120.3 dB(A) balanced; the analog stages alone give ≈ 120.9 dB(A) unbalanced. With the OPA2197 the correlated figures would have been 117.0 / 117.4 dB(A), and worse in its transition region. Target ≥ 115 dB(A), minimum ≥ 112 dB(A), unchanged; measured results are recorded with the analyzer loopback floor. The I/V pole (288 kHz) and the leg pole (241 kHz) give −0.05 dB at 20 kHz and −0.20 dB at 40 kHz.

Bit-clock duty cycle (design calculation per rate). The ES9018K2M requires a duty cycle of 45:55 to 55:45, high and low times ≥ 4.5 ns and a cycle ≥ 10 ns, with data setup 4.1 ns and hold 2 ns to the rising edge (datasheet v3.7, Audio Interface Timing); the CPLD changes SDATA and LRCLK on the falling BCLK edge, ≥ 20 ns before the next rising edge at 24.576 MHz BCLK. With the selected family oscillator doubled by the CPLD PLL, every rate is an exact integer division, and the PLL ×2 also turns the oscillators’ 45–55 % duty into a 50:50 bit clock. Integer division sets the nominal duty, so the table gives the ideal duty; PLL jitter and output timing are verified on the bench:

Rate | Bit clock (64 × fs) from | Ideal duty | Against 45:55 to 55:45
48 kHz | X202 24.576 MHz × 2 (CPLD PLL) = 49.152 MHz ÷ 16 | 50 % | Inside (exact integer ratio)
96 kHz | 49.152 MHz ÷ 8 | 50 % | Inside (exact integer ratio)
192 kHz | 49.152 MHz ÷ 4 | 50 % | Inside (exact integer ratio)
384 kHz | 49.152 MHz ÷ 2 | 50 % | Inside (exact integer ratio)
44.1 kHz | X203 22.5792 MHz × 2 (CPLD PLL) = 45.1584 MHz ÷ 16 | 50 % | Inside (exact integer ratio)
88.2 kHz | 45.1584 MHz ÷ 8 | 50 % | Inside (exact integer ratio)
176.4 kHz | 45.1584 MHz ÷ 4 | 50 % | Inside (exact integer ratio)
352.8 kHz | 45.1584 MHz ÷ 2 | 50 % | Inside (exact integer ratio)

Thermal: the analog input power is bounded by the TPS2553 limit (≤ 1.06 W Default, ≤ 2.49 W High); the board worst case is ≈ 3.8 W (3.77 W, High mode, overload). A 4.4-to-3.5 mm adapter shorts leg−, one amplifier per package: ≈ 0.35 W in the shorted amplifier + ≈ 0.1 W in the other, ≈ 0.45 W per package, +21 °C (θJA 47.6 °C/W). A 4.4 mm plug shorting leg+ to leg− loads both amplifiers of one package with ≈ 0.55 W per package, outside TI’s one-amplifier continuous-short rating, so it gets a bench survival test. Regulator and power-part dissipation (estimates; 3V3D maximum load: CPLD 25, X201 40, X202 5, X203 10, DVCC 14.2, DVDD 60 through U303, enables and nodes 1.7, I²C 1.5 mA; layout rule: copper pours on the LDO VIN, GND and VOUT pins; IR or thermocouple check at bring-up):

Part | Load | Dissipation | Note
U504 3V3D ME6211, without dropper | 157 mA max | 0.27 W at 5.0 V, 0.31 W at 5.25 V | ME6211 SOT-23 power dissipation rating 300 mW (datasheet absolute maximum) → too close
U504 with R519 + R520 (2 × 2.2 Ω 0805 in series, 4.4 Ω) | 157 mA max (103 mA typ) | 0.13 W typ, 0.16 W at 5.0 V, 0.20 W at 5.25 V; 54 mW per resistor (0.125 W rating) | LDO input ≥ 3.71 V at VBUS 4.40 V (≈ 0.25 V dropout needed at 157 mA, estimate)
U502 3V3M ME6211 | 84 mA | 0.16 W at 5.25 V | —
U303 1.3 V ME6216 | 60 mA | 0.12 W | Pd rating to confirm
U302 LP5907 | 17.5 mA | 0.03 W | —
U501 LM27762 | Worst clean load (4.4 mm 32 Ω, High) | ≈ 0.22 W | Check against its datasheet θJA at layout
U503 TPS2553 | 0.26 A | 9 mW normal; ≤ 2.6 W into a short for ≤ 10 ms before the latch/FAULT path | Its thermal shutdown protects

Protection is required, because the target headphones are expensive and hard to replace. There are no relays; the outputs are kept safe by the power sequence, the hardware fault latch with its fast capture, the slow firmware DC tier and the Q609 interlock:

Function | Implementation | Requirement
DC detect (hardware) | Each leg → R601–R604 100 kΩ + C601–C604 1 µF (τ = 100 ms; 84–111 ms with 1 % R and C −15 %/+10 % incl. DC bias) → BAV99 into MAX and MIN nodes (1 MΩ loads); LM393 thresholds from the rails (100 kΩ / 10 kΩ, R609/R610): node 0.323–0.360 V (nominal 0.341 V) → leg trip 0.47–0.81 V (nominal 0.635 V), including the LM393 offset (±9 mV) and the BAV99 VF at ≈ 0.4 µA (0.12–0.40 V, estimate, measured on the proof boards) | Worst case: 1.0 V → 183 ms (≤ 250 ms), 2.0 V → 59 ms (≤ 100 ms), including node F (≤ 1.33 ms) and the latch capture (35 µs); no false trip for full-scale content above 9.9 Hz worst case (6.0 Hz nominal)
Slow DC tier (firmware) | Per leg, from the jack side of R417–R420: R624–R627 1 MΩ (series), R628–R631 1 MΩ (to 3V3M), R632–R635 1 MΩ (to GND), C608–C611 100 nF → MCU ADC node = 1.1 V + leg/3 (−0.18 … +2.40 V over the full rail range), τ ≈ 33 ms, leg load ≈ 1 µA; ratiometric to 3V3M; each channel’s zero calibrated at the end-of-line test (uncalibrated error up to ≈ ±35 mV at the leg). The firmware sets the latch by switching ANA_FAULT to open-drain low → D606 → node F (no extra part) | ≥ 0.8 V (0.5-s average) → latch within 1 s; ≥ 0.2 V (2-s average) → within 3 s; no false trip for full-scale content above ≈ 2 Hz; active only while AMP_EN is high; below 0.2 V (≤ 2.5 mW into 16 Ω, ≤ 1.25 mW into 32 Ω): owner decision pending
Hardware kill paths | When the latch is set, Q607 pulls RAIL_EN (LM27762 EN+ and EN−), Q608 pulls AMP_EN (both OPA1622 EN) and Q611 pulls AVCC_EN (LP5907) low; each enable has a 100 kΩ pull-down and is driven by the MCU through 10 kΩ. Q609 (gate from RAILS_OK_N through R623 100 kΩ, C607 100 nF to GND) is a slow static interlock: on 6–32 ms after PGOOD goes bad, off 2.5–13 ms after it goes good, so it keeps AMP_EN low whenever the rails are off, also after a firmware clear | No firmware needed; ≈ 35 µs from PGOOD bad to RAIL_EN, AMP_EN and AVCC_EN low; a short PGOOD glitch either latches or does nothing (never an un-latched AMP_EN dropout); EN stays below the OPA1622 input limit whenever the rails are off

Fault latch

N-MOSFETs only (11 × 2N7002, Q601–Q611): LM393 outputs → 10 kΩ → node F (47 kΩ to 3V3M, C605 100 nF to GND, 1N4148WS clamp D605: ≈ −0.7 V on a fault, ≤ 0.31 mA) → Q601 inverter → set request S → Q602 sets the Q604/Q605 cross-coupled latch (R614/R615 47 kΩ pull-ups, no latch capacitor; FLT high = fault). Q610 (gate RAILS_OK_N) pulls node F low when PGOOD is bad; D606 (node F to ANA_FAULT) lets a sustained TPS2553 overcurrent or the firmware set it; Q606 (MCU FLT_CLR) clears it; C605 starts node F at 0 V, so the latch sets at attach independent of the unpowered LM27762 PGOOD pin; the MCU reads FLT, ANA_FAULT and RAILS_OK_N

Capture ≈ 35 µs (RAILS_OK_N ≈ 8.5 µs, node S ≈ 9.9 µs, node B ≈ 14.0 µs, plus FET transitions; budget 0.1 ms, measured); node F stays low 1.5–7.4 ms after any PGOOD or fault pulse, so every pulse that turns Q610 on (≥ ≈ 10 µs) is latched; with ANA_FAULT low, F sits at 0.5–0.7 V against the Q601 VGS(th) minimum of 1.0 V (0.3–0.5 V margin, smaller at low temperature); a clear does not stick while a set request is present
Blanking | Q603 holds S low after PGOOD goes good (R617 1 MΩ + C606 100 nF from PGOOD; 2N7002 VGS(th) 1.0–2.5 V, R 1 %, C 10 %): the set path is armed 25–133 ms after PGOOD goes good and re-blanked 35–173 ms after PGOOD goes bad (charging through R505 + R617) | Blocks only the set request and never clears a set latch (no hiccup); an overload that drops PGOOD sets the latch at once, while the PGOOD-bad request at start-up is blanked; AMP_EN only after PGOOD has been good ≥ 150 ms
Energy at the terminals | E = V²/R × (detector + node F + latch time) + the energy after the trip (tables below): a rail-stuck failure in High mode (3.89 V maximum rail) 26.2 mJ at 16 Ω and 13.3 mJ at 32 Ω worst case; digital DC with a healthy output stage ≤ 13.7 mJ at 16 Ω. After the trip both rails’ capacitors (C +10 %, maximum rails) hold 0.51 mJ and DAC back-power into a failed stage adds ≤ 1 µJ → ≤ 0.6 mJ; the LM27762 50 kΩ discharge is not relied on | ≤ 30 mJ at 16 Ω and ≤ 15 mJ at 32 Ω, worst case, including the after-trip energy; OPA1622 shutdown is not treated as isolation (TI: the output is not high-impedance)
Power sequence and DAC pins | VREF tracks AVCC (C421 330 pF, τ ≈ 2.8 µs), and the I/V converters hold the DAC pins at VREF. Power-up enables the legs before AVCC; controlled power-down turns RESETB, AVCC_EN and AUD_EN off first with the I/V converters and legs powered, the rails last. After a latch trip 3V3A collapses within ≈ 3.2 ms, about when the I/V rails (≈ 13 mA load with the amplifiers off) reach the OPA2210 minimum supply (≈ 3.6 ms); any residual back-power is ≤ 1.7 mA per DAC pin (806 Ω − 11 %), inside the OPA2210’s 10 mA input-current rating | ES9018K2M absolute maximum GND < Vout < AVCC on DACL, DACR, DACLB and DACRB: inside in every controlled transition and in the latch shutdown; at most ≈ 0.15 V above AVCC for microseconds at a sudden unplug; bench check TP709 VREF vs TP710 AVCC_L

Overload, cause and recovery

Analog current reaches the TPS2553 limit → rails droop → PGOOD bad (Q610) or, after the FAULT deglitch, D606 → latch set → rails, amplifiers and AVCC off. At the FLT interrupt, before any other action, the firmware stores the four leg DC readings (the 33 ms RC holds the pre-trip state), ANA_FAULT, RAILS_OK_N and whether it set the latch itself: DC fault if any leg reads ≥ 0.3 V or the firmware tripped, otherwise overload; unavailable readings count as a DC fault. FLT during a controlled power-down or before the first FLT_CLR after power-up is expected: not logged, not counted, no ceiling change

Overload: soft mute, volume ceiling −3 dB per event (down to −12 dB), clear after ≥ 1 s (FLT_CLR only after the rails have been off ≥ 200 ms), ceiling kept until replug; overloads count toward the 3-strike stop only once the ceiling has reached −12 dB. DC fault: clear after 2 s; 3 DC faults within 10 s → latched until USB replug; red LED blinks. Overload tests in Section 7
Unplug and brownout | The VBUS analog watchdog (4.10 V nominal, 3.95–4.25 V) drops AMP_EN and RAIL_EN (target < 5 µs; ≈ 1 µs margin at 0.47 A, where VBUS falls at up to ≈ 0.1 V/µs); PGOOD goes bad at VBUS ≈ 3.70 V and sets the latch as the hardware backstop | Pop ≤ 20 mV peak (target, measured); DAC-pin safety relies on VREF tracking, not on this timing; watchdog-to-GPIO latency measured on Stage 2
Adapter short | A 4.4-to-3.5 mm adapter shorts leg−; with U401 = L+/L− and U402 = R+/R−, only one amplifier per package is shorted (TI continuous-short rating) | ≈ 0.45 W per package; warning in the manual
Jack ESD and bring-up safety | 4 × LESD5D5.0CT1G (5 V standoff, 12 pF), one per jack leg; bring-up with dummy resistors only | Never test on real headphones

Protection envelope, worst case, for the hardware detector (removed = RAIL_EN, AMP_EN and AVCC_EN pulled low): a DC fault ≥ 2 V on any leg is removed within 100 ms and ≥ 1 V within 250 ms. The worst case combines the rails (3.673–3.890 V / 3.618–3.828 V), 1 % divider resistors, the LM393 input offset (±9 mV over temperature), the BAV99 forward voltage at ≈ 0.4 µA (0.12–0.40 V over 0–50 °C and unit spread; estimate from VF(1 mA) ≤ 0.715 V with n ≈ 2, measured on the proof boards), the diode load current through the filter resistor, C601–C604 −15 %/+10 % (tolerance and DC bias), the node F delay through R611 into C605 (≤ 1.33 ms) and the latch capture (35 µs): node threshold 0.323–0.360 V (nominal 0.341 V), leg trip 0.47–0.81 V (nominal 0.635 V), τ 84–111 ms. No false trip for full-scale content above 9.9 Hz worst case (6.0 Hz nominal; v0.6 quoted ≈ 4–5 Hz nominal):

DC on a leg | Removal time, nominal | Removal time, worst case | Requirement
1.0 V | 101 ms | 183 ms | ≤ 250 ms (27 % margin)
1.5 V | 56 ms | 87 ms | —
2.0 V | 39 ms | 59 ms | ≤ 100 ms (41 % margin)
2.47 V (full-scale digital DC) | 30 ms | 45 ms | —
3.67–3.89 V (rail-stuck) | 19–20 ms | 27–29 ms | —

Terminal energy E = V²/R × (detector + node F + latch time) + the energy after the trip, recalculated for v0.7 with the worst-case detector (the rail-stuck column includes the after-trip energy; nominal values in brackets):

Load | Rail-stuck failure, High mode, worst case incl. after-trip (nominal) | Digital DC on a healthy output stage, worst case (V at the leg, removal time, energy)
16 Ω | 26.2 mJ (17.9 mJ) | 1.81 V (swing-limited), 66.7 ms, 13.7 mJ
32 Ω | 13.3 mJ (9.2 mJ) | 2.17 V, 52.8 ms, 7.8 mJ
60 Ω | 7.4 mJ (5.1 mJ) | 2.40 V, 46.8 ms, 4.5 mJ
300 Ω | 1.9 mJ (1.4 mJ) | 2.47 V (full scale), 45.1 ms, 0.9 mJ

After the trip both rails’ capacitors, with C +10 % at the maximum rail voltage, hold 0.51 mJ, and DAC back-power into a failed stage adds ≤ 1 µJ, so the after-trip bound is ≤ 0.6 mJ (the LM27762 50 kΩ discharge is not relied on). Requirement (hard, worst case): ≤ 30 mJ at 16 Ω and ≤ 15 mJ at 32 Ω for a rail-stuck failure in High mode, including the after-trip energy; the worst-case estimates are 26.2 / 13.3 mJ. The 30.0 / 15.0 mJ figures quoted in v0.6 were nominal values. In Default mode a rail-stuck fault into 16–32 Ω exceeds the TPS2553 limit, so the PGOOD/overcurrent path latches first; the table is the High-mode worst case. Risk kept: a rail-stuck failure in High mode can put up to ≈ 26 mJ into a 16 Ω IEM; v2 option: a fast “leg within 0.5 V of a rail” detector (≈ 1 ms).

Slow DC tier and fault cause (firmware): the tier covers the region below the hardware trip. At ≥ 0.8 V (0.5-s average) it sets the latch within 1 s and at ≥ 0.2 V (2-s average) within 3 s, through ANA_FAULT and D606 into node F, the same hardware kill path. The remaining blind region below 0.2 V per leg (≤ 2.5 mW into 16 Ω, ≤ 1.25 mW into 32 Ω) is proposed for acceptance and recorded as a pending owner decision (Section 9.2). The recovery rule counts DC faults (3 within 10 s latch the board off until USB replug) and counts overloads only once the volume ceiling has reached −12 dB, because Default mode at full volume into 60 Ω balanced needs three −3 dB steps and the v0.6 rule could lock the board off within ≈ 5 s.

Power-up sequence after USB configuration (controlled power-down and fault shutdown in Section 3.2). VREF tracks AVCC, so the DAC pins stay inside GND…AVCC in every step. Enabling the legs while VREF = 0, and disabling them after VREF has collapsed, keeps the disabled-state path through the difference-amplifier network (VREF through ≈ 4 kΩ into the load: up to ≈ 13 mV at 32 Ω and ≈ 120 mV at 300 Ω if the disabled OPA1622 output were high-impedance) out of every enable and disable:

Step | Action | Note
1 | ANA_EN high → TPS2553 soft start → 5V_ANA | Headphone supply first
2 | ≥ 200 ms after attach with the rails off: FLT_CLR, confirm FLT low; RAIL_EN high → +3.78 V / −3.72 V → PGOOD good | Latch set path armed 25–133 ms later; the power-on latch set is cleared here
3 | PGOOD good ≥ 150 ms (set path armed): AMP_EN high while AVCC is still off (VREF = 0 V, I/V outputs at 0 V) | The legs start at ≈ 0 V
4 | AVCC_EN high → VCCA, AVCC_L/R and VREF rise together (τ ≈ 2.8 µs) | Common mode: the active legs hold the jack at ≈ 0 V ± 3.4 mV common-mode leakage; ESS: VCCA first, AVCC with it
5 | +5 ms: AUD_EN high → 3V3D (DVCC, CPLD, X201; X202/X203 per enable); the 1.3 V DVDD LDO is fed from 3V3D | ESS: DVCC later, DVDD with or after DVCC (DVDD ≤ DVCC during the ramp)
6 | RESETB released ≥ 1 ms after all supplies and MCLK are stable → I²C init (asynchronous mode, 32-bit I²S, mute, master trim) → firmware DC tier armed → soft unmute when streaming; the CPLD starts with both family enables low and the PLL in reset, then enables X202 after ≥ 1 ms | MCU outputs toward the CPLD stay low or high-impedance while 3V3D is off; I²C pull-ups on 3V3D. Rate change: MCLK never changes; a family change runs the break-before-make sequence (Section 3.1) with the PLL held in reset; AMP_EN stays high

# 6. Cost budget

Budget for the 5-board sample run on JLCPCB Economic PCBA, at the fixed rate of 31.7 NTD per US$ that the cost gate uses. Pricing rule: the LCSC tier that matches the run quantity (1+ tier for one-per-board ICs, 10+ for two-per-board parts), with a US$0.10 minimum per purchasing line for parts under US$0.05 (attrition and minimum-quantity allowance); the OPA2210 is priced from its JLCPCB part page, because the PCBA order is charged at JLCPCB prices. Parts List v0.5 is the source of truth for cost.

Item | Basis | US$, 5 boards | NTD per board
USB-C input and sensing | LCSC prices | 1.53 | 10
USB bridge: CH32V307 + CPLD + crystal + three oscillators | LCSC prices | 36.88 | 234
DAC (ES9018K2M) and its supplies | LCSC prices | 19.08 | 121
I/V converters and output legs: 2 × OPA2210 + 2 × OPA1622 + 0.1 % resistors | LCSC prices; OPA2210 at the JLCPCB price | 31.77 | 201
Power: domains, current limit and +3.78 V / −3.72 V rails | LCSC prices | 10.17 | 64
Protection and control | LCSC prices | 2.47 | 16
Outputs, indicators, test, board (the 4.4 mm jack is 218 NTD of this) | LCSC prices | 36.33 | 230
Minimum-spend allowance (US$0.10 per purchasing line under US$0.05) | Pricing rule | 0.74 | 5
Subtotal, parts (4,405 NTD) | Parts List v0.5 | 138.97 | 881
5 bare 4-layer PCBs | Estimate | 10.00 | 63
Economic PCBA setup | JLCPCB price list | 8.18 | 52
Stencil | JLCPCB price list | 1.53 | 10
Extended part types (19 × US$3.07) | Includes the through-hole 4.4 mm jack (conservative) and X202 (class assumed) | 58.33 | 370
SMT joints (723 per board × US$0.0016 × 5) | JLCPCB price list | 5.78 | 37
X-ray (8 leadless parts per board × 5 × US$0.82) | CPLD, DAC, 2 × OPA1622, LM27762, three oscillators (oscillators conservative) | 32.80 | 208
Through-hole joints (4.4 mm jack, 7 joints × 5 × US$0.0164 + US$3.58) | JLCPCB price list | 4.15 | 26
Confirm Parts Placement | JLCPCB price list | 0.45 | 3
Subtotal, JLCPCB fees | JLCPCB price list; any fixture or other assembly line in the real quote counts toward the gate | 111.23 | 705
Total, 5-board run (8,248 NTD) | Parts + PCBs + fees | 260.20 | 1,650
Cost-gate status: target 1,500 NTD per board; ceiling 1,700 NTD per board | WARN above 1,500, FAIL above 1,700; 150 NTD over the target, 50 NTD under the ceiling | — | WARNING

Lines are rounded to whole NTD, so a subtotal can differ by 1 NTD from the sum of its lines.

Outside the ceiling: shipping, import tax, the WCH-LinkE and CPLD programming cable, the enclosure and the proof-of-concept hardware for the firmware gate (Section 8). Inside the ceiling: every JLCPCB line of the real quote, including any fixture or other assembly line. The fixture sentence on the X202 and OPA2210 part pages is standard text on every JLCPCB part page, so no fixture fee is expected for Economic PCBA. At quote approval both the gated subtotal and the total payable (gated subtotal + shipping + tax from the quote) are recorded.

Counts: 136 BOM lines (127 fitted; DNF: U205, R215, R216/R217, R703, J703), 47 purchasing lines, 247 placed parts per board, 19 Extended + 28 Basic part types, 723 SMT joints + 7 through-hole joints per board, 8 leadless parts per board (X-ray).

Extended types (19): CH32V307RCT6, AGRV2KQ32, ES9018K2M, OPA1622IDRCR, OPA2210IDR, LM27762DSSR, TPS2553DBVR, LP5907MFX-3.3, ME6211C33M5G-N (two fitted, one type), ME6216A13M3G, USBLC6-2SC6, the three oscillators X201 (SCTF SX3M80.000B20F30TNN, C5179978), X202 (YXC OT322524.576MJBA4SL, C2831388) and X203 (SCTF SX2M22.5792M20F30TNN, C5452663), RT0603BRD072KL (2.00 kΩ 0.1 %), the USB-C receptacle, the 3.5 mm jack, the 4.4 mm jack and LESD5D5.0CT1G; the DNF mux U205 is not counted. Every line’s class is taken from its JLCPCB part page or the basic-parts list, except X202, whose class is not shown (assumed Extended); everything else is Basic.

Cost gate: target 1,500 NTD per board (WARN above) → WARN, 150 NTD over; ceiling 1,700 NTD per board (FAIL above) → WARNING, 50 NTD under the ceiling. Ceiling 1,700 NTD per board, set when the third oscillator was added; on 24 Sep 2026 the owner confirmed the budget is flexible as long as it does not surge; the gate covers every JLCPCB line of the real quote, and the actual JLCPCB quote from the real BOM/CPL files must pass the ceiling before ordering. Conservative items: the through-hole Extended fee (−19.5 NTD per board) and the X-ray of the three oscillators (−26.0 NTD per board each) give ≈ 1,552 NTD per board if JLCPCB charges none of them. Price risk: the OPA2210 has no qualified second source (OPA2209AIDR, C2057330: JLCPCB stock 0, US$6.11 at 1+; OPA1612: common-mode limit (V+) − 2 V = 1.67 V at the minimum rail, below VREF 1.703 V). If it has to be bought at the LCSC price (JLCPCB stock gone), the cost rises by 106 NTD per board to ≈ 1,755 NTD, above the ceiling (owner decision), so 12 pieces (10 + 2 spares; the spares ≈ US$2, outside the estimate) are reserved in the JLCPCB parts library now, together with the other low-stock parts. No cheaper 4.4 mm jack exists at LCSC (no SMD option).

Stock to reserve in the JLCPCB parts library before ordering (LCSC, Jun–Sep 2026): CH32V307RCT6 119, ME6216A13M3G ≈ 410, 4.4 mm jack 721, ES9018K2M 724, AGRV2KQ32 980 and OPA2210IDR (JLCPCB available 76: reserve 12, 10 + 2 spares); X201 has 2,503 in stock at LCSC.

Why the estimate changed: 1,540 NTD per board with one oscillator → 1,602 NTD with the 24.576 MHz oscillator (+62 NTD: the part with its decoupling capacitor 16.2, its Extended-part fee 19.5, its X-ray 26.0 and eight more SMT joints 0.4) → 1,666 NTD with the 22.5792 MHz oscillator (+64 NTD: the part with its capacitor and three resistors 17.5, its Extended-part fee 19.5, its X-ray 26.0 and twelve more SMT joints 0.6) → 1,647 NTD per board in v0.6 (80 MHz MCLK, OPA2210 at the JLCPCB price, protection parts) → 1,650 NTD per board in v0.7 (+3 NTD: protection and power fixes, 723 SMT joints).

Reference only, not the budget basis: a 100-unit build on Standard PCBA comes to ≈ 800 NTD per board. The budget and the cost gate use the 5-board sample run above.

# 7. Design for JLCPCB (DFF/DFA/DFT rules) and tests

These rules apply to every revision and use JLCPCB’s PCBA price list; the 5-board sample run is built on Economic PCBA. The rules that can be checked automatically also run in CI (Section 8).

ID | Type | Rule
R01 | DFA | The sample run uses Economic PCBA: setup US$8.18, stencil US$1.53, 2–50 boards per order, one side only (all SMT parts on the top side).
R02 | DFA | Every fitted part has an LCSC number and a JLCPCB class taken from its JLCPCB part page or the basic-parts list, except X202, whose class is not shown (assumed Extended) (Parts List v0.5). Prefer Basic parts (no per-type fee): where the exact value is Extended, Basic E24 values or Basic combinations are used (100 k + 47 k, 1 k ∥ 5.1 k, 15 k + 1 k, 100 k + 100 k + 5.1 k, 2 × 330 pF, 2 × 2.2 Ω). Each Extended type costs US$3.07; this board has 19 Extended + 28 Basic types (the through-hole jack counted as Extended, conservatively, and X202 assumed Extended).
R03 | DFA | X-ray costs US$0.82 per leadless part, so prefer leaded packages where an equivalent exists. Leadless here (8 per board): AGRV2KQ32, ES9018K2M, 2 × OPA1622, LM27762 and the three oscillators (counted conservatively). The CH32V307RCT6 (LQFP-64), 2 × OPA2210 (SOIC-8), TPS2553 (SOT-23-6) and the DNF mux U205 (SOT-363) are leaded.
R04 | DFA | Joint fees: SMT US$0.0016 per joint (723 per board); through-hole US$0.0164 per joint + US$3.58 per order. Only the 4.4 mm jack is through-hole (7 joints); confirm that the USB-C receptacle’s shell pegs do not add a through-hole line.
R05 | DFA | Turn on “Confirm Parts Placement” (US$0.45) and check the 3D preview for rotation and polarity errors. The fixture sentence on the X202 and OPA2210 JLCPCB pages is standard text on every part page; any fixture or other assembly line in the real quote counts toward the 1,700 NTD gate.
R06 | DFA | Reserve low-stock parts in the JLCPCB parts library before ordering: CH32V307RCT6, ME6216A13M3G, 4.4 mm jack, ES9018K2M, AGRV2KQ32 and 12 × OPA2210IDR (10 + 2 spares; JLCPCB available 76).
R07 | DFT | Test pad on every rail and switched domain and on the clock, I²S, enable, protection and CC nodes; 31 pads, TP701–TP731: TP701 5V_SYS, TP702 5V_ANA, TP703 3V3M, TP704 3V3D, TP705 3V3A, TP706 1V3, TP707 +3.78 V, TP708 −3.72 V, TP709 VREF, TP710 AVCC_L, TP711 MCLK, TP712 family-clock node, TP713 OSC48_EN, TP714 OSC44_EN, TP715 BCLK, TP716 LRCLK, TP717 SDATA, TP718 AMP_EN, TP719 RAIL_EN, TP720 AVCC_EN, TP721 RAILS_OK_N, TP722 FLT, TP723 ANA_FAULT, TP724 node F, TP725 VBUS_SENSE, TP726 CC1, TP727 CC2, TP728–TP731 GND.
R08 | DFT | Debug pads for the MCU (WCH-LinkE 2-wire: 3V3, SWDIO, SWCLK, GND) and the CPLD (JTAG: 3V3, TCK, TMS, TDI, TDO, GND); DNF 1 × 6 I²S test header J703 (MCLK, BCLK, LRCLK, SDATA, GND, 3V3 ref) with a firmware test mode that tristates the CPLD I²S outputs. The J703 MCLK pin is a monitor output only, through R703 1 kΩ (DNF, fitted with J703): in test mode an external 3.3 V source (QA403, via series resistors) drives only BCLK, LRCLK and SDATA, and the DAC stays in asynchronous mode on X201.
R09 | DFT | Fiducials and polarity marks.
R10 | DFF | JLCPCB’s standard 4-layer impedance-controlled stack-up for the 90 Ω USB pair; solid ground plane; digital, charge-pump (2 MHz) and analog areas separated; the unbalanced jack sleeve gets a dedicated return with ≥ 4 vias (≤ 5.7 mΩ shared ground for −75 dB crosstalk at 32 Ω); both family oscillators and their shared node sit next to the CPLD PLL clock pin with short traces, and the idle oscillator’s trace is kept short (a disabled output-enable oscillator may keep running internally); copper pours on the LDO VIN, GND and VOUT pins (dissipation table, Section 5.3).

Tests added or changed in v0.5, its amendment, v0.6 and v0.7 (automated where marked):

Test | When | Pass criterion
End-of-line calibration (automated, QA403 + scripts) | Every board | Full-scale level per leg → master trim to 1.75 Vrms ± 0.1 dB and per-channel fine trim, written to MCU flash
Offset screening (automated, DC-capable DMM) | Every board | DC offset of every leg with a DC-capable DMM (≥ 4½ digits, SCPI over USB), because the QA403 inputs are AC-coupled: ≤ ±10 mV unbalanced, ≤ ±20 mV balanced; the QA403 stays for level, THD+N and dynamic range
THD+N and dynamic range (automated) | Every board | Section 2 targets at the calibrated level; dynamic-range results recorded with the analyzer loopback floor

Protection: removal and energy

Each board revision

(a) Detector test: an external lab source on a jack contact (its link R417–R420 removed) at 1.0 V, 2.0 V and 3.8 V; tests detection and the control signals only. (b) Failed-output emulation: the board’s own +3.78 V (TP707) or −3.72 V (TP708) switched onto a jack contact (link removed) by an external MOSFET switch, bypassing the amplifier enable, into 16 Ω and 32 Ω dummy loads; the terminal voltage is scoped and V²/R integrated until it stays below 0.1 V. Pass: FLT high, RAIL_EN, AMP_EN and AVCC_EN low within the worst-case envelope (no allowance beyond the hard 100 ms / 250 ms / energy limits), total energy ≤ 30 mJ (16 Ω) / ≤ 15 mJ (32 Ω). (c) Digital DC test signal (healthy output stage). (d) SPICE of a failed output stage
Overload and plug short (30 min each, High mode, maximum volume) | Each board revision | 4.4 mm 16 Ω, 4.4-to-3.5 mm adapter, 3.5 mm 16 Ω, 60 Ω balanced full scale: the latch sets, recovery needs the firmware clear, all parts stay within ratings and the board recovers; near the Default-mode limit, rails and output scoped for clipping before a trip; 4.4 mm plug shorting leg+ to leg−: survival test
Latch timing and firmware DC tier | Each board revision (BAV99 on the proof boards) | Short PGOOD pulses: RAILS_OK_N forced high for 5 µs, 20 µs, 100 µs and 1 ms while the MCU keeps requesting AMP_EN → either nothing happens or the latch sets, never an un-latched AMP_EN dropout. Firmware DC tier: 0.25 V and 0.9 V DC from the digital path → latch within 3 s / 1 s. BAV99 forward voltage at ≈ 0.4 µA and 0/25/50 °C (detector worst case)
USB | Stage 2 board before layout (gate) and each board revision | Current in every state (USB power meter): attached-not-configured ≤ 100 mA, configured digital ≤ 256 mA; suspend current vs time from the last bus activity, ≤ 2.5 mA by 10 ms, on Stage 2 and on the main board; attach inrush charge ≤ 50 µC; VBUS droop at each domain enable; Default and High mode on a Type-C 1.5 A source and on a USB-A port; CC change handled within tSinkAdj; watchdog-to-GPIO latency < 5 µs (Stage 2)
Pop | Each board revision | Pop (peak of the transient beyond the settled DC step, 20 Hz–20 kHz, AC-coupled): ≤ 5 mV peak for controlled transitions (power-on after configuration, suspend/resume, rate and rate-family change, fault recovery); ≤ 20 mV peak at unplug or brownout (target); 32 Ω and 300 Ω
Jitter | Each board revision | J-test at the 48 kHz and 44.1 kHz families (both exact integer ratios, from X202 and X203 through the CPLD PLL) and at 384 kHz; spectra recorded (no numeric limit yet)
Clock checks (Stage 2 boards, firmware gate) | Proof of concept, before layout | Family change: scope both enables and the shared node: never both enabled, node quiet for ≥ 1 ms before the new oscillator starts, disable time measured, no runt pulses, PLL relock; all eight rates bit-perfect; on the shared-node board and on the mux board; the CPLD meets timing at 80 MHz (system clock) and 49.152 MHz (PLL output)
Rails, power and unplug | Bring-up | Negative-rail margin at VBUS 4.60 V and full load (predicted ≥ 0.11 V worst case); supply order and DVDD ≤ DVCC on the scope; DAC pin vs AVCC (TP709 VREF vs TP710 AVCC_L) at power-up, power-down, latch trip and unplug; regulator temperatures (IR or thermocouple); power tables in both modes (High and Default)

# 8. Automation and verification plan

Every check runs automatically with an explicit pass/fail rule.

Check | Runs when | Pass/fail rule
ERC and DRC (KiCad command line) | Every commit (GitLab CI) | Zero errors
Manufacturing outputs: Gerbers, drill, BOM, pick-and-place, schematic PDF | Every commit | Files generated
BOM check | Every commit | Every fitted part has an LCSC number and a JLCPCB class from its part page or the basic-parts list (X202 assumed Extended; Parts List v0.5) and stock ≥ the 5-board quantity; Extended types and leadless parts counted and reported
Cost gate | Every commit | 5-board run at a fixed 31.7 NTD/US$, covering every JLCPCB line (PCBs, PCBA fees including any fixture or other assembly line, parts): WARN if > 1,500 NTD per board (target), FAIL if > 1,700 NTD per board (ceiling); currently 1,650 NTD: WARN (planning estimate; the JLCPCB quote from the real BOM/CPL files must pass the ceiling before ordering, and the gated subtotal and total payable are recorded at quote approval). A 100-unit reference line (≈ 800 NTD) is reported but not gated
Python DFF/DFA/DFT and layout rules | Every commit | All rules pass: analog/charge-pump separation, 90 Ω USB pair, decoupling capacitor near every IC power pin, test point on every rail and domain, fiducials present, jack-ground rule, short family-oscillator traces at the PLL pin
Document lint | Every documentation merge request | Generated DOCX/XLSX files contain no unresolved template tokens (for example ZQ-…-QZ), no empty cells in required tables and no internal file paths
AI datasheet-review agent | Every merge request | Reads the DAC, amplifier and regulator datasheets, extracts requirements, checks the schematic and comments on the MR; seeded by the Schematic Design Notes checklist and scored on 10–20 planted errors (catch rate and false alarms)
Firmware unit tests (PC build) | Every commit (GitLab CI) | The pure-logic firmware parts (descriptor tables, feedback math, ring buffer, volume mapping) compile on a PC and every unit test passes

Firmware gate

Before layout: two-stage proof of concept (below)

Enumerates bus-powered with the new descriptors; every rate plays on Windows 10/11, macOS and Linux with working feedback; BCLK/LRCLK average rates correct for every rate (frequency counter) and the DPLL locks; host volume and mute work; all eight rates bit-perfect; the break-before-make family change passes on the shared-node and the mux board (never both enabled, ≥ 1 ms quiet node, no runt pulses, PLL relock); the CPLD meets timing at 80 MHz and 49.152 MHz; the Stage 2 USB currents pass (unconfigured ≤ 100 mA, configured digital ≤ 256 mA, suspend ≤ 2.5 mA within 10 ms of the last bus activity, measured as current vs time) and the watchdog-to-GPIO latency is < 5 µs (layout gate)
Automated measurement, calibration and screening (Python + QuantAsylum QA403 + DC-capable DMM) | Every board | Calibration to 1.75 Vrms per leg, offset screening with the DMM, THD+N, dynamic range (with the analyzer loopback floor), frequency response, crosstalk, output impedance and maximum power at 16–600 Ω on both jacks in both modes; auto-generated report compared against Section 2
Automated THD-compensation tuning loop | Each board revision | Python sweeps the ES9018K2M THD-compensation registers 22–25 (2nd/3rd harmonic) while reading THD+N on the QA403; reports the best coefficients for the optional firmware setting

Firmware (owner decision, 24 Sep 2026): our own USB Audio Class 2.0 implementation on the CH32V307 high-speed USB port, built on WCH’s register-level USBHS device examples; the chip’s EVT package has high-speed device examples for HID, CDC serial, mass storage and network adapters, but none for audio. TinyUSB (MIT) is an alternative only if its CH32V307 high-speed audio path proves reliable: a 2023 report showed UAC2 control requests failing on this chip, and its driver contributor had not verified isochronous transfers. The USBAudioToI2S firmware (Apache-2.0) stays a known-good comparison on the same hardware and a reference; license notices are kept if any code is copied. The CPLD logic is ours too.

The firmware gate runs as a two-stage proof of concept before layout. Stage 1 is a desk setup of a WCH CH32V307V-EVT-R1 board, an AGM 2K-LUT CPLD board and an ES9018K2M I²S-input DAC board (≈ US$48–57 for the three at listing prices, outside the board budget), brought up in order: enumeration and controls without audio, then streaming into a dummy sink with timer feedback, then the full chain with the CPLD and the DAC; it also confirms the CH32V307 SPI maximum clock for the link. Stage 2 is mandatory: a proof-of-concept board with USB-C and ESD, the 3V3M/3V3D LDOs with the 3V3D dropper, the CH32V307 with its crystal, the AGRV2KQ32, X201 80 MHz, X202 and X203 with R210–R217, the real pin map, an I²S/MCLK header to the Stage 1 ES9018K2M board and current-measurement points on 3V3M and 3V3D. It adds the real enable-controlled regulators with resistive dummy loads (TPS2553 with 53 mA on 5V_ANA, LP5907 with 17.5 mA on 3V3A, ME6216 with 60 mA on 1V3), so the suspend transition, the watchdog latency and the domain enables are measured on the real path. Two boards are built, one with the shared node and one with the mux fitted: ≈ US$90 ≈ 2,860 NTD for the two assembled boards (was ≈ US$79 ≈ 2,500 NTD), outside the board budget.

USB compliance is part of the pre-layout gate. With the real CPLD design loaded, streaming 384 kHz at VBUS 4.60 V and 5.25 V and across rate and family changes, the Stage 2 board must show an attached-not-configured current ≤ 100 mA, a configured digital current ≤ 256 mA (the datasheet DAC currents added, since the DAC is on the Stage 1 board), a suspend current ≤ 2.5 mA within 10 ms of the last bus activity (current vs time) and a watchdog-to-GPIO latency < 5 µs; the clock handover checks and all 8 rates bit-perfect complete the gate. Layout does not start unless all pass; the main boards repeat the full-board measurement at bring-up. The MCU–CPLD interface (SPI with chip-select framing) is ours to define; its specification and the pin map are frozen before the Stage 2 board and the schematic. Modules, all part of the gate:

ID | Module
(1) | USB core on the high-speed port: enumeration, descriptors, standard requests, suspend/resume. Bus-powered descriptors (bmAttributes 0x80, bMaxPower 0xFA = 500 mA); test VID/PID 1209:0001 during development (pid.codes reserves it for private testing only) and a real PID before publishing; serial number from the CH32V307 96-bit unique ID
(2) | UAC2 controls: clock source with the advertised rates (CUR/RANGE) and clock valid; Feature Unit mute and volume (CUR/RANGE) mapped to the ES9018K2M attenuator over I²C, plus MCU fine scaling for channel trim; alternate settings for 16, 24 and 32 bit
(3) | Streaming: isochronous OUT → ring buffer → DMA to the CPLD over SPI with chip-select framing (MCU master; one CS frame per block of samples)
(4) | Feedback: an MCU timer counts the CPLD’s LRCLK against USB (micro)frames, plus a small FIFO-level correction, sent in 16.16 format. At 384 kHz, 32-bit stereo: 384 bytes per 125 µs microframe, up to 392 with one extra sample; feedback 48.0 samples per microframe = 0x300000. The same timer checks the LRCLK rate after every family change (within ±0.1 % of the target)

(5)

Application: ES9018K2M driver (asynchronous mode, DPLL bandwidth, 32-bit I²S, soft start, mute, lock status, master trim); break-before-make family change (soft mute, I²S stopped, PLL reset, old enable low, ≥ 1 ms both off, new enable, ≥ 10 ms start-up, PLL lock, LRCLK check, DAC relock, unmute); power-state machine (AMP_EN before AVCC_EN at power-up; controlled power-down ≤ 4 ms after the suspend interrupt: RESETB, AVCC_EN and AUD_EN low, AMP_EN low at + 3.5 ms, then RAIL_EN and ANA_EN), CC monitoring every ≤ 5 ms with the tRpValueChange debounce and the tSinkAdj response, ILIM_HI control, VBUS watchdog at 4.10 V; slow DC tier on every leg (≥ 0.8 V within 1 s, ≥ 0.2 V within 3 s, latch set through ANA_FAULT, active while AMP_EN is high); fault handling (cause capture first at the FLT interrupt, FLT during a controlled power-down or before the first FLT_CLR masked, FLT_CLR timing, volume ceiling, 3-strike stop for DC faults and for overloads at the −12 dB ceiling); calibration storage and test modes (DC fault injection by a digital DC signal; I²S-header tristate)

(6)

CPLD logic: dual-clock FIFO with Gray-coded pointers (written in the 80 MHz system domain, read in the PLL bit-clock domain); I²S output engine clocked from the PLL (×2 on the selected family oscillator: 49.152 MHz or 45.1584 MHz) with exact integer dividers, SDATA and LRCLK changing on the falling BCLK edge; SPI link receiver in the SPI clock domain (chip-select framed) with a toggle synchronizer per 32-bit word; the oscillator enables (OSC48_EN, OSC44_EN), mutually exclusive and never changed in the same cycle, and the PLL reset for the family change; SPI registers on the 80 MHz system clock. No clock multiplexer in the fabric; the MCLK pin is unused (MCLK goes straight from X201 to the DAC)
(7) | MCU–CPLD interface, ours to define: samples by DMA over SPI with chip-select framing (MCU master; SPI clock on a CPLD global-clock-capable input; 24.576 Mbit/s at 384 kHz / 32-bit stereo; I²S is not used, because its frame rate is not locked to the audio rate), FIFO level over SPI, LRCLK back to a timer-capable MCU pin; written as a specification and frozen with the pin map before the Stage 2 board and the schematic

# 9. Risks and open decisions

## 9.1 Risks

Risk | Impact | Mitigation
Own UAC2 firmware and CPLD logic: top risk (host compatibility of high-speed isochronous streaming with feedback) | No working USB audio; schedule | Two-stage proof of concept before layout (Section 8); USBAudioToI2S as a known-good comparison on the same hardware; PC-side unit tests in CI
MCU–CPLD interface specification (SPI with chip-select framing) not yet written | Rework of the pin map or the CPLD logic | Write the specification and freeze the pin map before the Stage 2 board and the schematic
CPLD timing at 80 MHz (system clock) and 49.152 MHz (PLL output), and PLL relock after each family change | Wrong rates, runt pulses or DPLL unlock | Part of the firmware gate; scope check at family changes on the Stage 2 boards
Oscillator disable time and disabled-output state are not specified in the SCTF/YXC datasheets | Contention or runt pulses on the shared PLL input node | Break-before-make with ≥ 1 ms both off; measure on Stage 2 (scope on the shared node); fallback: mux fitted (U205), already built on one Stage 2 board; idle oscillator trace kept short. Gate: Stage 2
AGRV2K I/O state and weak pull-up strength during configuration | A family oscillator enabled while the CPLD configures | The 2.2 kΩ pull-downs hold against ≥ 5.1 kΩ; datasheet check and Stage 2 scope check
CH32V307 SPI maximum clock for the 24.576 Mbit/s link payload | Link too slow for 384 kHz / 32-bit stereo | Confirm in Stage 1
MCU and CPLD currents are assumptions (oscillators at datasheet maxima) | Unconfigured state above 100 mA; Default-mode budget | Measure on the Stage 2 board before layout (gate); lower the MCU clock before configuration if needed
USB Default-mode estimated maximum 0.469 A (31 mA margin) | Default-mode budget | Stage 2 measurement (gate), then the main boards
MCU low-power current with USB wake-up (≤ 1.9 mA assumed) in the suspend budget (≈ 2.2 mA against the 2.5 mA requirement) | USB 2.0 suspend compliance (v1 requirement) | Measured as current vs time on the Stage 2 board (gate), with the real regulators and dummy loads; again on the main boards
DAC pin-to-pin DC mismatch (assumed ≤ 1 mV) and null point (1.702 V from the current-output formula or 1.65 V from the voltage-source model; ±20 mV uncertainty assumed) | Output DC offset (≤ 8.6 / 17.2 mV worst case if the null is 1.65 V) | VREF null test on the proof boards and at bring-up; R433 0 Ω option (VREF 1.650 V); 100 % offset screening with a DC-capable DMM
OPA1622 swing and current capability at +3.78 V / −3.72 V are extrapolated from typical ±18 V curves; the worst unit reaches the swing limit 0.27 dB below full scale at 120 Ω balanced and 3.5 mm 60 Ω | Output power table | Bench-verify the power table in both modes
LM27762 charge-pump resistance at 4.5 V input (3.0 Ω assumed) and the negative-rail brief dropout at the 4.40 V stress corner (−92 mV at current peaks, 4.4 mm 32 Ω, High mode) | Negative-rail margin (0.11 V worst case at VBUS 4.60 V); short clipping on current peaks from a weak host | Measure the negative-rail margin at 4.60 V and the dropout at 4.40 V on the bench
BAV99 forward voltage at ≈ 0.4 µA (0.12–0.40 V over 0–50 °C and unit spread, estimate) | Detector worst case (leg trip up to 0.81 V) | Measure at 0/25/50 °C on the proof boards
Low-stock parts: CH32V307 119, ES9018K2M 724, AGRV2KQ32 980, ME6216A13M3G ≈ 410, 4.4 mm jack 721, OPA2210 76 at JLCPCB, X201 2,503 | Schedule and cost | Reserve parts in the JLCPCB library before ordering
OPA2210 single source: JLCPCB stock (76) and price (JLCPCB US$1.00 vs LCSC US$2.67 at 10+); no qualified second source (OPA2209AIDR stock 0; OPA1612 fails the common-mode range at the minimum rail) | ≈ 1,755 NTD per board at the LCSC price, above the ceiling (owner decision) | Reserve 12 (10 + 2 spares) in the JLCPCB parts library now
Cost 50 NTD under the ceiling (conservative planning estimate) | Budget | The gate covers every JLCPCB line of the real quote, which must pass the ceiling before ordering; gated subtotal and total payable recorded; ≈ 1,552 NTD if the conservative fees do not apply
Residual DC blind region below 0.2 V per leg (below both detection tiers) | Up to 2.5 mW into 16 Ω and 1.25 mW into 32 Ω without a trip | Owner decision pending (proposed: accept)
A rail-stuck hardware failure in High mode delivers up to 26.2 mJ into 16 Ω (worst case, including the after-trip energy) | Energy into a 16 Ω IEM | Within the ≤ 30 mJ limit for v1; v2 option: a fast “leg within 0.5 V of a rail” detector (≈ 1 ms)
Unplug pop and the VBUS watchdog margin (≈ 1 µs at 0.47 A; at full load the logic rails may droop before the sequence completes) | Pop at unplug | Measure at bring-up, and the watchdog-to-GPIO latency on Stage 2; the PGOOD latch is the backstop; DAC-pin safety does not depend on this timing (VREF tracks AVCC)
4.4 mm plug shorted leg+ to leg− (outside TI’s one-amplifier short rating); both jacks live, so a 4.4-to-3.5 mm adapter shorts leg− | OPA1622 stress (≈ 0.55 W per package; ≈ 0.45 W with the adapter) | Bench survival test; warning in the manual
OPA2210 stability with the DAC pin capacitance and the 10 Ω + 660 pF network; OPA2210 output swing (≈ (V+) − 0.3 V estimated); OPA1622 disabled-state output with the network | Oscillation, peaking, clipping or pop | SPICE before layout; bench check
ME6216 power-dissipation rating (0.12 W at 60 mA) and LM27762 θJA (≈ 0.22 W at the worst clean load) | Regulator temperature | Check both datasheets before layout; copper pours; IR check at bring-up

## 9.2 Decisions (closed for v0.7; verification items and one owner decision open)

Decision | Status | Resolution
USB bridge | Closed | WCH CH32V307RCT6 + AGM AGRV2KQ32 CPLD
USB firmware and CPLD logic | Closed (owner decision, 24 Sep 2026) | Our own UAC2 firmware on WCH’s register-level USBHS device examples and our own CPLD logic (Section 8); USBAudioToI2S kept only as a known-good comparison and reference; TinyUSB only if its CH32V307 high-speed audio path proves reliable
DAC and output mode | Closed | ESS ES9018K2M in differential current mode with one I/V converter per pin (ESS application circuit); the newer ES9039Q2M / ES9020Q are a future option
Clock architecture | Closed (changed in v0.6) | DAC MCLK and CPLD system clock 80 MHz from X201 (SCTF SX3M80.000B20F30TNN: 12.5 ns cycle, ≥ 5.6 ns pulse width, ≈ 208 × 384 kHz), DAC in asynchronous mode; family oscillators X202 24.576 MHz and X203 22.5792 MHz, both off by default (2.2 kΩ pull-downs), selected break-before-make in front of the CPLD PLL (×2); all eight rates with exact integer clock ratios and a 50:50 bit clock; DNF mux U205 with R216/R217 input pull-downs as the fallback; no clock multiplexer in the fabric
I/V op-amp | Closed (changed in v0.6) | OPA2210 (single input pair; VREF 0.47 V inside the common-mode range; Vos ±35 µV max; 2.2 nV/√Hz; output swing ≈ (V+) − 0.3 V at ≈ 3 mA) replaces the OPA2197, whose input-pair transition region contains VREF; feedback 836 Ω with 10 Ω + 660 pF; no qualified second source, 12 reserved
Output stage | Closed | 2 × OPA1622 difference amplifiers fed by the I/V outputs, one amplifier per leg; clean envelope ≤ 80 mA peak per leg
Headphone rails | Closed (changed in v0.6) | +3.78 V / −3.72 V from the LM27762 (215 kΩ/100 kΩ and 205.1 kΩ/100 kΩ from Basic values; R518 5.1 kΩ); tolerance ranges include VFB and the 1 % resistors; both rails budgeted at VBUS 4.60 V (negative-rail margin 0.11 V)
Level and calibration | Closed (changed in v0.5) | Every unit calibrated to 1.75 Vrms per leg with the master trim at the end-of-line test; −3.5 dB before calibration, a safety setting against I/V clipping
Power modes | Closed (changed in v0.6) | Default (≤ 500 mA; estimated maximum 0.469 A with hardware-limited analog current) and High (only with a ≥ 1.5 A Type-C advertisement read on CC by the MCU ADC; estimated maximum 0.754 A); CC monitored while configured (tSinkAdj response); bus-powered descriptors 0x80 / 0xFA
Analog current limit | Closed (changed in v0.6) | TPS2553 with two limits (Default 0.157–0.213 A, High 0.393–0.498 A), acting on the instantaneous current; overload → PGOOD bad or a sustained FAULT → fault latch → firmware recovery with the volume ceiling
Power domains | Closed (changed in v0.7) | 3V3M always on; 3V3D (ME6211 #2 CE, behind the R519/R520 dropper with C512 bulk: CPLD, oscillators, DVCC), 3V3A (LP5907 EN, also killed by the latch) and the rails (TPS2553 EN) switched; fixed 1.3 V ME6216A13M3G DVDD fed from 3V3D
Offset limit | Closed (changed in v0.5) | ±10 mV unbalanced and ±20 mV balanced (was ±15 mV), with 100 % screening by a DC-capable DMM
Protection | Closed (changed in v0.7) | LM393 DC detect specified by its worst case (R601–R604 100 kΩ, R609/R610 10 kΩ: 2 V ≤ 59 ms, 1 V ≤ 183 ms); slow firmware DC tier on every leg (≥ 0.8 V in 1 s, ≥ 0.2 V in 3 s) setting the same latch; N-MOSFET latch with ≈ 35 µs capture and C605 on node F (power-on set, set-request stretch), set by PGOOD-bad (Q610), a sustained TPS2553 overcurrent (D606) and the firmware, armed 25–133 ms after PGOOD good and cleared only by the firmware; the latch kills RAIL_EN, AMP_EN and AVCC_EN (Q611); Q609 slow interlock; cause captured at the interrupt; VREF tracks AVCC; VBUS watchdog 4.10 V; no relays
Connectors | Closed | 3.5 mm unbalanced + 4.4 mm balanced; one headphone at a time
Volume | Closed | Host volume (UAC2 Feature Unit) in the ES9018K2M attenuator; hardware knob is a v2 option
Budget | Closed (owner statement, 24 Sep 2026) | Target 1,500 NTD per board (WARN above). Ceiling 1,700 NTD per board (FAIL above), set when the third oscillator was added; on 24 Sep 2026 the owner confirmed the budget is flexible as long as it does not surge; the gate covers every JLCPCB line of the real quote, which must pass the ceiling before ordering, with the gated subtotal and total payable recorded (currently 1,650 NTD: WARNING)
Firmware gate | Open (gate before layout) | Two-stage proof of concept: Stage 1 desk setup and the mandatory Stage 2 board (two boards: shared node and mux, with the real regulators and dummy loads); the USB current, suspend and watchdog-latency measurements on Stage 2 gate the layout; pass criteria in Section 8
MCU–CPLD interface and pin map | Open (before the Stage 2 board) | Write the interface specification (SPI with chip-select framing) and freeze the pin map before the Stage 2 board and the schematic
Oscillator disable time and disabled-output state | Open (Stage 2 measurement) | Not specified in the SCTF/YXC datasheets: measured with a scope on the shared node; fallback: mux U205 fitted (one Stage 2 board is built with it)
MCU → CPLD audio link | Closed (changed in v0.7) | SPI with chip-select framing (MCU master, DMA; one CS frame per block of samples), captured in the SPI clock domain and handed to the 80 MHz system domain with a word toggle synchronizer; I²S is not used for the link; the CH32V307 SPI maximum clock is confirmed in Stage 1
USB currents: unconfigured ≤ 100 mA, Default-mode estimated maximum 0.469 A, suspend ≤ 2.5 mA within 10 ms (v1 requirement) | Open (Stage 2 gate) | Measured on the Stage 2 board before layout (Default mode is 31 mA below 0.5 A; suspend as current vs time from the last bus activity) and again on the main boards
Residual DC blind region < 0.2 V | Open – owner decision pending | Below 0.2 V per leg neither detection tier trips (≤ 2.5 mW into 16 Ω, ≤ 1.25 mW into 32 Ω); proposed: accept
DAC pin mismatch and zero-current point | Open (verification: proof boards and bring-up) | Null 1.702 V (current-output formula) or 1.65 V (voltage-source model): VREF null test on the proof boards, R433 0 Ω option; 100 % offset screening with a DC-capable DMM
OPA2210 stability and output swing; OPA1622 disabled-state output with the network | Open (verification) | SPICE before layout
OPA1622 swing at +3.78 V / −3.72 V and negative-rail margin at 4.60 V | Open (verification) | Bench measurement
Final cost | Open (after layout) | JLCPCB quote from the real BOM/CPL files must pass the 1,700 NTD ceiling with every JLCPCB line included (any fixture line counts); confirm the class of X202; reserve 12 × OPA2210 before ordering; record the gated subtotal and the total payable

# 10. Next steps

# | Action | Done

1 | Owner: decide the residual DC blind region (< 0.2 V) and reserve 12 × OPA2210 at JLCPCB. | ☐
2 | Stage 1 desk proof of concept (USB core, UAC2 controls, streaming with feedback, SPI link clock limit, full chain with CPLD and DAC). | ☐
3 | MCU–CPLD interface specification (SPI with CS framing) and pin map freeze (before Stage 2). | ☐
4 | Stage 2 boards (shared node and mux builds, with the real regulators and dummy loads): clock handover, all 8 rates, USB currents in every state incl. suspend current vs time, watchdog latency — layout gate. | ☐
5 | SPICE: I/V stability, OPA2210 output swing, OPA1622 disabled-state output with the network, protection timing, failed output stage. | ☐
6 | Schematic capture and review against the checklist (AI agent + netlist script); layout; JLCPCB quote (gated subtotal ≤ 1,700 NTD per board, total payable recorded). | ☐
7 | Bring-up and end-of-line tests (calibration, DMM offset screening, protection incl. failed-output emulation and short PGOOD pulses, firmware DC tier, USB and suspend, pop, DAC pin vs AVCC, jitter/clock, rails, power and dissipation). | ☐

# Appendix A. Reference documents

Ref | Document | Source
[1] | ES9018K2M datasheet v3.7 (22 Apr 2021) | ESS Technology
[2] | OPA1622 datasheet (SBOS727B) | Texas Instruments
[3] | OPA197/OPA2197 datasheet (SBOS737C): input-pair transition region, table 6.8 and section 7.3.6 (the fifth-round finding against the former I/V op-amp) | Texas Instruments
[4] | LM27762 datasheet (SNVSAF7C) | Texas Instruments
[5] | TPS2553 datasheet (SLVS841F) | Texas Instruments
[6] | CH32V307 datasheet and EVT package (high-speed USB device examples) | WCH
[7] | AGRV2K CPLD datasheet | AGM
[8] | USBAudioToI2S: UAC2.0-to-I²S firmware for MCU + CPLD (Apache-2.0); known-good comparison and reference | GitHub, LoveLonelyTime/USBAudioToI2S
[9] | USB Type-C specification (current-advertisement voltage bands) | USB-IF
[10] | JLCPCB PCBA price list | JLCPCB
[11] | Schematic Design Notes v0.6 (companion document: block-level circuit guidance and chosen parts) | This project
[12] | Parts List v0.5 (source of truth for cost) | This project
[13] | OPA210/OPA2210 datasheet (SBOS924H, Aug 2021): I/V converters U403 and U404; output swing, absolute maximum input current and section 7.3.5 | Texas Instruments
[14] | 3C series oscillator datasheet (X201, SX3M80.000B20F30TNN: 40 mA max for 80–160 MHz) | SCTF
[15] | 2CM series oscillator datasheet, manufacturer file “2CM-Series-2024-11-04” (X203: tri-state pin 1, start-up ≤ 5 ms) | SCTF
[16] | YSO110TR oscillator datasheet (X202: tri-state pin 1, start-up ≤ 3 ms) | YXC
[17] | USB Type-C sink timing (tSinkAdj 60 ms max, tRpValueChange 10–20 ms), as quoted in the Zephyr USB-C stack and the Chromium EC documentation | USB-IF specification; Zephyr Project; Chromium OS EC
[18] | LP5907 datasheet: 230 Ω output auto-discharge (3V3A fall time and VREF tracking) | Texas Instruments
[19] | ME6211 datasheet: 300 mW power dissipation rating in SOT-23 (absolute maximum; U504 dissipation) | Microne

# Appendix B. Revision history

Version | Date | Author | Description
v0.1 | 23 Sep 2026 | Diego Yang | Draft for review
v0.2 | 23 Sep 2026 | Diego Yang | Budget raised to ≤ 1,500 NTD; outputs changed to 3.5 mm unbalanced + 4.4 mm balanced; parts and targets verified against the XU316-1024-QF60A, AK4493S, AKD4493S-A and OPA1622 datasheets; USB chip changed to XU316-1024-QF60A (1.8 V I/O); OPA1612 stage-1 and LT3045 added; CH224K replaced by CH224Q; JLCPCB fees updated to the 8 Sep 2026 price list; most open decisions closed.
v0.3 | 23 Sep 2026 | Diego Yang | Remaining parts chosen from stocked LCSC/Digi-Key parts; CH224A replaces CH224Q; TPS7A4901 replaces LT3045 to stay within 1,500 NTD; protection defined (LM339 + 2 × HFD4 relays with hardware amplifier shutdown); cost re-estimated with real prices at ≈ 1,490 NTD; −14 V rail set to −14.7 V; stage-1 count corrected to one dual OPA1612.
v0.4 | 23–24 Sep 2026 | Diego Yang | Cost-driven redesign for the 5-board budget: single USB-C bus-powered design; CH32V307 + AGRV2K CPLD USB bridge (open-source USBAudioToI2S); ES9018K2M DAC; 2 × OPA1622 as four difference amplifiers; LM27762 charge-pump rails; relays replaced by a 3.3 V hardware fault latch; three design reviews dispositioned. Revised on 24 Sep 2026: DAC output moved to current mode with I/V converters (owner decision, option B) and an owner-approved cost ceiling of 1,550 NTD per board.

v0.5

24 Sep 2026

Diego Yang

Fourth review round (R4-A, R4-B, R4-C) dispositioned (Appendix C): headphone rails ±3.78 V; per-unit calibration to 1.75 Vrms per leg (Rf 836 Ω); power rated at 1 % THD+N or calibrated 0 dBFS, with High and Default modes; TPS2553 current limit and switched power domains per USB state; OPA2197 I/V converters; DAC in asynchronous mode from a 100 MHz MCLK; first issued with the interim both-edge divider for the 44.1 kHz family and amended the same day to three oscillators (next row); protection completed (PGOOD kill, blanked latch, energy bound at the terminals); fixed 1.3 V DVDD LDO; balanced offset limit ±20 mV with 100 % screening; Parts List v0.3 with verified LCSC numbers and classes; cost 1,540 NTD per board (WARNING, under the 1,550 NTD ceiling); pre-layout firmware gate.

v0.5 amendment

24 Sep 2026

Diego Yang

Amendment for the owner decisions of 24 Sep 2026: family oscillators for exact bit clocks, because the ES9018K2M requires a bit-clock duty cycle of 45:55 to 55:45 and one 100 MHz clock for both families gave 40:60 at 352.8/384 kHz. First X202, 24.576 MHz (YXC OT322524.576MJBA4SL), for the 48 kHz family; then, at the owner’s request, X203, 22.5792 MHz (SCTF SX2M22.5792M20F30TNN), for the 44.1 kHz family, which replaced the interim both-edge fractional divider and its 352.8 kHz condition. Final clock architecture: DAC MCLK 100 MHz unchanged, family oscillator selected by its enable pin in front of the CPLD PLL (×2), all eight rates exact, family change with the PLL held in reset, no clock multiplexer in the fabric. Own UAC2 firmware and CPLD logic instead of modifying USBAudioToI2S (kept as a known-good comparison), with the firmware gate run as a two-stage proof of concept. Currents updated (Default ≤ 0.473 A, High ≤ 0.758 A); cost 1,540 → 1,602 → 1,666 NTD per board (WARNING), approved ceiling raised from 1,550 to 1,650 and then 1,700 NTD; Figures 1 and 2 updated.

v0.6

24 Sep 2026

Diego Yang

Fifth review round (R5-A, R5-B, R5-C of the amended Spec v0.5) dispositioned (Appendix C): 80 MHz MCLK and CPLD system clock (SCTF SX3M80.000B20F30TNN) below the DAC limit; family oscillators off by default with a break-before-make handover, a node pull-down and a DNF mux fallback (U205); MCU link captured in its own clock domain; OPA2210 I/V converters (single input pair); rails +3.78 V / −3.72 V including resistor tolerance (R518 5.1 kΩ); fault latch also set by PGOOD-bad (Q610) and a sustained TPS2553 overcurrent (D606); rails-first-off power-down, VBUS watchdog 4.10 V dropping AMP_EN and RAIL_EN, VREF clamp D401 and C421 100 nF; protection envelope by DC magnitude with recalculated terminal energies; Default-mode power rated from the instantaneous peak current; USB estimated maxima 0.469 A (Default) and 0.754 A (High); mandatory Stage 2 board with the USB current measurements as a layout gate; DC offset screening with a DC-capable DMM; J703 MCLK monitor-only; document-lint CI check; cost 1,647 NTD per board (WARNING, 53 NTD under the 1,700 NTD ceiling, recorded with the owner statement of 24 Sep 2026); Figures 1 and 2 updated; companion documents Schematic Design Notes v0.5 and Parts List v0.4.

v0.7

24 Sep 2026

Diego Yang

Sixth review round (R6-A, R6-B, R6-C and R6-D of Spec v0.6) dispositioned (Appendix C): latch capture ≈ 35 µs with C605 on node F (power-on set, set-request stretch), 47 kΩ latch pull-ups, Q609 as a slow interlock and Q611 killing AVCC_EN; worst-case DC detector (R601–R604 100 kΩ, R609/R610 10 kΩ: 2 V ≤ 59 ms, 1 V ≤ 183 ms) and worst-case terminal energies (26.2 / 13.3 mJ at 16 / 32 Ω including ≤ 0.6 mJ after the trip); slow firmware DC tier through the MCU ADC (≥ 0.8 V in 1 s, ≥ 0.2 V in 3 s) setting the same latch, with the residual below 0.2 V as a pending owner decision; fault-cause capture at the interrupt and a 3-strike rule for DC faults; VREF tracks AVCC (C421 330 pF; D401 and C422 removed) and the DAC analog supply turns off first, so a controlled power-down takes ≤ 4 ms; USB suspend ≤ 2.5 mA within 10 ms as a v1 requirement; pop definition; regulator dissipation table with the R519/R520 dropper and C512; DAC centre-voltage alternative with the R433 option; OPA2210 output swing and the −3.5 dB safety default; SPI link with chip-select framing; SDATA/LRCLK on the falling BCLK edge; mux pull-downs R216/R217; 31 test pads; Stage 2 with the real regulators (≈ US$90 ≈ 2,860 NTD); cost 1,650 NTD per board (WARNING, 50 NTD under the 1,700 NTD ceiling, gate covering every JLCPCB line); Figure 1 updated; companion documents Schematic Design Notes v0.6 and Parts List v0.5.

# Appendix C. Design review disposition

Status values: Closed = fixed in this revision; Closed – design, verify = design change made, confirmed by a bench or firmware-gate check; Closed – verify = resolved, confirmed at the firmware gate, on the proof boards or at bring-up; Closed – N/A = not applicable after the v0.4 redesign; Open – owner decision = awaiting the owner’s decision; Open – tracked = tracked item with an owner and a gate (Section 9.2).

## C.1 Sixth review round (R6-A, R6-B, R6-C and R6-D of Spec v0.6)

Finding IDs: R6-A = review 1 (latch timing, power-down, suspend, fault test, cause capture, cost gate), R6-B = review 2 (worst-case protection, blind region, suspend wording, fixture in the gate), R6-C = review 3 (3-strike lockout, mux inputs, OPA2210 single source, minors), R6-D = review 4 (pop vs offset, latch on controlled power-down, LDO dissipation, DAC centre voltage, OPA2210 output swing, watchdog timing, rail floating, 3V3D bulk, minors). The reviews covered Spec v0.6, Schematic Design Notes v0.5 and Parts List v0.4; findings raised by more than one reviewer are dispositioned together.

ID | Finding | Disposition in v0.7 | Status
R6-A1 | Latch can miss short PGOOD faults; latch delay missing from the energy figures | C605 moved to node F (power-on set and ≥ 1.5 ms set-request stretch); 47 kΩ latch pull-ups; capture ≈ 35 µs (budget 0.1 ms); Q609 slowed to a static interlock (6–32 ms), so a PGOOD glitch either latches or does nothing; energy computed through the rail-disable instant | Closed – design, verify
R6-A2 | Power-down does not establish safe DAC-pin voltage or the post-trip energy bound | VREF tracks AVCC (C421 330 pF; D401, C422 removed); DAC analog off first with the I/V and legs powered, rails last; latch also kills AVCC_EN (Q611); after-trip bound 0.51 mJ (both rails, C +10 %, maximum rails) + ≤ 1 µJ back-power → ≤ 0.6 mJ; unplug case bench-checked | Closed – design, verify
R6-A3 | ≥ 50 ms shutdown conflicts with USB suspend timing | Power-down ≤ 4 ms after the suspend interrupt, suspend level ≈ 7 ms after the last bus activity; suspend is a v1 requirement; Stage 2 carries the real regulators with dummy loads and measures current vs time | Closed – design, verify
R6-A4 | Hardware fault test tests detection, not removal | Detector test kept; failed-output emulation from the board’s own rail through an external switch with dummy loads, V²/R integrated; FLT high; no +20 % allowance | Closed
R6-A5 | PGOOD read after the trip cannot identify the cause | Per-leg DC readings (independent ADC path) and the firmware-trip flag stored first at the interrupt; ≥ 0.3 V → DC fault; unknown → DC fault | Closed – design, verify
R6-A (cost) / R6-B4 | Fixture fee outside the ceiling | Gate covers every JLCPCB line incl. any fixture; gated subtotal and total payable recorded; the fixture sentence is standard page text | Closed
R6-B1 | Protection limits are nominal | Full worst case (R, C incl. DC bias, LM393 offset, BAV99 VF, rails); R601–R604 100 kΩ, R609/R610 10 kΩ → 2 V ≤ 59 ms (41 % margin), 1 V ≤ 183 ms (27 %); energy 26.2 / 13.3 mJ worst ≤ 30 / 15 mJ | Closed – design, verify
R6-B2 | 0.755 V blind region is a product-safety decision | Firmware slow tier on every leg (≥ 0.8 V in 1 s, ≥ 0.2 V in 3 s) sets the same latch; residual < 0.2 V (≤ 2.5 mW into 16 Ω) | Open – owner decision
R6-B3 | Suspend wording contradicts the gate | Suspend ≤ 2.5 mA is a v1 requirement everywhere | Closed
R6-B (cost) / R6-C3 | OPA2210 single source decides the ceiling | No qualified second source (OPA2209AIDR stock 0; OPA1612 fails the common-mode range at the minimum rail); reserve 12; fallback LCSC price | Open – tracked
R6-C1 | Default-mode overloads can lock the board off | Overloads count toward the 3-strike stop only at the −12 dB ceiling; DC faults counted | Closed
R6-C2 | Mux inputs float with U205 fitted | DNF R216, R217 10 kΩ pull-downs fitted with U205 | Closed
R6-C (minor) | Clipping before a trip near the Default limit; link framing | Scope test added; SPI with chip-select framing | Closed
R6-D1 | Pop target conflicts with the offset limit | Pop defined as the band-limited transient beyond the settled DC step; legs enabled/disabled while VREF = 0; SPICE item for the disabled-state output | Closed – verify
R6-D2 | Every controlled power-down sets the latch | Expected and masked by firmware (not logged, counted or applied) | Closed
R6-D3 | LDO dissipation not analysed | Dissipation table; R519 + R520 dropper keeps U504 ≤ 0.20 W; copper and IR check | Closed – verify
R6-D4 | Two DAC centre voltages | Both ESS values stated; offset 8.6 mV worst if 1.65 V; R433 0 Ω option | Closed – verify
R6-D5 | OPA2210 output swing not quantified | ≈ (V+) − 0.3 V at ≈ 3 mA; 0.43 V margin calibrated; −3.5 dB pre-calibration default is a safety setting; SPICE | Closed – verify
R6-D6 | VBUS watchdog timing margin | Quantified (≈ 1 µs margin at 0.47 A); PGOOD latch as backstop; latency measured on Stage 2 | Closed – verify
R6-D7 | Positive rail can float during the rails-off window | Window removed by the new order; the latch trip collapses AVCC in hardware | Closed
R6-D8 | 3V3D bulk capacitance | C512 10 µF at U504 | Closed
R6-D (minor) | ≈ 208 ×; attach charge; test-pad table; node F margin; BCLK edge; DR loopback floor; A-M2 bracket (Spec v0.6 Section C.2, now C.3) | All updated as listed in this round | Closed

## C.2 Fifth review round (R5-A, R5-B and R5-C of the amended Spec v0.5)

Finding IDs: R5-A = review 1, R5-B = review 2, R5-C = review 3. Findings raised by more than one reviewer are dispositioned together. Kept as history: the dispositions as issued in v0.6; where the sixth round changed a value, the v0.7 value is added in brackets and Section C.1 applies.

ID | Finding | Disposition in v0.6 | Status
R5-A1 / R5-B1 | Spec §4 Key-parts table showed placeholder tokens | The saved v0.5 table was repaired during the amendment (the review saw an interim copy); v0.6 table rebuilt and the saved file scanned for tokens; CI document-lint check added | Closed
R5-A2 / R5-B6 / R5-C1 | Shared oscillator outputs need break-before-make; X203 enabled when OE is open | Both enables 2.2 kΩ pull-downs (off at power-up and during CPLD configuration); node pull-down R214; enables mutually exclusive in CPLD logic; sequence with ≥ 1 ms both-off, ≥ 10 ms start-up, PLL held in reset; SCTF/YXC datasheet facts cited (no disable time specified → measured); DNF mux U205/R215 fitted on one Stage 2 board | Closed – design, verify
R5-A3 / R5-B2 | 100 MHz MCLK at or above the DAC limit; “worst duty” wording | 80 MHz SCTF SX3M80 (12.5 ns cycle, ≥ 5.6 ns pulse, ≈ 208 × 384 kHz); “ideal duty 50 %”; all 8 rates stay in the gate | Closed – design, verify
R5-A4 | 0.473 A is an estimate, not a whole-board limit; CC changes not monitored | “Estimated maximum with hardware-limited analog current”, now 0.469 A; Stage 2 measurements before layout; CC monitoring within tSinkAdj | Closed – design, verify
R5-A5 | OPA2197 input-pair transition region at VREF | OPA2210 (single input pair, 0.47 V common-mode margin, 35 µV, 2.2 nV/√Hz) | Closed
R5-A6 | Shutdown back-powering; AVCC can collapse faster than VREF | ES9018K2M abs. max cited; rails-first-off power-down; watchdog also drops RAIL_EN; VREF clamp D401 and C421 100 nF [v0.7: VREF tracks AVCC with C421 330 pF, D401 and C422 removed, DAC analog off first; see R6-A2] | Closed – design, verify
R5-A7 / R5-B3 | Overload restarts when PGOOD recovers; overload does not latch | Q610 (PGOOD bad) and D606 (TPS2553 FAULT) set the latch; firmware clear required; ≥ 1 s recovery, ceiling steps, 3-strike stop [v0.7: overloads count toward the stop only at the −12 dB ceiling; see R6-C1] | Closed – design, verify
R5-A8 / R5-B5 | Protection envelope and terminal energy | Envelope by DC magnitude (t(V)); energies recalculated as V²/R × t for digital DC and a rail-stuck failure; both rails 0.46 mJ; hardware fault-injection test added [v0.7: worst-case envelope, 26.2 / 13.3 mJ at 16 / 32 Ω including ≤ 0.6 mJ after the trip; failed-output emulation without allowance; see R6-B1, R6-A2 and R6-A4] | Closed – design, verify
R5-A9 | Divider resistor tolerance omitted | Included; R518 5.1 kΩ (−3.722 V); design-corner margin 0.11 V | Closed
R5-A10 / R5-C5 | Balanced DR advantage assumes uncorrelated noise | Correlated model: balanced ≈ 120.3 vs unbalanced ≈ 119.5 dB(A) (+0.85 dB) | Closed
R5-A11 | QA403 cannot measure DC offset | DC-capable DMM for the 100 % offset screening | Closed
R5-A12 | External MCLK contention at the test header | J703 MCLK is a monitor output via R703 1 kΩ; external source drives BCLK/LRCLK/SDATA only | Closed
R5-A13 / R5-B9 | 1,700 NTD called “owner-approved”; ceiling policy | Owner statement recorded (budget flexible as long as it does not surge); 1,700 kept as the hard order gate; the JLCPCB quote must pass; exclusions listed; estimate now 1,647 [v0.7: 1,650; the gate covers every JLCPCB line] | Closed
R5-A14 | “Every class verified” wording; fixture fee not included | X202 exception stated; possible fixture fee (X202 and OPA2210 pages) listed as excluded, to confirm in the quote [v0.7: the fixture sentence is standard page text; any fixture line counts toward the gate; see R6-A (cost) / R6-B4] | Closed
R5-B4 | USB compliance only at bring-up | Stage 2 mandatory; unconfigured, configured and suspend currents measured before layout; layout blocked unless all pass | Closed – design, verify
R5-B7 | “Exact sample rates” | “Exact integer clock ratios”; absolute rate within the oscillator tolerance, absorbed by the asynchronous feedback | Closed
R5-B8 | Stage 2 should be mandatory | Mandatory, ≈ US$79 ≈ 2,500 NTD for two boards (outside the board budget) [v0.7: ≈ US$90 ≈ 2,860 NTD with the real regulators and dummy loads] | Closed
R5-C2 / R5-C3 | Close the X203 datasheet item; “only one runs” wording; PLL ×2 justification | Datasheet facts cited; “only one drives the node”; idle-trace rule; PLL ×2 also fixes the 45–55 % oscillator duty | Closed
R5-C4 | Default-mode power from average current | Instantaneous-peak method; new table and targets | Closed
R5-C6 | Blanking 28–119 ms vs 100 ms wait | 25–133 ms incl. R/C tolerance; AMP_EN after PGOOD good ≥ 150 ms; FLT_CLR after ≥ 200 ms rails off | Closed
R5-C7 | 0.1 V margin on the 4.30 V VBUS watchdog | 4.10 V (3.95–4.25 V), ≥ 0.15 V margin to the 4.40 V stress corner | Closed
R5-C8 | K1000 swing margin ≈ 0.06 dB | With resistor tolerance the worst unit reaches the swing limit 0.27 dB below full scale at 120 Ω balanced; rated as swing-limited; bench-verified | Closed – verify
R5-C9 | Continuous CC monitoring | Firmware requirement (≤ 5 ms sampling, tRpValueChange debounce, tSinkAdj response) | Closed – design, verify
R5-C10 | MCU link sampled by the system clock | Link captured in its own clock domain with a word toggle synchronizer [v0.7: SPI with chip-select framing] | Closed – design, verify
R5-C11 | Versioning and stale rows | New files Spec v0.6 / Notes v0.5 / Parts List v0.4; Spec history notes that v0.5 first used the interim divider; Notes earlier-round rows R1-B1 (7.7 µF) and R2-M5 (1,550 / 1,536) marked as the design at that time with the current values [v0.7: Spec v0.7 / Notes v0.6 / Parts List v0.5] | Closed

## C.3 Fourth review round (reviews R4-A, R4-B and R4-C of Spec v0.4)

Finding IDs: A- = R4-A, B- = R4-B, C- = R4-C. Kept as history: the dispositions as issued in v0.5. Where the fifth or sixth round changed the design (for example the MCLK, the I/V op-amp, the rails, the USB estimate, the protection and the cost), Sections C.1 and C.2 and the body of this specification are current; where a row still quotes an older number, the current value is added in brackets.

ID | Finding | Disposition in v0.5 | Status
A-H1 | FB101 mis-specified (GZ1608D601TF = 200 mA / 450 mΩ, C1002; C1015 is GZ2012D101TF) | Power ferrite now Murata BLM18PG121SN1D (C14709, Basic, 2 A, 50 mΩ) in the 5V_ANA path; GZ1608D601TF (C1002) only on DVCC (≈ 14 mA); drops recomputed (≈ 15–25 mV) | Closed
A-H2 | Offset used OPA1678 typical as maximum | Confirmed (±0.5 typ / ±2 mV max); I/V op-amp now OPA2197 (±0.25 mV max); budget 7.9 / 15.9 mV worst, balanced limit ±20 mV, 100 % screening; DAC-mismatch assumption Open (measure) [v0.7: OPA2210, 7.0 / 14.0 mV worst] | Closed
A-H3 | Safe disconnected output not established | Full sequence and current paths, rails first on/last off, PGOOD hardware kill, back-powering bounded (≤ 1.7 mA/pin) and removed in 10 ms, energy bound ≤ 16.5 mJ before / ≤ 0.22 mJ after the trip, protection defined at the headphone terminals [v0.7: legs on before AVCC, DAC analog off first; ≤ 30 / 15 mJ worst case at 16 / 32 Ω including ≤ 0.6 mJ after the trip] | Closed – design, verify
A-H4 | Negative-rail headroom | Rails ±3.78 V; both rails budgeted at 4.60 V and maximum load with a 3.0 Ω charge-pump resistance (margin 0.17 V) [v0.7: +3.78 V / −3.72 V, margin 0.11 V] | Closed
A-H5 | 100 mA ceiling not enforced | Clean envelope (80 mA/leg, swing curve) separated from overload; TPS2553 enforces the analog supply current; PGOOD kill; firmware ceiling steps; overload dissipation bounded; overload tests replace the 30-min 32 Ω balanced test | Closed – design, verify
A-H6 | USB power states and descriptors | State-by-state budget, MCU-only before configuration (≤ 83 mA estimate), descriptors 0x80/0xFA, CC detection by ADC for High mode, suspend policy (2.5 mA Open); verified in the firmware gate [v0.7: suspend ≤ 2.5 mA within 10 ms is a v1 requirement] | Closed – design, verify
A-M1 | Mixed purchasing lines and placeholder ranges | One part per line, every value specified, 48 purchasing lines by LCSC number [v0.7: 47 purchasing lines] | Closed
A-M2 | 13.8 NTD ceiling margin; one Basic→Extended flip fails it | Every class now verified on the JLCPCB page (X202 assumed Extended); Extended count conservative (19, incl. THT jack and X202); 34 NTD under the 1,700 NTD ceiling [v0.7: 50 NTD under]; still a planning estimate until the JLCPCB quote | Closed – verify
A-M3 | Gain tolerance defeats the minimum power targets | Per-unit calibration to 1.75 Vrms/leg; targets defined at the calibrated level | Closed
A-M4 | Two LDOs do not guarantee sequencing | Separate enables (LP5907 EN, ME6211 CE) in a firmware sequence; DVDD LDO fed from 3V3D so DVDD ≤ DVCC by construction; scope check at bring-up | Closed – design, verify
A-M5 | Clock adaptation needs an earlier gate | Three oscillators: 100 MHz straight to the DAC MCLK (asynchronous mode) and the CPLD system clock [v0.7: 80 MHz]; 24.576 MHz or 22.5792 MHz selected in front of the CPLD PLL (×2) for the two families (exact ratios); pre-layout firmware gate as a two-stage proof of concept | Closed – design, verify
B-S1 | −4.5 V rail cannot regulate from USB | As A-H4 | Closed
B-S2 | 2.0 Vrms/leg does not fit the supply; +1 dB units clip | Calibrated 1.75 Vrms/leg; swing model from OPA1622 Fig. 38/39; pre-calibration trim −3.5 dB | Closed
B-S3 | Power targets fail on low-spread units; rating method | As A-M3: “1 % THD+N or calibrated 0 dBFS, whichever first” | Closed
B-S4 | Firmware needs much more than the spec said | Own UAC2 firmware and CPLD logic, modules listed (Section 8); two-stage proof of concept before layout; 352.8 kHz from the 22.5792 MHz oscillator through the CPLD PLL (exact) | Closed – verify
B-S5 | 14 NTD margin will be used up (odd values, 1.5 nF C0G, crystal, AMS1117, THT jack fee) | Basic E24 values or Basic combinations used (100 k + 47 k, 1 k ∥ 5.1 k, 15 k + 1 k, 2 × 330 pF), Basic 5032 crystal, AMS1117 removed, THT fee counted; no cheaper 4.4 mm jack exists at LCSC (SMD option not available) | Closed – verify
B-M1 | Pop at unplug has no hardware control | PGOOD gates AMP_EN in hardware; VBUS watchdog; separate unplug pop target (≤ 20 mV) | Closed – design, verify
B-M2 | Fault latch re-trips on clear | Set path blanked ≈ 60 ms after PGOOD good, without clearing the latch [v0.7: 25–133 ms] | Closed
B-M3 | PLL jitter goes to the DAC in sync mode | DAC still in asynchronous mode with no PLL in the MCLK path (MCLK straight from the 100 MHz oscillator [v0.7: 80 MHz]); the CPLD PLL is only in the bit-clock path of both families, whose jitter the DAC’s DPLL rejects; J-test stays in the plan | Closed
B-M4 | > 100 mA before enumeration; phones limit OTG | As A-H6; Default mode ≤ 0.473 A covers phones [v0.7: 0.469 A] | Closed
B-M5 | AMS1117-ADJ needs tantalum-type capacitor and minimum load | Fixed 1.3 V ME6216A13M3G (±1 %, 300 mA, ceramic-stable) | Closed
B-minor | Duplicate “v0.4” rows in Appendix B; U301 “voltage-mode” text; HSE 8 MHz; VREF risk overstated | History cleaned (this is v0.5); U301 text corrected; HSE 8 MHz confirmed; VREF risk downgraded and quantified (1.17 mV) | Closed
C-B1 | USB power before configuration | As A-H6 | Closed – verify
C-B2 | Reference descriptors wrong (self-powered, 100 mA) | 0x80 / 0xFA in the firmware gate | Closed – verify
C-B3 | 352.8 kHz MCLK not supported by the reference CPLD | Confirmed in source; replaced by our own CPLD logic with the family oscillator selected before the PLL, as the reviewer suggested (X202 24.576 MHz or X203 22.5792 MHz, PLL ×2); all eight rates exact; MCLK 100 MHz straight to the DAC (asynchronous mode) [v0.7: 80 MHz] | Closed – design, verify
C-B4 | Clock-family switching can glitch | MCLK never switches; the family changes by the oscillator enables while the I²S output is stopped and the PLL is held in reset; no clock multiplexer in the fabric; scope check for runt pulses | Closed – design, verify
C-B5 | Host volume not implemented | UAC2 volume/mute with GET/SET CUR/RANGE and I²C mapping, tested on three OSes in the gate | Closed – verify
C-B6 | “100 mA design current” not implemented | As A-H5 | Closed – design, verify
C-H1 | 500 mA budget has no margin | Default mode ≤ 0.473 A enforced (27 mA margin, measured at bring-up) [v0.7: 0.469 A estimated maximum, 31 mA margin]; High mode only with a ≥ 1.5 A Type-C advertisement | Closed
C-H2 | +4.5 V corner | Rails ±3.78 V, both rails budgeted | Closed
C-H3 | 7.7 µF table is not an inrush proof | Attach charge 38 µC including 3V3M output capacitance [v0.7: ≈ 40 µC]; staggered, soft-started domains | Closed – verify
C-H4 | Cost provisional; “Assign LCSC no.” left; “every part is LCSC” inaccurate | Every line has an LCSC number and verified class | Closed
C-H5 | Offset margin | As A-H2 | Closed
C-H6 | ≤ 5 mV pop ambitious without relays | Split targets, full sequence incl. unplug/brownout validated on the bench | Closed – verify
C-H7 | USB identity (WCH VID, PID 0) | Use the pid.codes VID 0x1209 with an assigned PID; serial number from the MCU unique ID | Closed – verify

## C.4 Earlier review rounds (three reviews of Spec v0.3)

These findings were dispositioned in v0.4 and updated to the design of v0.5; they are kept as history. Where a disposition quotes a value that v0.6 or v0.7 changed, the current value is added in brackets, and the later findings in Sections C.1 and C.2 apply.

ID | Finding | Disposition (design at v0.5; later values in brackets) | Status
R1-B1 | VBUS_PD capacitance ≈ 130 µF vs the USB-C limit of 10 µF | No PD port; single 5 V port; attach charge ≈ 38 µC (see C-H3) (v0.7: ≈ 40 µC) | Closed – N/A
R1-B2 | LMR33630 + SMAJ18A surge stacking ≈ 44 V | No inverting converter and no 15 V input; the LM27762 runs from 5 V | Closed – N/A
R1-B3 | LP5907 on 1V8_D over 10 µF output capacitance | No 1.8 V rails; the only LP5907 (DAC 3.3 V) is kept within its 10 µF output-capacitance limit | Closed – N/A
R1-B4 | Paralleling topology left open | No paralleling; one amplifier per leg with a clean envelope of ≤ 80 mA peak (see A-H5) | Closed
R1-B5 | LM339 at −12 V pulling 1.8 V logic | The comparator outputs reach the 3.3 V domain only through a 10 kΩ / 47 kΩ node clamped by a 1N4148WS; the latch uses N-MOSFETs only, and 3.3 V nodes never go below 0 V | Closed
R1-B6 | Offset target ±5 mV vs an 11 mV worst case | Worst case recomputed with datasheet maxima (7.9 / 15.9 mV at v0.5; v0.6: 7.1 / 14.3 mV; v0.7: 7.0 / 14.0 mV); limits ±10 / ±20 mV with 100 % screening (see A-H2) | Closed
R1-H | AMS1117 dropout and noise | ME6211 for digital 3.3 V; LP5907 for DAC analog 3.3 V; fixed 1.3 V ME6216A13M3G for DVDD (see B-M5) | Closed
R1-H | XU316 VOH vs AK4493 VIH | All logic is 3.3 V | Closed – N/A
R1-H | Both jacks live; gain-switch pop | Gain switch removed; both jacks live documented (one headphone at a time) | Closed
R1-H | OPA1622 stock 197 vs 400 needed | The 5-board sample run needs 10 (2 per board) | Closed
R1-H | LM317/LM337 cost trade | LM27762 low-noise LDOs | Closed – N/A
R1-H | CI rule “every part has an LCSC number” vs Digi-Key/Mouser parts | Every fitted part has an LCSC number and a JLCPCB class (Parts List v0.3, see C-H4) (v0.6: every class from its JLCPCB part page or the basic-parts list, except X202, assumed Extended; see R5-A14) | Closed
R1-H | Firmware port map before layout | Pre-layout firmware gate as a two-stage proof of concept (Section 8, see B-S4); the MCU–CPLD interface and the pin map are frozen before the proof-of-concept board and the schematic | Closed
R1 consistency | v0.2 wording, cost source of truth, THD+N conditions, Zout including contacts, DSD pins, grounding/ESD/CC/silkscreen | Fixed in the spec: the single USB-C port removes the silkscreen confusion; CC = 5.1 kΩ Rd; jack ESD LESD5D5.0CT1G; grounding rules added; DSD not in v1 | Closed
R2-S1 | TVS does not protect the −14.7 V converter; no OVP | No 15 V input and no inverting converter | Closed – N/A
R2-S2 | VBUS bulk before the PD contract; analog rails start at 5 V | No PD contract; single 5 V port | Closed – N/A
R2-S3 | Balanced output impedance with option B | The OPA1622 legs drive the jacks directly, no ballast (< 0.1 Ω + contacts) | Closed
R2-S4 | K1000 1 W with no margin | Closed by requirement change (budget redesign): ≈ 102 mW and ≈ 94 dB SPL into the K1000 documented at v0.5 (v0.6: 95.9 mW and ≈ 93.8 dB SPL in High mode, 39.2 mW and ≈ 89.9 dB SPL in Default mode) | Closed
R2-S5 | Offset target contradicts the design | As R1-B6 | Closed
R2-M1 | Board ≈ 7 W in a PLA case | Analog input power bounded by the TPS2553 limit; board ≈ 3.8 W worst case (High mode, overload); overload tests (Section 7) | Closed
R2-M2 | LM317 near dropout; LM337 LC filter | Blocks removed (LM27762) | Closed – N/A
R2-M3 | ±0.05 dB trim cannot use 0.5 dB DAC steps | Optional digital scaling in the MCU firmware | Closed
R2-M4 | Maximum-power criterion | Rated at 1 kHz, both channels, at 1 % THD+N or calibrated 0 dBFS, whichever comes first (see B-S3) | Closed
R2-M5 | Cost margin 10 NTD; exchange rate | Gate uses a fixed 31.7 NTD/US$: target 1,500 NTD per board (WARN above) and a 1,700 NTD ceiling (FAIL above); 1,666 at v0.5 (v0.6: 1,647 NTD; v0.7: 1,650 NTD, WARNING; ceiling recorded with the owner statement of 24 Sep 2026, see R5-A13) | Closed
R2-M6 | 4.4-to-3.5 mm adapter shorts leg− | One amplifier per package shorted (TI continuous-short rating), ≈ 0.45 W per package; risk and manual warning | Closed
R2-M7 | Unbalanced crosstalk needs ≤ 6 mΩ shared ground | Layout rule (≤ 5.7 mΩ) | Closed
R2 minor | Stale versions; KC2520Z “(assumed)”; through-hole count; pop requirement; unverified CH224A/AMS1117 claims; NVIDIA paragraph | Versions fixed; the three oscillators are counted as leadless conservatively; only the 4.4 mm jack is through-hole (confirm USB-C shell pegs); pop ≤ 5 mV controlled and ≤ 20 mV at unplug; CH224A removed; unverified regulator claims removed (see B-M5); job-application text moved to the repository README | Closed
R3-1 | DC fault latch and recovery | Hardware 3.3 V latch; firmware recovery policy (Section 5.3); status to the MCU | Closed
R3-2 | TVS/converter envelope | No 15 V input and no converter | Closed – N/A
R3-3 | Stage-1 gain 0.9009 with the input network | The gain includes the DAC’s 806 Ω source (current mode, gain = 2 × Rf/806 per leg); v0.5 uses Rf = 836 Ω and per-unit calibration to 1.75 Vrms per leg (see A-M3) | Closed
R3-4 | QA403 cannot drive 1.8 V I²S | I²S is now 3.3 V; header, firmware test mode and sequencing specified | Closed
R3-5 | 200 mA “limit” not implemented; thermal at 16 Ω balanced | Clean envelope ≤ 80 mA peak per leg; rated power at 1 % THD+N or calibrated 0 dBFS; overload bounded by the TPS2553 (see A-H5) | Closed
R3 consistency | Rails-good qualification; offset/trim; workbook external links; cost/sourcing reconciliation | Rails-good: LM27762 PGOOD gates AMP_EN in hardware and arms the latch ≈ 60 ms after PGOOD good at v0.5 (v0.6: 25–133 ms, see R5-C6). Offset/trim: as R1-B6 and R2-M3. Workbook links: the delivered v0.1 file references only its own sheets (links appear when sheets are copied into another workbook); v0.2 adds a self-check. Cost/sourcing: single source of truth (Parts List v0.3 at v0.5; now Parts List v0.5), all LCSC | Closed
