ooyang0325/Hi-Res-DAC/doc/DAC_HPA_Design_Spec_v0.8.docx

# USB DAC + Balanced Headphone Amplifier — Design Specification v0.8

Product requirements and architecture for a personal PCB project

Author | Date | Version | Document type
Diego Yang | 24 Sep 2026 | v0.8 (draft for review) | Product requirements + architecture

Companion documents: “Schematic Design Notes v0.7” holds the block-level circuit guidance, and “Parts List v0.6” (DAC_HPA_Parts_List_v0.6.xlsx) is the source of truth for cost. This specification states the requirements and architecture they implement.

# 1. Purpose and scope

This specification defines the requirements and architecture of a single USB-C, bus-powered Hi-Res DAC with one ESS ES9018K2M DAC chip and a balanced headphone amplifier. The outputs are a 3.5 mm unbalanced jack and a 4.4 mm balanced jack, for one headphone at a time.

v0.8 answers the seventh review round (R7-A…R7-E, a full design check in five areas: power, analog, protection, digital, and parts and cost; Appendix C), run before any hardware is bought because development and test boards are hard to get in Taiwan. The architecture stays: CH32V307 + AGRV2K USB bridge with our own USB firmware and CPLD logic, ES9018K2M in differential current mode with one OPA2210 I/V converter per pin, 2 × OPA1622 difference-amplifier legs, LM27762 charge-pump rails and a hardware fault latch. What changed: every enable the latch can pull low now has a series resistor (new R307 on AVCC_EN, which removes the AVCC_EN contention blocker, and R521 on AUD_EN); PGOOD is pulled up to 5V_ANA through 10 kΩ (R505, with R522 into the MCU), so the ≈ 35 µs latch capture is genuine; mandatory firmware start-up rules cover faults present at power-up; the calibrated level drops to 1.55 Vrms per leg because the OPA1622 clean swing ends ≈ 1.3 V from the rail, with new power targets and a 70 mA envelope at 4.4 mm 32 Ω; V+ rises to +3.90 V so that the OPA1612 fallback for the OPA2210 fits its common-mode range; the CPLD is programmed over 2-wire Compact-JTAG, takes its family clock on PIN_1 and no longer receives the 80 MHz clock, which now drives only the DAC MCLK and is enabled by the CPLD (MCLK_EN); the power-down order handles the DAC reset state (MCLK stopped and RESETB kept high until AVCC is off); 3V3D and 1V3 get bleeders; and the suspend budget is ≈ 2.30 mA. Stage 1 becomes optional, and the JLCPCB-built Stage 2 board, now with the ES9018K2M and its real supplies, is the first hardware and the layout gate. The amendment of 24 Sep 2026 (same version) answers three external reviews (R7-F, R7-G, R7-H; Appendix C.2): the hardware DC detector becomes two TI LM339DR quad comparators with one window per leg and no diode-OR (leg trip 0.43–0.67 V; 1 V removed within 125 ms and 2 V within 47 ms, worst case); the slow DC-sense network is redesigned (15 kΩ / 10 kΩ to 3V3A / 22 kΩ + 2.2 µF, with a 3V3A monitor) and four firmware DC tiers act on every leg and on each balanced pair; C421 becomes 33 pF, and the DAC-pin behaviour after an output-stage failure is analysed and, by the owner’s decision of the same day, handled by the fitted DAC-pin clamps D405–D408 (BAT54S), which hold the pins within ≈ −0.40 V…AVCC + 0.40 V and leave a small residual risk; AMP_EN drops adaptively at power-down; a stream DC guard mutes DC in the program material; and the cost is 1,719 NTD per board, 2 NTD under the order gate of 1,721 NTD (the 1,700 NTD ceiling plus the owner-approved 21 NTD for the clamps).

Goal: “best measured performance for the money”, proven by published measurements; not “beats every product”, which a hobby analyzer cannot prove (QuantAsylum itself says its QA403 won’t match a US$30,000 analyzer).

Budget: the target is ≤ 1,500 NTD per board for the 5-board sample run (what the owner actually pays: ≈ 7,500 NTD for five assembled boards at the target, including the bare PCBs and JLCPCB assembly fees); it is not a 100-unit average. Ceiling 1,700 NTD per board, set when the third oscillator was added, plus the owner-approved 21 NTD for the DAC-pin clamps (24 Sep 2026) → order gate 1,721 NTD per board. On 24 Sep 2026 the owner confirmed the budget is flexible as long as it does not surge, and on the same day he decided to fit the DAC-pin clamps D405–D408, knowing that they add ≈ 21 NTD per board and take the estimate over the 1,700 NTD ceiling. The order gate is hard and covers every JLCPCB line of the real quote: PCBs, PCBA fees (including any fixture or other assembly line that appears in the quote) and parts; when the quote is approved, both the gated subtotal and the total payable (gated subtotal + shipping + tax from the quote) are recorded. Shipping, import tax, programmers, enclosure and proof-of-concept hardware are outside the order gate. The sentence “A PCB assembly fixture is needed to protect and support this part during the assembly process” appears on every JLCPCB part page, including unrelated parts (checked on the OPA2209AIDR page) and an empty part-page template, so it is standard page text and not a part-specific requirement for X202 or the OPA2210; no fixture fee is expected for Economic PCBA. The current estimate is 1,719 NTD per board (8,594 NTD for five boards), a conservative planning figure: WARNING (above the 1,500 NTD target) and only 2 NTD under the order gate, so the real JLCPCB quote decides (Section 6). Owner decision of 24 Sep 2026: the residual DC region below 0.2 V per leg (≤ 2.5 mW into 16 Ω, ≤ 1.25 mW into 32 Ω; Section 5.3) is accepted.

Portfolio context is kept in the repository README.

In scope for v1 | Out of scope for v1
USB-C Hi-Res DAC with a single ES9018K2M DAC chip, bus-powered from one USB-C port (data + 5 V) | DSD in v1 (stretch goal: the ES9018K2M supports DSD; depends on firmware)
Balanced headphone amplifier: 4.4 mm balanced jack plus 3.5 mm unbalanced jack (one headphone at a time) | K1000-class 1 W drive (v0.8 gives ≈ 69.7 mW into the K1000 in High mode, Section 5)
PCM 44.1–384 kHz (including 352.8 kHz; all eight rates with exact integer clock ratios), 16–32 bit, USB Audio Class 2.0 High-Speed | USB PD power
USB power modes: Default (≤ 500 mA, hardware-limited) and High (only with a ≥ 1.5 A Type-C advertisement); USB suspend ≤ 2.5 mA within 10 ms of the last bus activity | Fast rail-proximity DC detector (v2 option; a rail-stuck failure in High mode stays within the v1 energy limits)
DC-fault protection: hardware fault latch (DC detect, firmware slow DC tier, PGOOD loss, sustained overcurrent) that disables the amplifiers and turns the headphone rails and the DAC analog supply off | Output relays
Host volume in the DAC’s attenuator; per-unit level calibration at the end-of-line test | Hardware volume knob
Design automation: CI checks, BOM cost gate, DFF/DFA/DFT rules, AI datasheet review, automated measurement and calibration | Enclosure design (3D-printed case for prototypes only)

# 2. Key targets

All values below are proposed targets for v0.8, based on the ES9018K2M, OPA2210, OPA1622, LM27762 and TPS2553 datasheets and the v0.8 design calculations; every board revision is measured against this table (Section 8). Design estimates and assumptions are labelled as such; the protection limits are worst-case values.

Parameter | Target | Minimum | Conditions | How verified
PCM sample rate | 44.1–384 kHz, 16–32 bit: all eight rates (44.1, 48, 88.2, 96, 176.4, 192, 352.8 and 384 kHz) with exact integer clock ratios and a 50:50 bit clock | 384 kHz | USB Audio Class 2.0, High-Speed; DAC bit-clock duty 45:55 to 55:45 (Section 5.3); absolute rate within the oscillator tolerance (X203: ±20 ppm tolerance + ±30 ppm stability), absorbed by the asynchronous USB feedback | Host playback sweep at every rate; all eight rates bit-perfect on the Stage 2 board (layout gate)
DSD | Not in v1 (stretch: the ES9018K2M supports DSD; depends on firmware) | — | — | —
Hosts | Windows 10/11 built-in UAC2 driver, macOS, Linux; Android over USB-C (High-Speed) | — | — | Host playback on each OS
THD+N at 1 kHz | ≤ −105 dB | ≤ −100 dB | Calibrated 0 dBFS, 300 Ω, both jacks, 20 Hz–20 kHz (proposed) | QA403 via Python (Section 8)
Dynamic range | ≥ 115 dB(A) | ≥ 112 dB(A) | Both jacks (estimate ≈ 117.4 dB(A) unbalanced, ≈ 118.6 dB(A) balanced at 1.55 Vrms per leg; correlated I/V noise and the corrected leg-network noise, Section 5.3) | QA403 (results recorded with the analyzer loopback floor)
Level at 0 dBFS | 1.55 Vrms unbalanced / 3.1 Vrms balanced after calibration (± 0.1 dB) | — | Per-unit master trim stored in MCU flash; before calibration −4.5 dB (≤ 1.54 Vrms on the highest-gain unit), a safety setting that keeps an untrimmed unit within the calibrated full scale and the OPA1622 clean swing | Automated end-of-line test (Section 7)
Output power, High mode | 3.5 mm ≥ 50 mW at 32 Ω; 4.4 mm ≥ 105 mW at 60 Ω, ≥ 65 mW at 120 Ω, ≥ 30 mW at 300 Ω (worst unit, both channels) | — | 1 kHz, both channels, worst-case rail; rated at 1 % THD+N or calibrated 0 dBFS, whichever comes first; clean swing ≈ 1.3 V from the rail and a 70 mA envelope at 4.4 mm 32 Ω; estimates in Section 5.2 | QA403 + dummy loads
Output power, Default mode | 3.5 mm ≥ 38 mW at 32 Ω; 4.4 mm ≥ 17 mW at 60 Ω, ≥ 35 mW at 120 Ω, ≥ 30 mW at 300 Ω; 32 Ω balanced not rated (worst unit, both channels) | — | As High mode; rated by the instantaneous peak analog current within the TPS2553 Default minimum (157 mA); estimates in Section 5.2 (3.5 mm 32 Ω: 38.6 mW, small margin) | QA403 + dummy loads
Output impedance | ≤ 0.5 Ω | — | 1 kHz, both jacks, including contacts | Load/no-load method, 32 Ω and 300 Ω
Frequency response | +0.1/−0.3 dB, 20 Hz–20 kHz | — | 44.1, 48 and 384 kHz sample rates; estimate −0.05 dB at 20 kHz | QA403
Crosstalk at 1 kHz | Balanced ≤ −100 dB (300 Ω); unbalanced ≤ −75 dB (32 Ω, at the jack) | — | Layout rule for the shared ground (Section 7) | QA403
Channel balance | ≤ 0.3 dB; per-channel fine trim to ±0.05 dB by MCU digital scaling at calibration | — | — | Automated end-of-line test
DC offset | ≤ ±10 mV unbalanced, ≤ ±20 mV balanced | — | Worst-case estimate 7.7 / 15.4 mV (unbalanced ≈ 4.0 mV RSS), including ≤ 0.7 / 1.4 mV leakage of the DAC-pin clamps D405–D408; ≤ 9.3 / 18.6 mV if the DAC null is 1.65 V (R433 option, Section 5.3); 9.7 / 19.4 mV with the OPA1612 fallback (at the edge); 100 % screening | Automated test on every board with a DC-capable DMM
Protection | Hardware detector, worst case: a DC fault ≥ 2 V on any leg is removed within 100 ms and ≥ 1 V within 250 ms; firmware tiers (same latch, per leg and per balanced pair): ≥ 1.0 V within 0.25 s, ≥ 0.5 V within 0.35 s, ≥ 0.3 V within 1.1 s, ≥ 0.2 V within 3 s; every sub-hardware-trip case ≤ 30 mJ at 16 Ω and ≤ 15 mJ at 32 Ω; terminal energy ≤ 30 mJ at 16 Ω and ≤ 15 mJ at 32 Ω for a rail-stuck failure in High mode, worst case, including the after-trip energy (≤ 0.6 mJ); starts latched at power-up; residual below the last tier (≤ 0.198 V across a driver): accepted by the owner on 24 Sep 2026 | — | Defined at the headphone terminals; removed = RAIL_EN, AMP_EN and AVCC_EN pulled low; worst case 2 V → 47 ms, 1 V → 125 ms (two LM339 windows per leg, leg trip 0.43–0.67 V, τ 84–111 ms); rail-stuck energy 21.4 / 11.0 mJ worst case; no false trip for full-scale content above 9.5 Hz (hardware, worst case) and 4.7–9.3 Hz (firmware tiers); balanced digital DC is limited by the stream DC guard; firmware start-up rules for faults present at power-up (Section 5.3) | Digital DC test signal, firmware-tier test, detector test, failed-output emulation with dummy loads (worst-case envelope, no allowance), open-drain short-PGOOD-pulse test, balanced opposite-sign DC test, stream-guard test, DAC-pin probing and SPICE of a failed output stage (Section 7)

Pop

≤ 5 mV peak for controlled transitions, at risk until measured (the DAC reset state gives ≈ 18–35 mV at AVCC-on); ≤ 20 mV peak at unplug or brownout (target)

—

Pop = peak of the transient at the jack beyond the settled DC step, band-limited 20 Hz–20 kHz (AC-coupled analyzer input); the DC before and after each transition is bounded separately by the offset limits (±10 / ±20 mV). Controlled: power-on after configuration, suspend/resume, rate and rate-family change, fault recovery; 32 Ω and 300 Ω; the AVCC-on step with RESETB low is measured on the first boards, and power-up order A (legs first), A′ (AUD_EN with AVCC_EN) or B (DAC first) is chosen by the pop measured on main board 1; power-down pop at 300 Ω ≈ 4.5 mV typical, ≈ 12.7 mV at the worst-case discharge (measured; Section 5.3)

Oscilloscope with an AC-coupled, band-limited analyzer input
USB power and inrush | Before configuration ≤ 100 mA (estimate ≤ 83 mA); Default mode ≤ 500 mA, estimated maximum 0.475 A with hardware-limited analog current; High mode only with a ≥ 1.5 A Type-C advertisement (estimated maximum 0.760 A); attach charge ≤ 50 µC (estimate ≈ 43 µC: 42.5 µC at 5.0 V, 43.8 µC at 5.25 V) | — | Bus-powered descriptors (bmAttributes 0x80, bMaxPower 0xFA); the TPS2553 limits only the analog branch, the MCU, CPLD and DAC-core currents are estimates or datasheet values; attach charge at nominal capacitance, domains staggered and soft-started | Measured on the Stage 2 board before layout (gate) and on every main board: USB power meter in every state; Type-C 1.5 A source and USB-A port; charge at attach and VBUS droop at each domain enable
USB suspend | ≤ 2.5 mA within 10 ms of the last bus activity (v1 requirement) | — | Controlled power-down: MCLK stopped and AVCC off first, AMP_EN when the 3V3A monitor reads < 0.1 V, the rails last; suspend level typically ≈ 8.2 ms and at worst 9.3 ms after the last bus activity; budget ≈ 2.30 mA (margin 0.20 mA, LEDs off), of which the MCU Stop current with the USBHS PHY suspended (≤ 1.9 mA) is an assumption and a Stage 2 gate | Current vs time from the last bus activity, on the Stage 2 board (layout gate) and on every main board
Thermal | All parts within ratings; the board recovers | — | Overload tests, 30 min each, High mode, maximum volume (Section 7); regulator dissipation table (Section 5.3): U504 0.20 W at 5.25 V with the input dropper, LM27762 0.39 W at 5.25 V (≈ +24 °C) | Thermocouple / IR camera, including the regulators at bring-up
PCB | 4 layers, target ≤ 80 × 60 mm, all SMT parts on the top side except the 4.4 mm jack, 90 Ω USB pair | — | JLCPCB Economic PCBA | ERC/DRC and layout-rule checks in CI (Section 8)

Cost

≤ 1,500 NTD per board for the 5-board run (target); ceiling 1,700 NTD per board plus the owner-approved 21 NTD for the DAC-pin clamps (24 Sep 2026) → order gate 1,721 NTD per board, the hard gate, with the owner statement of 24 Sep 2026 (estimate 1,719 NTD: WARNING, 2 NTD under the order gate)

—

Every JLCPCB line of the real quote: PCBs, PCBA fees (including any fixture or other assembly line) and parts; excluding shipping, import tax, programmers, enclosure and proof-of-concept hardware; sensitivities: OPA1612 fallback ≈ 1,725 NTD (LCSC price, US$1.0942) to ≈ 1,740 NTD (JLCPCB price, US$1.33), above the order gate (owner decision only if the OPA2210 cannot be bought), OPA2210 at the LCSC price ≈ 1,825 NTD (then the fallback is used), LM339BIDR instead of LM339DR ≈ 1,715 NTD, JLCPCB-vs-LCSC price differences ≈ −24 NTD (indicative), lower-fee case ≈ 1,621 NTD; the margin is small and the real JLCPCB quote decides

Cost gate: WARN > 1,500, FAIL > 1,721 (Section 8); the JLCPCB quote from the real BOM/CPL files must pass before ordering; gated subtotal and total payable recorded at quote approval

# 3. Architecture

## 3.1 Signal and control path

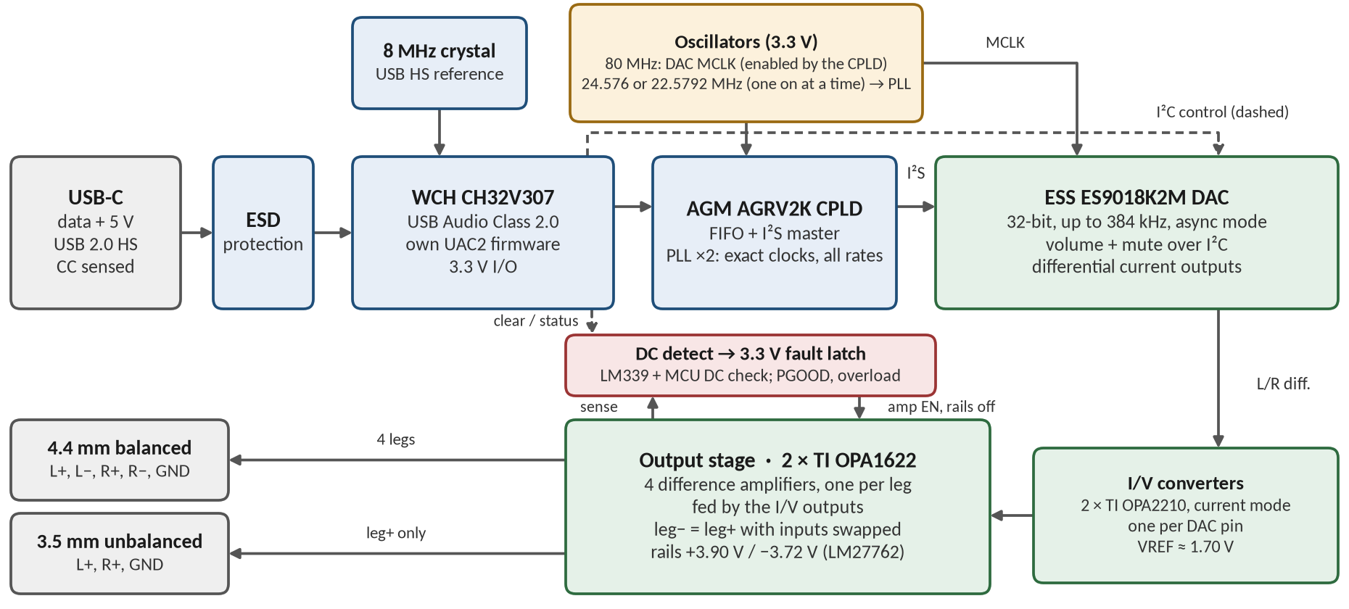
[picture p4: figure]
Block diagram of the signal and control path. A single USB-C port (data and 5 V, USB 2.0 High-Speed, CC lines sensed) passes through ESD protection to the WCH CH32V307 MCU, which runs our own USB Audio Class 2.0 firmware with an 8 MHz crystal as the USB High-Speed reference. The MCU feeds the AGM 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

Figure 1. Signal and control path (80 MHz oscillator for the DAC MCLK only, enabled by the CPLD (MCLK_EN); 24.576 MHz and 22.5792 MHz family oscillators, one at a time, into the CPLD PLL; OPA2210 I/V converters; +3.90 V / −3.72 V output legs; the two LM339 window comparators (DC detect), the MCU slow DC check, PGOOD and overload into the fault latch).

- The single USB-C port carries USB 2.0 High-Speed audio and the 5 V bus. D+, D− and VBUS pass through a USBLC6-2SC6 ESD array. CC1 and CC2 keep their 5.1 kΩ Rd pull-downs and also go through 10 kΩ to MCU ADC inputs, which read the Type-C current advertisement (Section 3.2). A6/B6 (D+) and A7/B7 (D−) are tied at the connector (checked against the drawing and a sample before layout), and the shell is tied to GND through R107 0 Ω (C101 DNF).
- USB bridge: a WCH CH32V307RCT6 RISC-V MCU with a built-in USB 2.0 High-Speed PHY runs our own USB Audio Class 2.0 firmware, built on WCH’s register-level high-speed USB device examples; the CPLD logic is ours as well. The open-source USBAudioToI2S project (Apache-2.0; MCU + CPLD asynchronous USB audio) is kept only as a known-good comparison on the same hardware. v1 depends on a pre-layout firmware gate on the Stage 2 board, the first hardware (Section 8; the Stage 1 desk setup is optional). The MCU pin map (40 of 51 GPIO, including optional ones) is proposed in Schematic Design Notes v0.7 and frozen before the Stage 2 board. The 8 MHz HSE crystal is confirmed (the firmware derives the 4 MHz USB HS PLL reference as HSE ÷ 2); the Basic 5.0 × 3.2 mm YXC X50328MSB2GI is used with 33 pF load capacitors.
- Clock: three 3.3 V oscillators on 3V3D. X201, 80 MHz (SCTF SX3M80.000B20F30TNN; ±20 ppm tolerance, ±30 ppm stability), drives only the DAC MCLK (XI) through 33 Ω; the CPLD no longer receives it (R209 deleted), so its load is ≈ 10 pF plus the trace (XI trace ≤ 20 mm, duty measured at XI). Its tri-state pin 1 is driven by MCLK_EN from CPLD pin 21 with the R218 2.2 kΩ pull-down, so X201 is off by default and during CPLD configuration; the MCU sets MCLK_EN over SPI only after DVDD is up and clears it before AVCC is switched off (Section 5.3). It replaces the 100 MHz part, which sat at the ES9018K2M limit (MCLK cycle time ≥ 10 ns, pulse width high and low ≥ 4.5 ns, duty 45:55 to 55:45; datasheet “XI / MCLK Timing”). At 80 MHz the cycle is 12.5 ns and the pulse width ≥ 5.6 ns at 45:55, and 80 MHz ≈ 208 × 384 kHz (208.3; asynchronous mode needs no integer ratio), above the 192 × FSR minimum for PCM normal (asynchronous) mode (73.7 MHz at 384 kHz). The ES9018K2M runs in that mode, the one its datasheet performance is specified in; the external 1.3 V DVDD is still required (FSR > 192 kHz).
- An AGM AGRV2KQ32 CPLD makes BCLK = 64 × fs and LRCLK, and changes SDATA and LRCLK on the falling BCLK edge (≥ 20 ns half period at 24.576 MHz BCLK against the DAC’s 4.1 ns setup and 2 ns hold). X202, 24.576 MHz (YXC OT322524.576MJBA4SL), for the 48 kHz family and X203, 22.5792 MHz (SCTF SX2M22.5792M20F30TNN), for the 44.1 kHz family share one node at the CPLD’s only dedicated clock pin, PIN_1 (IO_GB), which feeds the PLL, each through its own 33 Ω source termination (R210, R211). Both are off by default: R212 and R213 are 2.2 kΩ pull-downs on OSC48_EN and OSC44_EN, so neither oscillator is enabled at power-up, during CPLD configuration or reprogramming, or whenever the CPLD pins are high-impedance, and R214 (10 kΩ) holds the shared node low while both are off. Only one family oscillator drives the node at a time (a disabled output-enable oscillator may keep running internally; both are counted in the current budget). The CPLD’s single PLL doubles it to 49.152 MHz or 45.1584 MHz, divided by 2/4/8/16 for 384/192/96/48 kHz or 352.8/176.4/88.2/44.1 kHz: all eight rates have exact integer clock ratios, and the PLL ×2 also turns the oscillators’ 45–55 % duty into a 50:50 bit clock (Section 5.3). There is no PLL in the DAC MCLK path. The CPLD has no free-running system clock: its global clocks are the PLL output and the SPI clock (SCK, routed to the global network through ALTCLKCTRL, as in the USBAudioToI2S reference). It is programmed over AGM’s 2-wire Compact-JTAG (JTMS pin 24, JTCK pin 25) from the Supra tool with a J-Link or an AGM DAP-Link through J202 (3V3D sense only, JTCK, JTMS, NRST, GND); a generic CMSIS-DAP probe such as the WCH-LinkE in DAP mode is not confirmed. For first-time and end-of-line programming, a PROG pad (TP732) makes the firmware power 3V3D without USB configuration (Section 7).
- Rate-family change, break-before-make, sequenced by the MCU through CPLD SPI registers, with the two enables mutually exclusive in the CPLD logic and never high in the same cycle: (1) DAC soft mute; (2) I²S output stopped (held low); (3) PLL held in reset; (4) old enable low; (5) wait ≥ 1 ms with both off; (6) new enable high; (7) wait ≥ 10 ms (start-up ≤ 3 ms X202, ≤ 5 ms X203); (8) PLL released, wait for lock; (9) output restarts, and the MCU checks the LRCLK rate with its feedback timer (within ±0.1 % of the target; otherwise it stays muted, retries once, then reports a fault); (10) DAC re-locks (lock_status, register 64) → soft unmute. After configuration the CPLD starts with both enables low and the PLL in reset, and the MCU enables X202 through SPI after ≥ 1 ms. A family change never touches MCLK (X201), and both enable bits never change at the same time. The single PLL must lock at both 22.5792 and 24.576 MHz input (the AGM lock range is not published): a Stage 2 gate, with BCLK taken directly from X202/X203 as the fallback (duty 45–55 %, the DAC limit, zero margin).
- Oscillator datasheets: the SCTF 2CM series datasheet (X203) gives pin 1 “Tri-State”, enabled when OE is logic 1 or open and disabled at logic 0 (≤ 0.3 VDD), start-up ≤ 5 ms, 10 mA max and duty 45–55 %, but no disable or enable time, internal pull-up value or disabled-output leakage; the YXC YSO110TR datasheet (X202) gives enable ≥ 70 % VDD or floating, disable ≤ 30 % VDD, start-up ≤ 3 ms, 5 mA max and duty 45–55 %, but no disable time. Both enable when pin 1 is open, so each has an internal pull-up of unknown strength: the 2.2 kΩ pull-downs keep pin 1 below 0.3 VDD against any combined pull-up ≥ 5.1 kΩ (oscillator and CPLD weak pull-up during configuration), and each enable draws 1.5 mA when driven high. Typical disable times are well under 1 µs, so the 1 ms gap is a large margin; the disable time is measured on the Stage 2 boards. Fallback: the DNF 2:1 multiplexer U205 (74LVC1G157GW, select = OSC44_EN) with R215 33 Ω at the PLL pin and the DNF R216, R217 10 kΩ pull-downs on both mux inputs; to use it, fit U205, R215, R216 and R217 and remove R210 and R211 (with R210/R211 removed, a disabled oscillator output is high-impedance, so a mux input would otherwise float). One of the two Stage 2 boards is built with it.
- MCU → CPLD audio link: SPI with chip-select framing (MCU SPI1 master with DMA at 36 MHz, 72 MHz ÷ 2, the only workable setting: 68 % utilised at 384 kHz; register reads at ≤ 18 MHz; one CS frame per block of samples). LINK_FRAME is active-high (idle low), CPOL = 0, and R224/R225 33 Ω sit at the MCU on SCK and MOSI; SCK, MOSI, FRAME and RESETB are driven low or set as inputs whenever AUD_EN is low. The CPLD writes the FIFO directly in the SPI clock domain (SCK on the global network through ALTCLKCTRL) and reads it in the PLL bit-clock domain, with Gray-coded pointers (1024 × 32 bit in 4 × M9K, ≈ 1.33 ms at 384 kHz); each SPI frame starts with a 16-bit header so that the pointer synchronisers see SCK edges, the control registers live in the SPI domain, and MISO returns the FIFO level during the frame. I²S is not used for the link, because its frame rate is not locked to the audio rate. The payload at 384 kHz / 32-bit stereo is 24.576 Mbit/s; a second SPI lane (SPI2, PB12–PB15, two spare CPLD pins) is reserved, and the 36 MHz capture is a Stage 2 gate.
- The ESS ES9018K2M (32-bit, PCM to 384 kHz via I²S) is configured by the MCU over I²C (7-bit address 0x48, written 0x90; ADDR to DGND through R306) and runs in differential current mode. Each output pin is equivalent to a voltage source (3.05 Vpp around 1.65 V) in series with 806 Ω ±11 % (datasheet p. 31), and ESS specifies DNR and THD+N only in differential current mode, so the design follows the ESS application circuit (p. 27) with one I/V converter per pin. The MCU drives RESETB (100 kΩ pull-down) through the new R308 1 kΩ, which limits injection to < 3 mA, and reads the DPLL lock status (register 64, and GPIO2 as DAC_LOCK). In reset the DAC outputs are driven to ground (datasheet pin table), which the power sequence takes into account (Section 3.2).
- Signal chain: DAC (current mode) → 2 × OPA2210 I/V converters (one amplifier per DAC pin, VREF ≈ 1.70 V) → 2 × OPA1622 difference-amplifier legs → jacks, all on +3.90 V / −3.72 V. U403 serves DACL/DACLB and U404 DACR/DACRB. Each feedback is 836 Ω (1 kΩ ∥ 5.1 kΩ, 1 %) with 10 Ω + 660 pF (two 330 pF C0G in parallel), a 288 kHz pole. VREF = 1.703 V = 0.516 × 3V3A from a 15 kΩ over 15 kΩ + 1 kΩ divider (7.74 kΩ source) with C421 33 pF C0G only (τ ≈ 0.29 µs with ≈ 5 pF stray), so VREF tracks AVCC in every ramp; its in-band noise is unchanged (common mode, far below the 620 kHz pole). The DAC-pin clamps D405–D408 (JSMSEMI BAT54S, C916425, SOT-23, one per DAC pin) are fitted (owner decision, 24 Sep 2026): pin 3 (common) to the DAC pin (DACL and DACLB with AVCC_L, DACR and DACRB with AVCC_R), pin 1 (lower anode) to AGND at the DAC’s AGND pins and pin 2 (upper cathode) to AVCC_L/AVCC_R at their decoupling capacitors, within 5 mm of the DAC pins (pinout confirmed on the JSMSEMI drawing before layout). In normal operation both diodes are reverse biased by ≈ 1.6–1.7 V, and they never conduct in controlled transitions (VREF tracks AVCC), at unplug (VREF lag ≤ 15 mV with C421 33 pF) or during the DAC-reset step (the pins stay between 0 V and VREF). Their net leakage, ≤ 0.4 µA per pin (assumption: the two diodes of a package see almost equal reverse voltage, so their leakages largely cancel), adds ≤ 0.35 mV offset per pin, and their ≤ 20 pF per DAC-pin node raises the I/V high-frequency noise gain only to 1 + 20 pF/660 pF ≈ 1.03, negligible for stability and noise (included in the OPA2210 stability SPICE). VREF sits at the DAC’s zero-DC-current point from the current-output formula (2.112 mA − 1000·Vg/806 = 0 at Vg ≈ 1.702 V); the ESS voltage-source model gives 1.65 V (AVCC/2), and R433 1 kΩ → 0 Ω sets VREF = 1.650 V if the null test at bring-up shows that value (Section 5.3). The OPA2210 (single input pair, common-mode range (V−) + 1.5 V to (V+) − 1.5 V, Vos ±35 µV max, 2.2 nV/√Hz, 18 MHz) replaces the OPA2197, whose input-pair transition region, typically (V+) − 3 V to (V+) − 1.5 V (TI SBOS737C), contains VREF; VREF (≤ 1.754 V worst case) sits ≈ 0.53 V inside the common-mode range at the minimum +rail of 3.789 V. Its output swing at the ≈ 3 mA I/V load is estimated at (V+) − 0.3 V (≈ 3.49 V at the minimum rail), above the I/V output peak at the calibrated level. The OPA2210’s JLCPCB stock is unverified, so the OPA1612AIDR (same dual pinout, common-mode limit (V+) − 2 V) is designed in as the fallback: V+ = +3.90 V keeps the worst-case VREF (≤ 1.754 V, tracking 3V3A +2 %) ≥ 35 mV inside its range at the minimum rail. With the fallback the quiescent current rises to up to 4.5 mA per channel (instead of 2.5 mA), an analog quiescent current of ≈ 72 mA, so the Default-mode targets are not met: 3.5 mm 32 Ω ≈ 27 mW (target ≥ 38 mW), 3.5 mm 16 Ω ≈ 14 mW, 4.4 mm 60 Ω ≈ 13 mW (target ≥ 17 mW) and 4.4 mm 120 Ω ≈ 26 mW (target ≥ 35 mW); High mode is unchanged; the worst-case offset becomes 9.7 / 19.4 mV (inside the limits, at the edge) and the I/V noise is lower (1.1 nV/√Hz).
- Output stage: 2 × TI OPA1622, one amplifier per leg, with no paralleling. Each amplifier is a 4-resistor 2.00 kΩ (0.1 %) difference amplifier with 330 pF C0G (a 241 kHz pole), fed by the I/V outputs: leg+ = I/V(DAC−) − I/V(DAC+), leg− = the swap. The leg input common mode is VREF, so VREF errors are mostly common mode. U401 drives L+ and L−, U402 drives R+ and R−. The clean output envelope is ≤ 80 mA peak per leg (70 mA at 4.4 mm 32 Ω, set by the negative-rail headroom) within the OPA1622 clean swing, which ends ≈ 1.3 V from the rail (Section 5). Each OPA1622 GND pin (pin 3, the EN reference) is tied to GND.
- Protection: two TI LM339DR quad comparators (U601, U602) form one window per leg directly on its filter node, with no diode-OR, so the threshold depends only on the divider, the comparator offset and its bias current, all datasheet-guaranteed (worst-case leg trip 0.43–0.67 V, τ 84–111 ms); their eight open-collector outputs are wired-OR into node F and set an N-MOSFET fault latch on the always-on 3V3M domain; PGOOD-bad (Q610) and a sustained TPS2553 overcurrent (FAULT through D606 and R638, after its 5–10 ms deglitch) set it too. C605 sits on node F, so the latch captures a PGOOD fault in ≈ 35 µs (budget 0.1 ms; RAILS_OK_N crosses 2.5 V in ≈ 1.0–1.3 µs through R505 10 kΩ to 5V_ANA and carries only ≥ 1 MΩ RC branches and high-impedance inputs), every set request is stretched to 1.5–7.7 ms, and the board powers up latched. The latch pulls RAIL_EN (LM27762 EN+/EN−), AMP_EN (both OPA1622 EN pins) and, through Q611, AVCC_EN (LP5907) low, each against a 10 kΩ series resistor from the MCU (R507, R618, R307), and stays set until the firmware clears it (FLT_CLR). Q609 is a slow static interlock (on 1.9–9.4 ms after PGOOD goes bad) that keeps AMP_EN low whenever the rails are off, so a short PGOOD glitch either latches or does nothing. Four firmware DC tiers read every leg through its own low-impedance DC-sense network (15 kΩ / 10 kΩ to 3V3A / 22 kΩ + 2.2 µF) on an MCU ADC pin, act on each leg and on each balanced pair difference (≥ 1.0 V within 0.25 s, ≥ 0.5 V within 0.35 s, ≥ 0.3 V within 1.1 s, ≥ 0.2 V within 3 s) and set the same latch through ANA_FAULT and D606; a stream DC guard in the MCU mutes DC in the program material before the DAC instead of latching; at the FLT interrupt the firmware first drives the enables low, then stores the leg readings and the fault flags, which identify the cause. The set path is armed 51–186 ms after PGOOD goes good, without clearing the latch; mandatory firmware start-up rules cover faults present at power-up; there are no relays (Section 5.3).
- The 4.4 mm balanced jack carries L+, L−, R+, R− and GND; the 3.5 mm unbalanced jack carries L+, R+ and GND. Both jacks are live, so only one headphone is connected at a time.

## 3.2 Power path

- The single USB-C port supplies data and 5 V; the board is bus-powered (bmAttributes 0x80, bMaxPower 0xFA = 500 mA). Only 5 × 1 µF sit on VBUS before any switch (connector and the inputs of ME6211 #1, ME6211 #2, LP5907 and TPS2553). At attach only 3V3M starts (5.3 µF behind it, including C212, C221, C605, C606 and C607; C607 is now 10 nF and C221 1 µF is added), so the attach charge is ≈ 42.5 µC at 5.0 V and 43.8 µC at 5.25 V against the 50 µC USB-IF limit (nominal values; DC-bias derating lowers the real figure). VBUS has ceramic capacitors only, and the LP5907 and LM27762 are rated 6.0 V and 5.8 V absolute maximum: a DNF footprint D102 (unidirectional TVS at J101, VRWM 6.0 V, for example MDD SMF6.0A, LCSC C123790) is fitted only if the hot-plug test on board 1 shows a VBUS peak above 5.8 V, after its leakage at 5.25 V has been measured (parts with a 5.0 V VRWM leak hundreds of µA at 5 V).
- 3V3M, always on: ME6211C33 #1 (U502) powers the MCU (including the DC-sense ADC, whose networks are biased from 3V3A), the fault latch and the LEDs (both off in suspend). Before USB configuration only this domain runs (62 / 83 mA typical / maximum estimate; assumption on the MCU current).
- 3V3D, switched: ME6211C33 #2 (U504, CE = AUD_EN through the new R521 10 kΩ, which keeps the CE clamp current ≤ 0.2 mA when CE would exceed VIN + 0.3 V at unplug under load) is fed through R519 + R520 (2 × 2.2 Ω 0805 in series, 4.4 Ω), which move ≈ 0.11 W out of the LDO (U504 0.20 W at VBUS 5.25 V and 0.24 W at 5.5 V against the ME6211’s 300 mW SOT-23 rating, at 160 mA including the bleeders; LDO input ≥ 3.70 V at VBUS 4.40 V), and C512 10 µF is its bulk capacitor. It powers the CPLD (through the new FB202 ferrite branch, with C220 1 µF at VDDA33), the three oscillators (80 MHz, 24.576 MHz and 22.5792 MHz), the I²C pull-ups and the DAC DVCC (through the GZ1608D601TF ferrite, ≈ 14 mA). A fixed, ceramic-stable 1.3 V LDO (ME6216A13M3G, SOT23-3, ±1 %, 250 mA) fed from 3V3D makes the external DVDD, so DVDD cannot exceed DVCC during the ramps. New bleeders discharge both after AUD_EN goes low: R524 2.2 kΩ on 3V3D (1.5 mA; 3V3D below 0.3 V ≈ 70 ms after AUD_EN low) and R525 1 kΩ on 1V3 (1.3 mA, so DVDD collapses before DVCC); the firmware keeps AUD_EN off for ≥ 100 ms before re-enabling it.
- 3V3A, switched: the LP5907-3.3 (EN = AVCC_EN from the MCU through the new R307 10 kΩ, also pulled low by the latch through Q611, which now pulls the node low against 0.33 mA instead of fighting the GPIO) supplies VCCA, AVCC_L/AVCC_R, the VREF divider, the DC-sense bias (R628–R631, 0.70 mA) and the 3V3A monitor (R639/R640 10 kΩ/10 kΩ with C616 100 nF to MCU PC4, 0.17 mA). VREF = 0.516 × 3V3A with only C421 33 pF (τ ≈ 0.29 µs with ≈ 5 pF stray), so VREF follows AVCC: the lag is ≤ 4 mV in controlled ramps (3V3A falls through the LP5907’s 230 Ω typical output auto-discharge: below 0.3 V within 5.5 ms worst case, with +50 % discharge resistance and 6.7 µF) and ≤ 15 mV at the fastest unplug slope (0.1 V/µs), so a DAC pin can exceed AVCC only while AVCC is below ≈ 31 mV. D401 and C422 are removed.
- Headphone rails: a TI TPS2553 current-limited switch (EN = ANA_EN; built-in soft start; FAULT open drain with a 5/7.5/10 ms deglitch) feeds 5V_ANA through the Murata BLM18PG121SN1D ferrite (2 A, 50 mΩ) to the LM27762, which makes +3.900 V (3.789–4.014 V) and −3.722 V (3.618–3.828 V magnitude), both ranges including VFB and the 1 % divider resistors, with 225 kΩ/100 kΩ and 205.1 kΩ/100 kΩ feedback. Each top resistor is built from Basic values: 100 kΩ + 100 kΩ + 15 kΩ + 10 kΩ (the new R523), and 100 kΩ + 100 kΩ + 5.1 kΩ (R518). V+ is set this high so that the OPA1612AIDR fallback for the I/V converters keeps VREF inside its common-mode range (Section 3.1). EN = RAIL_EN (≥ 10 ms after ANA_EN); PGOOD (95 % thresholds +3.71 V / −3.54 V) is pulled up to 5V_ANA through R505 10 kΩ (the LM27762 VIN side, as TI specifies; no PGOOD current in suspend) and goes, as RAILS_OK_N, to the MCU through R522 10 kΩ, to the fault latch (Q610) and to the Q609 interlock (R623 1 MΩ, C607 10 nF). LM27762 dissipation is 0.39 W at 5.25 V (θJA 62.2 °C/W, ≈ +24 °C) and 0.46 W at 5.5 V.
- Current limit: RILIM = 100 kΩ + 47 kΩ = 147 kΩ gives the Default limit (157 / 183 / 213 mA minimum / nominal / maximum, including 1 % resistors); a 2N7002 switches 100 kΩ in parallel for High mode (59.5 kΩ: 393 / 442 / 498 mA). The TPS2553 acts on the instantaneous current (short-circuit response ≈ 2 µs, then constant-current limiting) and limits only the analog branch, so the board figures are estimated maxima with hardware-limited analog current: 0.475 A in Default mode (25 mA below 0.5 A) and 0.760 A in High mode. High mode is used only when the Type-C advertisement read on CC1/CC2 is ≥ 1.5 A (bands: Default 0.25–0.61 V, 1.5 A 0.70–1.16 V, 3.0 A 1.31–2.04 V). A USB-A-to-C cable reads as Default, and many phones limit OTG to ≤ 500 mA and run in Default mode.
- CC monitoring (firmware requirement): while configured, the MCU samples CC1/CC2 (ADC2) at least every 5 ms, with firmware thresholds of 0.66 V (Default ↔ 1.5 A) and 1.23 V (1.5 A ↔ 3.0 A) with hysteresis on the CC pin that sees Rp, and treats a change as valid after tRpValueChange (10–20 ms). On a drop from ≥ 1.5 A to Default it soft-mutes, sets ILIM_HI low and continues in Default mode within tSinkAdj (60 ms max) of the change; it switches up to High only after the new advertisement is stable (USB Type-C timing, as quoted in the Zephyr USB-C stack and the Chromium EC documentation).
- Supply headroom, computed with the peak currents and a 0.3 Ω cable-and-connector resistance at the real total current (host VBUS 4.75 V), with the TPS2553 (135 mΩ max), the ferrite (60 mΩ) and traces (20 mΩ) in the path and a 3.0 Ω or 3.5 Ω charge-pump resistance (assumption; 2.5 Ω is specified only at 5.5 V): at the worst clean load (4.4 mm 32 Ω, High mode) the negative-rail capability exceeds the maximum |V−| of 3.828 V by +0.13 V (3.0 Ω) / +0.05 V (3.5 Ω) at 70 mA per leg; at 80 mA it would be +0.04 / −0.05 V, hence the 70 mA envelope for this load. 3.5 mm 16 Ω at 80 mA keeps +0.13 / +0.03 V, and at a host VBUS of 5.0 V every case keeps ≥ +0.20 V. On the positive side the LM27762 VIN is ≈ 4.50 V against a maximum V+ of 4.01 V. The negative-rail headroom is measured at VBUS 4.60 V and 4.40 V at bring-up.
- VBUS sense: 100 kΩ / 47 kΩ into ADC1 (5.0 V → 1.60 V), converting continuously on this single channel (VBUS_SENSE, PA1) with the analog watchdog at 4.10 V nominal (3.95–4.25 V with the ADC reference 3V3M ±2 %, the divider ±1.4 % and the ADC error: ≥ 0.15 V below the 4.40 V stress corner and ≥ 0.35 V below the 4.60 V design corner). Sampling is 7.5 cycles at fADC = 72 MHz ÷ 6 = 12 MHz (PCLK2 must be 72 MHz; 18 MHz would exceed the 14 MHz limit): 1.67 µs per conversion and ≈ 3.8 µs worst-case latency, with the ISR on a fast (VTF) vector; ADC2 scans seven channels: CC1, CC2, the four DC-sense channels and the 3V3A monitor (PC4). On unplug or brownout the ISR drops AMP_EN and RAIL_EN at once (target < 5 µs), then RESETB, AUD_EN, AVCC_EN and ANA_EN; the PGOOD latch is the backstop. At 0.47 A with ≈ 4.5 µF on VBUS, VBUS falls at up to ≈ 0.1 V/µs: 4.10 V → 3.46 V (3.3 V LDO dropout) in ≈ 6 µs, so the DAC-first order is impossible at unplug; PGOOD goes bad at VBUS ≈ 3.70 V while 5V_ANA is still ≈ 3.6 V, so Q610 turns on and the latch sets. At full load the logic rails may droop before the sequence completes, so the unplug pop stays a measured target (≤ 20 mV peak), and the watchdog-to-GPIO latency is measured on the Stage 2 board. At a sudden unplug VREF tracks AVCC within ≤ 15 mV (C421 33 pF), so a DAC pin can exceed AVCC only while AVCC is below ≈ 31 mV. ESS specifies only GND < Vout < AVCC, with no margin and no injection rating, so no junction-conduction argument is used: the excursion is measured on the four DAC pins (at the R423–R426 DAC-side pads, against AVCC_L/AVCC_R) at hot unplug under full load, where they must stay within −0.4 V…AVCC + 0.4 V (the clamps D405–D408 do not conduct at unplug).
- Power sequence (steps in Section 5.3): power-up enables the legs while AVCC is still off (VREF = 0 V), then AVCC_EN, so VREF rises in common mode while the legs hold the jack at ≈ 0 V; MCLK starts only after DVDD is up. Because the ES9018K2M drives its outputs to ground while RESETB is low, the AVCC-on step leaves ≈ 18–35 mV at the leg until RESETB is released and the ESS soft start ramps it out; this is measured on the first boards, and firmware options A′ (AUD_EN together with AVCC_EN, allowed by ESS: DVCC with or after VCCA) and B (DAC first, legs last) are kept, chosen by the pop measured on main board 1. Controlled power-down, including USB suspend: at t0 (the suspend interrupt, 3 ms after the last bus activity, or a host or fault command) soft mute; at t0 + 0.1 ms MCLK_EN low (MCLK stops, RESETB stays high, DAC muted) and AVCC_EN low, so the DAC turns off first while the I/V converters and legs stay powered and hold ≈ 0 V; 3V3A falls and VREF and the DC-sense bias follow. AMP_EN goes low as soon as the 3V3A monitor reads < 0.1 V (typically t0 + 4.7 ms), at the latest at t0 + 5.8 ms (worst-case discharge, 3V3A ≈ 0.28 V); then RESETB, AUD_EN, RAIL_EN and ANA_EN go low (the rails decay on their own, and nothing is left that could back-power the I/V stage) and the MCU enters low-power mode with both LEDs off, so the VBUS current reaches the suspend level typically ≈ 8.2 ms and at worst 9.3 ms after the last bus activity (USB limit 10 ms). The power-down pop at 300 Ω, including the sense-bias path, is ≈ 4.5 mV typical and ≈ 12.7 mV at the worst-case discharge (measured; target ≤ 5 mV). Resume to audio takes ≈ 1.0 s (0.6 s blanking charge, the rails, 250 ms, DAC init and the 105 ms soft start). No “rails off, DAC powered” window remains in a controlled sequence; the latch sets as the rails go off, which the firmware expects and masks.
- Fault shutdown: when the latch sets, Q607, Q608 and Q611 pull RAIL_EN, AMP_EN and AVCC_EN low within ≈ 35 µs, each against its 10 kΩ series resistor. Within ≤ 50 µs the FLT interrupt drives AMP_EN, RAIL_EN and AVCC_EN low as well (mirroring the latch), then AUD_EN and RESETB (which stops MCLK back-powering VCCA through XI and any RESETB injection), captures the cause and finally sets ANA_EN low; the IWDG is enabled, and an MCU reset floats all outputs so that the pull-downs switch every domain off. 3V3A needs 3.2–5.6 ms to fall below 0.3 V. In a failed-output shutdown (a stuck leg into 16 or 32 Ω, rail capacitance ±10 %, LP5907 discharge typical and +50 %) the OPA2210 positive common-mode limit (V+ − 1.5 V) drops below VREF 0.11–0.39 ms after the kill, so the I/V converters may not hold the DAC pins for up to ≈ 5.5 ms: a pin sits between the DAC’s internal source (806 Ω) and the I/V output (836 Ω). Unclamped it would be pulled toward −1.76 V, stopped only by the DAC’s internal protection conducting at ≈ −0.6 V with ≤ 3.9 mA, or to ≈ 0.33 V above AVCC for a negative-stuck leg; the fitted clamps D405–D408 hold every DAC pin within ≈ −0.40 V…AVCC + 0.40 V (BAT54 VF ≤ 400 mV at 10 mA; ≤ 4.4 mA per pin) for this window. ESS specifies only GND < Vout < AVCC, with no margin, so a small residual risk remains: up to 0.4 V beyond the rails for ≤ 5.5 ms, and only after an output stage has already failed; it is measured on main board 1 (Section 7). The upper diodes can briefly back-feed 3V3A from the collapsing I/V rails (≤ 4.4 mA per pin, for about the I/V rail decay, ≈ 1 ms with a stuck load); the 3V3A decay is measured with the clamps fitted. Normal operation and every controlled transition keep the pins inside GND…AVCC, with both diodes of each clamp reverse biased.

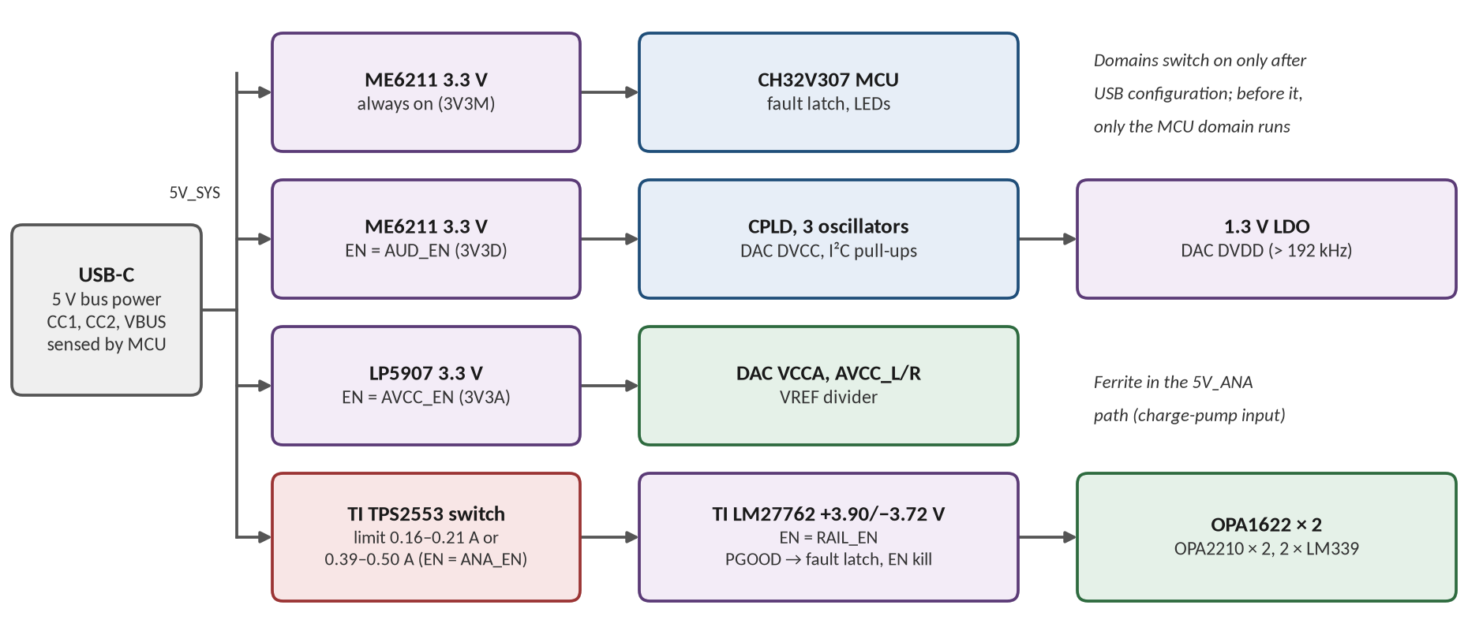
[picture p5: figure]
Power path diagram. The USB-C 5 V bus (CC1, CC2 and VBUS sensed by the MCU) feeds an always-on ME6211 3.3 V regulator (3V3M) for the CH32V307 MCU, the fault latch and the LEDs; a second ME6211 enabled by AUD_EN (3V3D) for the CPLD, the three oscillators, the DAC DVCC and the I2C pull-ups, followed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

Figure 2. Power path (switched power domains with the three oscillators on 3V3D, TPS2553 current limit, LM27762 +3.90 V / −3.72 V rails for the OPA2210 × 2, the OPA1622 × 2 and the two LM339 window comparators; PGOOD and the TPS2553 overcurrent flag set the fault latch).

## 3.3 Volume, gain and level

Gain is fixed. Volume comes from the host via USB Audio Class (Feature Unit volume and mute) and is applied in the ES9018K2M attenuator (0 to −127.5 dB in 0.5 dB steps), with MCU fine scaling for channel trim; a hardware knob is out of scope. Per leg, L = (Rf/Rs) × 2.156 Vrms with Rf = 836 Ω and Rs = 806 Ω ±11 %: nominal 2.236 Vrms, unit spread 1.955–2.589 Vrms including Rf 1 % and AVCC ±2 %. Every unit is therefore calibrated to 1.55 Vrms per leg at 0 dBFS (the OPA1622 clean swing ends ≈ 1.3 V from the rail) with the ES9018K2M 32-bit master trim, stored in MCU flash at the automated end-of-line test.

Parameter | Value | Basis
Calibrated full scale | 1.55 Vrms per leg (2.19 V peak): 3.5 mm 1.55 Vrms, 4.4 mm 3.1 Vrms | End-of-line calibration to ± 0.1 dB
Master trim | −2.02 dB (lowest-gain unit) to −4.46 dB (highest-gain unit); nominal −3.18 dB | ES9018K2M 32-bit master trim, stored in MCU flash
Before calibration | −4.5 dB, so ≤ 1.54 Vrms on any unit | Firmware safety default, active until a calibration is stored: an untrimmed highest-gain unit at 0 dBFS would exceed the calibrated full scale and the OPA1622 clean swing
Channel trim | ±0.05 dB | MCU digital scaling
Output envelope | ≤ 80 mA peak per leg (70 mA at 4.4 mm 32 Ω); Vpk ≤ (|rail|min − 1.3 V)/(1 + 8 Ω/Rleg) | OPA1622 clean swing: distortion starts ≈ 1.3 V from the rail (TI data at ±5 V: 600 Ω → 11.3 mW, 32 Ω → 150 mW); bench-verify at +3.90 V / −3.72 V

# 4. Key parts

Part | Role | Key specs | Package / assembly note | Unit price (run tier) | Source
WCH CH32V307RCT6 | USB audio bridge (MCU) | 144 MHz RISC-V, 3.3 V; built-in USB 2.0 High-Speed PHY; runs our own UAC2 firmware; sends the samples to the CPLD over SPI at 36 MHz with chip-select framing (MCU master, DMA); ADC1 on VBUS with the analog watchdog, ADC2 on seven channels: CC1, CC2, the four slow DC-sense channels and the 3V3A monitor (PC4), with pin leakage (1 µA × 15 kΩ) inside the DC-sense error budget; VBAT tied to 3V3M | LQFP-64, 10 × 10 mm; leaded; JLCPCB Extended | US$3.47 | LCSC C2988083 (LCSC 193 / JLCPCB 364 in stock; reserve)
AGM AGRV2KQ32 | CPLD: FIFO, I²S master, oscillator enables and MCLK_EN, bit clocks for all eight rates | 2K LUTs (AG32 silicon in pure-CPLD mode); one PLL, fed from the only dedicated clock pin PIN_1 (×2 on the selected family oscillator: 49.152 or 45.1584 MHz); no 80 MHz input and no free-running system clock; SPI SCK on the global network through ALTCLKCTRL, FIFO written in the SPI clock domain; 3.3 V LVCMOS; programmed over 2-wire Compact-JTAG (JTMS pin 24, JTCK pin 25; J-Link or AGM DAP-Link with AGM Supra); instant-on non-volatile | QFN-32, 4 × 4 mm; leadless, X-ray fee; Extended | US$1.65 | LCSC C18208899 (980 in stock)
SCTF SX3M80.000B20F30TNN (X201) | 80 MHz: DAC MCLK only, enabled by the CPLD (MCLK_EN) | 3.3 V CMOS; ±20 ppm tolerance, ±30 ppm stability; 40 mA max (SCTF 3C datasheet, 80–160 MHz); duty 45–55 %; tri-state pin 1 driven by MCLK_EN (CPLD pin 21) with the R218 2.2 kΩ pull-down, off by default and during CPLD configuration; load ≈ 10 pF + trace (DAC XI only); 12.5 ns cycle and ≥ 5.6 ns pulse width at 45:55 against the DAC limits of ≥ 10 ns and ≥ 4.5 ns | 3.2 × 2.5 mm, 4-pad; leadless, X-ray fee (counted conservatively); JLCPCB Extended | US$0.8916 (1+) | LCSC C5179978 (2,503 in stock); replaces the 100 MHz YXC part (C4353707)
YXC OT322524.576MJBA4SL (X202) | 24.576 MHz: 48 kHz family, OSC48_EN (off by default through the R212 2.2 kΩ pull-down; PLL ×2 = 49.152 MHz) | 1.8–3.3 V CMOS; tri-state pin 1 (YXC YSO110TR datasheet: enable ≥ 70 % VDD or floating, disable ≤ 30 % VDD; no disable time specified); start-up ≤ 3 ms; 5 mA max; duty 45–55 %; ±10 ppm tolerance, ±20 ppm stability; 33 Ω (R210) into the shared PLL input node | 3.2 × 2.5 mm, 4-pad; leadless, X-ray fee (counted conservatively); Extended assumed (class not shown on the JLCPCB page; its fixture sentence is standard page text) | US$0.51 | LCSC C2831388 (1,755 in stock)
SCTF SX2M22.5792M20F30TNN (X203) | 22.5792 MHz: 44.1 kHz family, OSC44_EN (off by default through the R213 2.2 kΩ pull-down; PLL ×2 = 45.1584 MHz) | 1.62–3.63 V CMOS; pin 1 “Tri-State” (SCTF 2CM datasheet: enabled when OE is logic 1 or open, disabled at logic 0, ≤ 0.3 VDD; no disable or enable time, internal pull-up value or disabled-output leakage specified); start-up ≤ 5 ms; 10 mA max; duty 45–55 %; ±20 ppm tolerance, ±30 ppm stability; 33 Ω (R211) into the shared PLL input node | 2.5 × 2.0 mm, 4-pad; leadless, X-ray fee (counted conservatively); Extended (JLCPCB part page) | US$0.55 | LCSC C5452663 (1,426 in stock)
ESS ES9018K2M | DAC | 32-bit; PCM to 384 kHz; DNR 127 dB-A and THD+N −120 dB (datasheet, current mode); each pin ≈ 3.05 Vpp source behind 806 Ω ±11 %; asynchronous (PCM normal) mode needs MCLK > 192 × FSR, MCLK cycle ≥ 10 ns and pulse width ≥ 4.5 ns; external 1.3 V DVDD above 192 kHz (50 mA at MCLK 80 MHz and 192 kHz); output pins GND < Vout < AVCC (absolute maximum); outputs driven to ground in reset (≈ 2.1 mA per pin with AVCC up); I²C 7-bit address 0x48 (written 0x90) with ADDR to DGND; attenuator 0 to −127.5 dB in 0.5 dB steps; 32-bit master trim | QFN-28, 5 × 5 mm; leadless, X-ray fee; Extended | US$3.47 | LCSC C2688377 (724 in stock; reserve); ESS datasheet v3.7
TI OPA2210IDR (× 2, U403 and U404) | I/V converters, one amplifier per DAC pin | Single input pair, common-mode range (V−) + 1.5 V to (V+) − 1.5 V (VREF ≤ 1.754 V worst case, ≈ 0.53 V inside at the minimum +rail of 3.789 V); Vos ±35 µV max; 2.2 nV/√Hz; 18 MHz; 2.2 / 2.5 mA per channel; ±2.25 V to ±18 V; output swing ≈ (V+) − 0.3 V at the ≈ 3 mA I/V load (estimate; TI: (V+) − 0.2 V at 10 kΩ, (V+) − 0.6 V at 600 Ω); input current 10 mA (absolute maximum); same dual pinout as the OPA2197 it replaces and as the OPA1612AIDR fallback | SOIC-8; leaded; Extended; the fixture sentence on its JLCPCB page is standard text on every part page | US$1.0035 (JLCPCB 10+; 1+ US$1.2180, 100+ US$0.7530) | LCSC C1849415; JLCPCB stock unverified (the 76 figure is 12 months old): check the JLCPCB Parts Manager and buy 12 (10 + 2 spares) if ≥ 12, otherwise switch to the OPA1612AIDR fallback (C94590, Extended; LCSC 10+ US$1.0942, stock 9,754; JLCPCB US$1.33, 31,254 available, page of 28 Aug 2026; VREF ≥ 35 mV inside its (V+) − 2 V limit at +3.90 V); the OPA2210 at the LCSC price (US$2.67 at 10+) would add ≈ 106 NTD per board, over the ceiling; TI SBOS924H
TI OPA1622IDRCR (× 2) | Output legs, one amplifier per leg | Vos ±0.5 mV max; Isc +145/−130 mA typ; clean (low-distortion) swing ends ≈ 1.3 V from the rail (TI data at ±5 V: 600 Ω → 11.3 mW, 32 Ω → 150 mW), falling ≈ 8 Ω × Iout; current limit ≈ 110–120 mA at 85 °C die; EN threshold ≈ 0.82 V referenced to its GND pin (pin 3, tied to GND); continuous short rated for one amplifier per package; θJA 47.6 °C/W | VSON-10, 3 × 3 mm; leadless, X-ray fee; thermal pad to V−; Extended | US$1.79 (10+ tier) | LCSC C2876559; TI SBOS727B
TI LM27762DSSR | +3.90 V / −3.72 V headphone rails | VOUT+ = 1.2 V × (R1 + R2)/R2, VOUT− = −1.22 V × (R3 + R4)/R4: +3.900 V (3.789–4.014 V) and −3.722 V (3.618–3.828 V magnitude) including VFB and the 1 % resistors; ±250 mA; negative LDO dropout 30 mV and positive 45 mV at 100 mA; input current limit 500 mA typ; PGOOD open drain pulled up to 5V_ANA (R505 10 kΩ), low = both outputs ≥ 95 % (+3.71 V, −3.54 V), sets the latch (Q610) and drives the Q609 interlock; 0.39 W at 5.25 V (θJA 62.2 °C/W, ≈ +24 °C), 0.46 W at 5.5 V; VIN rated to 5.5 V (no margin above it, accepted for v1); 50 kΩ output pull-down in shutdown (not relied on) | WSON-12, 2 × 3 mm; leadless, X-ray fee; Extended | US$1.0174 | LCSC C473398; TI SNVSAF7C
TI TPS2553DBVR | Current-limited switch for 5V_ANA (Default and High limits) | Limit set by RILIM (15–232 kΩ), acting on the instantaneous current (short-circuit response ≈ 2 µs, then constant-current limiting); rDS(on) 85 mΩ typ / 135 mΩ max; 9 mW in normal use, ≤ 2.6 W into a short for ≤ 10 ms before the latch or FAULT path acts (thermal shutdown protects); soft start; FAULT open drain, 5/7.5/10 ms deglitch, also sets the fault latch through D606 and R638; auto-retry version kept (the latch-off TPS2553-1 is listed as not recommended for new designs) | SOT-23-6; leaded; Extended | US$0.60 | LCSC C55266; TI SLVS841F

TI LM339DR (× 2, U601 and U602)

DC-detect window comparators, one window per leg (replace the LM393BIDR)

Quad, open collector, on the +3.90 V / −3.72 V rails; supply current 0.8 mA typical, 2 mA maximum per package; each leg filter node drives a positive (IN− = node) and a negative (IN+ = node) comparator directly, no diode-OR; offset 5 mV at 25 °C, 9 mV over temperature; input bias 250 nA maximum at 25 °C, 400 nA over 0–70 °C per input, flowing out (node shift 0…+81 mV through 100 kΩ, inside the worst case); TI: one input can exceed VCC and the comparator provides a proper output state as long as the other input remains in the common-mode range (TI LM339 datasheet, SLCS006Z), so a rail-stuck leg still trips; no input goes more than 0.3 V below the negative supply (all nodes stay within the rails); ESD ±2 kV HBM; eight outputs wired-OR into node F; C612–C615 4 × 100 nF supply decoupling

SOIC-14; leaded; Extended (replaces the LM393BIDR, so the Extended-type count is unchanged)

US$0.18 (JLCPCB); LCSC 5+ US$0.1666

LCSC C7948 (JLCPCB available 19,325); drop-in alternative LM339BIDR (C22416291, IB ≤ 50 nA, 2 kV ESD), preferred if JLCPCB stocks it (≈ −3.6 NTD per board)
Microne ME6216A13M3G | 1.3 V external DVDD (from 3V3D) | Fixed 1.3 V, ±1 % (±15 mV), 250 mA max, ceramic-stable, 6 µA Iq; Pd 0.54 W; pin 1 VSS, pin 2 VOUT, pin 3 VIN; short-circuit foldback 50–70 mA | SOT23-3 (“M3”); leaded; Extended | US$0.06 | LCSC C236662 (≈ 3,100 in stock)
Murata BLM18PG121SN1D | 5V_ANA power ferrite | 120 Ω at 100 MHz; 2 A; 50 mΩ | 0603; JLCPCB Basic | US$0.016 | LCSC C14709

Not in the table: U205, a Nexperia 74LVC1G157GW,125 2:1 logic multiplexer (LCSC C135822, SOT-363, Extended), with R215 (33 Ω) and the R216/R217 10 kΩ input pull-downs, forms a DNF fallback footprint at the CPLD PLL clock input (select = OSC44_EN). To use it, fit U205, R215, R216 and R217 and remove R210 and R211; one of the two Stage 2 boards is built with it fitted.

All other parts are chosen in Schematic Design Notes v0.7 (part number, LCSC number, stock and price). Parts List v0.6 is the source of truth for cost; every line’s JLCPCB class is taken from its JLCPCB part page or the basic-parts list, except X202, whose class is not shown (assumed Extended).

# 5. Headphone drive and estimates

## 5.1 Load requirements

Current limits the low-impedance loads. The clean output envelope is ≤ 80 mA peak per leg within the OPA1622 clean swing, and 70 mA at 4.4 mm 32 Ω, where 80 mA would leave negative headroom on the negative rail with a 3.5 Ω charge-pump resistance (Section 3.2); overload behaviour is handled separately by the TPS2553 current limit and the fault latch (Section 5.3). The OPA1622’s +145/−130 mA figure is a typical short-circuit current and its current limit is ≈ 110–120 mA at an 85 °C die, so neither is a linear output rating.

Requirement | Value | Basis
Loads | 16–600 Ω on both jacks | Load matrix in Section 5.2
Clean envelope | ≤ 80 mA peak per leg; 70 mA at 4.4 mm 32 Ω | One amplifier per leg (U401 = L+/L−, U402 = R+/R−); 70 mA from the negative-rail headroom (Section 3.2)
Swing model | Vpk ≤ (|rail|min − 1.3 V)/(1 + 8 Ω/Rleg) | Clean swing: distortion starts ≈ 1.3 V from the rail (TI data at ±5 V: 600 Ω → 11.3 mW, 32 Ω → 150 mW); worst-case rail |rail|min = 3.618 V (bench-verify)
Rails | +3.900 V (3.789–4.014 V), −3.722 V (−3.618 to −3.828 V) | LM27762 feedback reference (VFB) and the 1 % divider resistors
Full-scale level | 1.55 Vrms per leg (2.19 V peak) after calibration | Section 3.3
Output impedance | < 0.1 Ω plus jack contacts (the OPA1622 legs drive the jacks directly, no ballast); target ≤ 0.5 Ω on both jacks | Estimate
Reference headphones | HIFIMAN Susvara (60 Ω, 83 dB/mW); AKG K1000 (120 Ω, 74 dB/mW) | Maker specifications; SPL in Section 5.2
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
