ooyang0325/Hi-Res-DAC/hardware/DAC_HPA_100x80_placement_preview.png

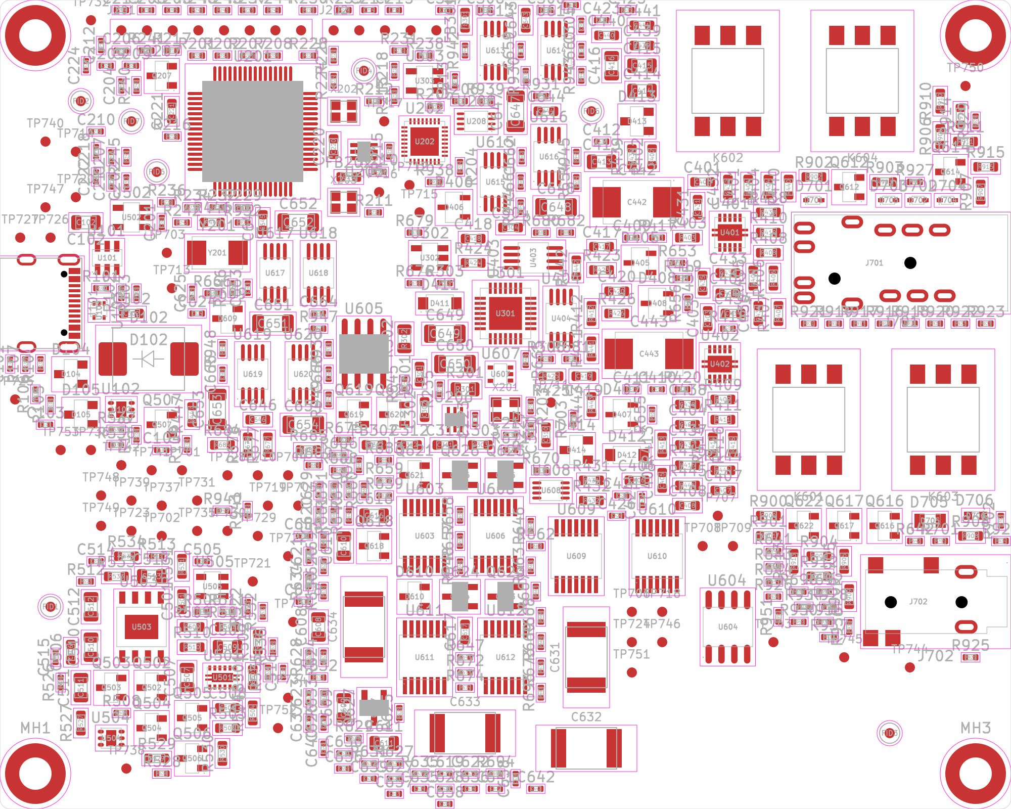
hardware/DAC_HPA_100x80_placement_preview.png
