ooyang0325/Hi-Res-DAC/hardware/DAC_HPA_120x100_timer_zoom.png

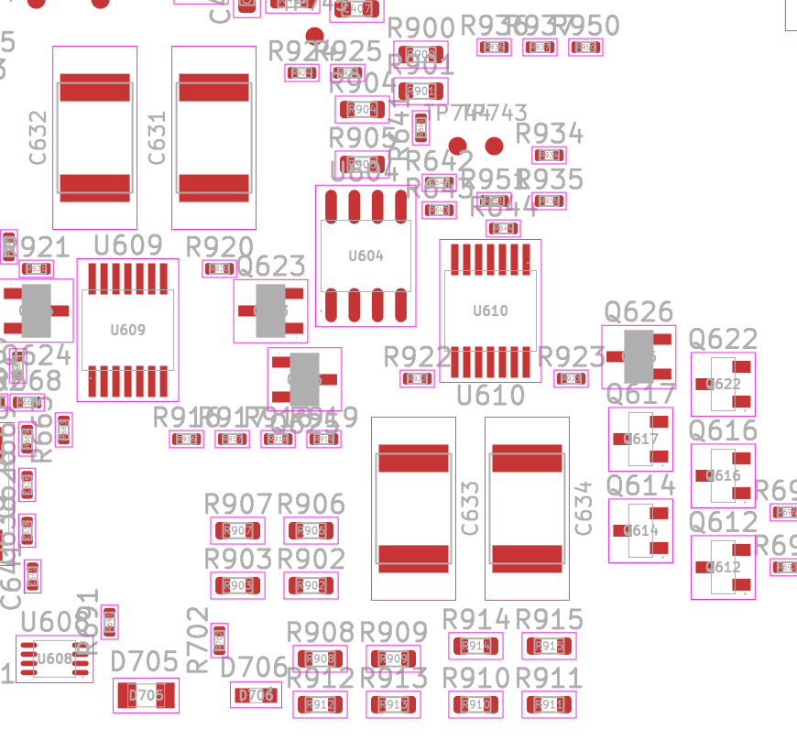
hardware/DAC_HPA_120x100_timer_zoom.png
