ooyang0325/Hi-Res-DAC/hardware/DAC_HPA_J101_3D_detail.png

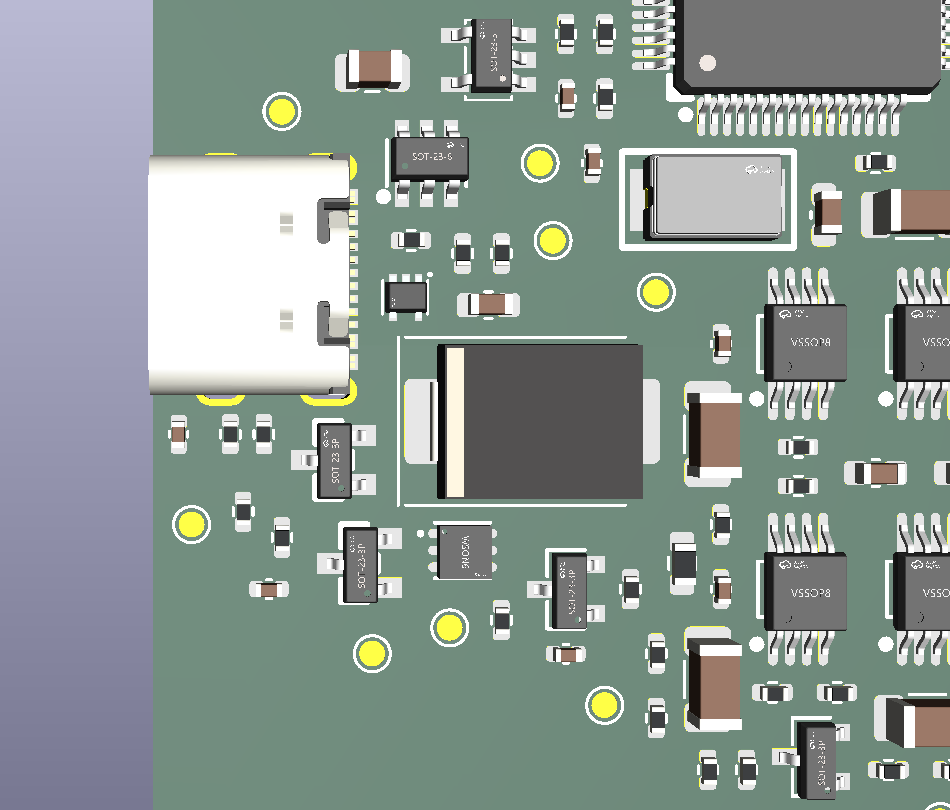
hardware/DAC_HPA_J101_3D_detail.png
