ooyang0325/Hi-Res-DAC/hardware/sim/dac_1v3_bypass_sweep.png

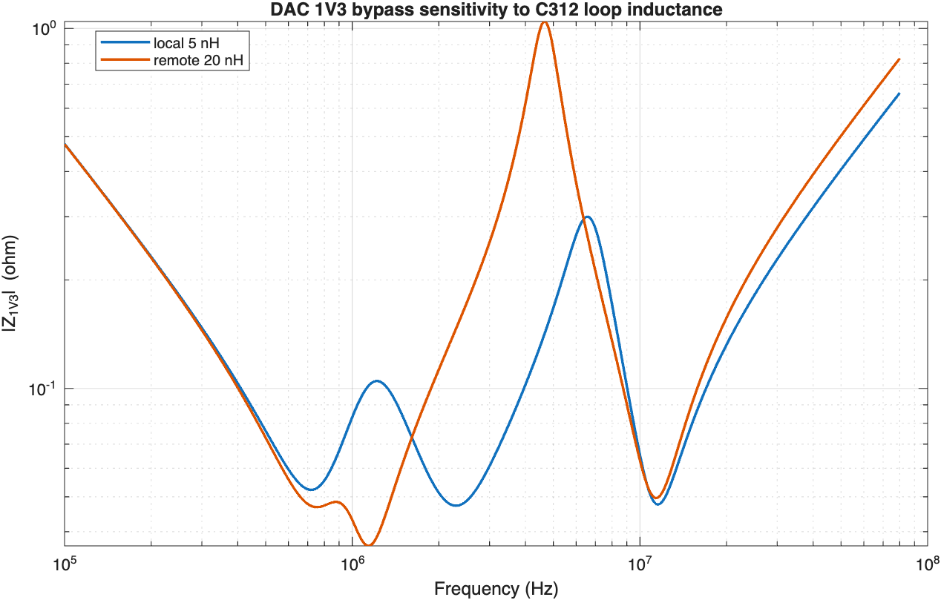
hardware/sim/dac_1v3_bypass_sweep.png
