ooyang0325/Hi-Res-DAC/hardware/sim/ems_rf_demod.png

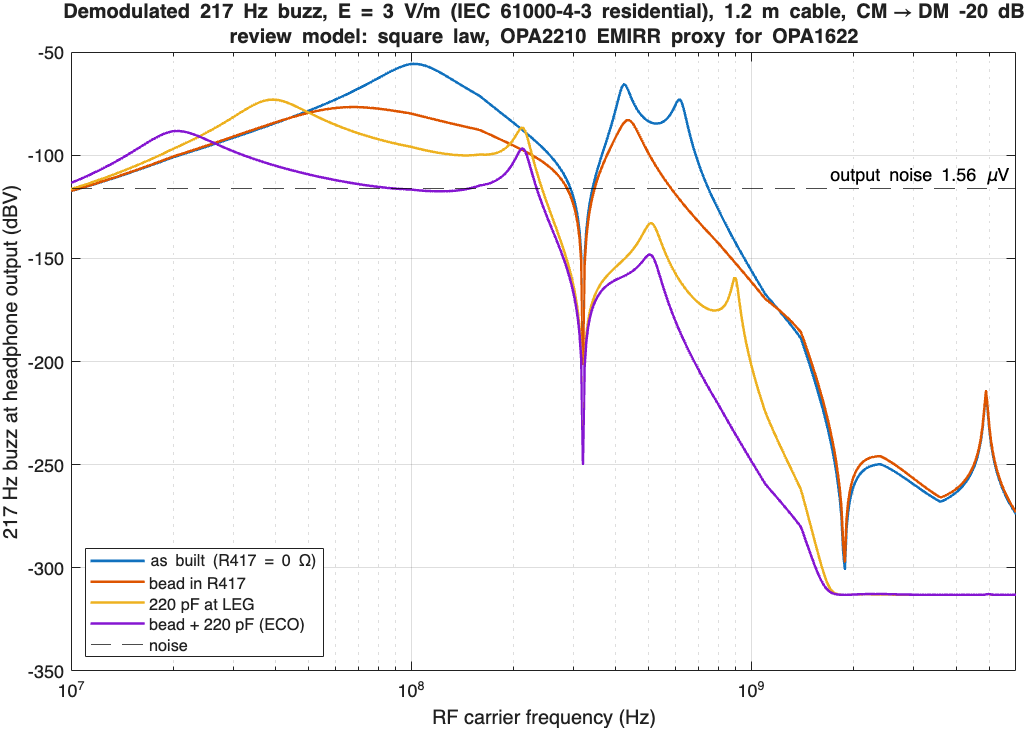
hardware/sim/ems_rf_demod.png
