ooyang0325/Hi-Res-DAC/hardware/EASYEDA_MODELS/LED0603_L1.6-W0.8-H0.6.step

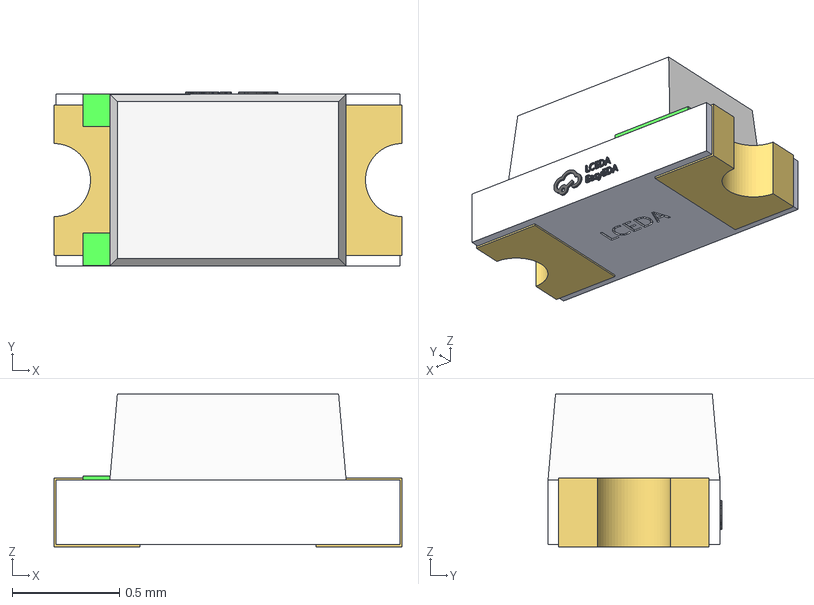
[picture p30: CAD file, 2026-10-06]
hardware/EASYEDA_MODELS/LED0603_L1.6-W0.8-H0.6.step
1.62 x 0.81 x 0.71 mm
