ooyang0325/Hi-Res-DAC/hardware/EASYEDA_MODELS/SOT-23-6_L2.9-W1.6-H1.5-LS2.8-P0.95.step

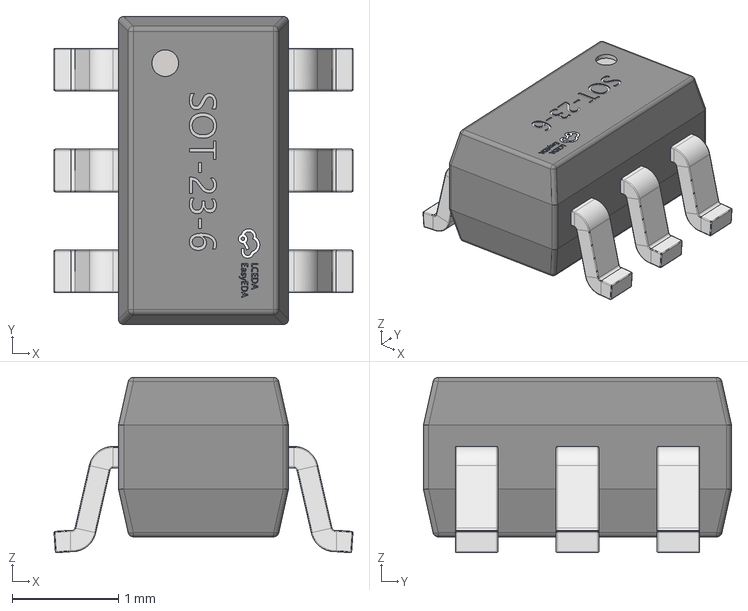
[picture p31: CAD file, 2026-10-06]
hardware/EASYEDA_MODELS/SOT-23-6_L2.9-W1.6-H1.5-LS2.8-P0.95.step
2.81 x 2.90 x 1.65 mm
