ooyang0325/Hi-Res-DAC/hardware/EASYEDA_MODELS/VSON-10_L3.0-W3.0-P0.50-BL-EP1.65.step

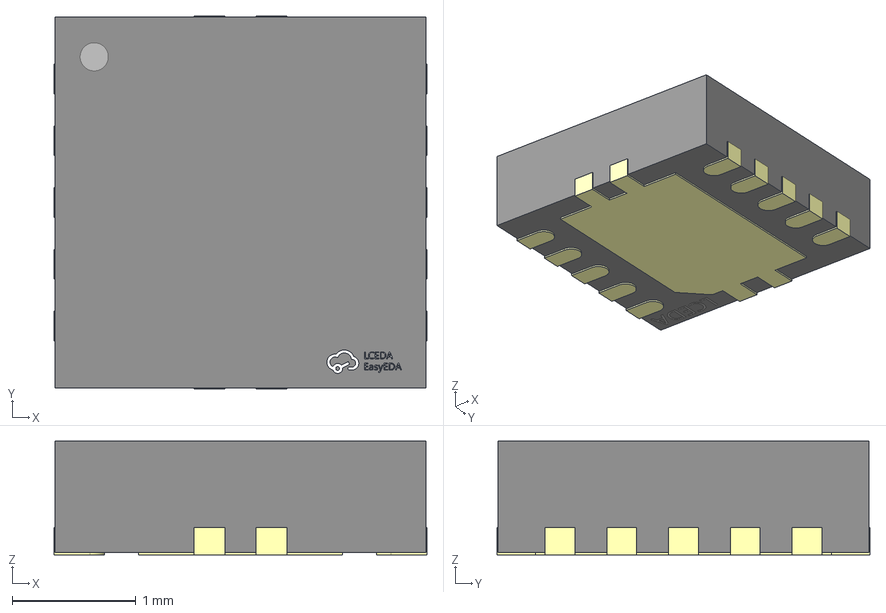
[picture p32: CAD file, 2026-10-06]
hardware/EASYEDA_MODELS/VSON-10_L3.0-W3.0-P0.50-BL-EP1.65.step
3.02 x 3.02 x 0.921 mm
