ooyang0325/Hi-Res-DAC/hardware/EASYEDA_MODELS/VSSOP-8_L3.0-W3.0-H1.1-LS4.9-P0.65.step

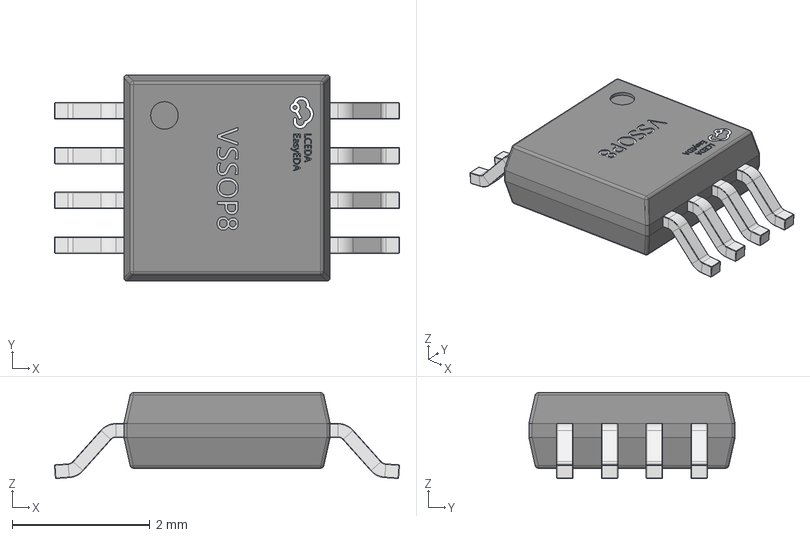
[picture p33: CAD file, 2026-10-06]
hardware/EASYEDA_MODELS/VSSOP-8_L3.0-W3.0-H1.1-LS4.9-P0.65.step
5.01 x 3.00 x 1.25 mm
