ooyang0325/Hi-Res-DAC/hardware/EASYEDA_MODELS/WSON-6_L2.0-W2.0-H0.8-P0.65.step

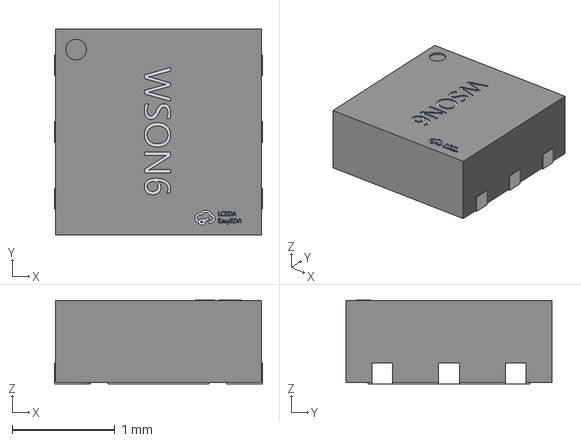
[picture p34: CAD file, 2026-10-06]
hardware/EASYEDA_MODELS/WSON-6_L2.0-W2.0-H0.8-P0.65.step
2.02 x 2.00 x 0.811 mm
