ooyang0325/Hi-Res-DAC/hardware/EASYEDA_MODELS/SOP-8_L4.9-W3.9-P1.27-LS6.0-BL-1.step

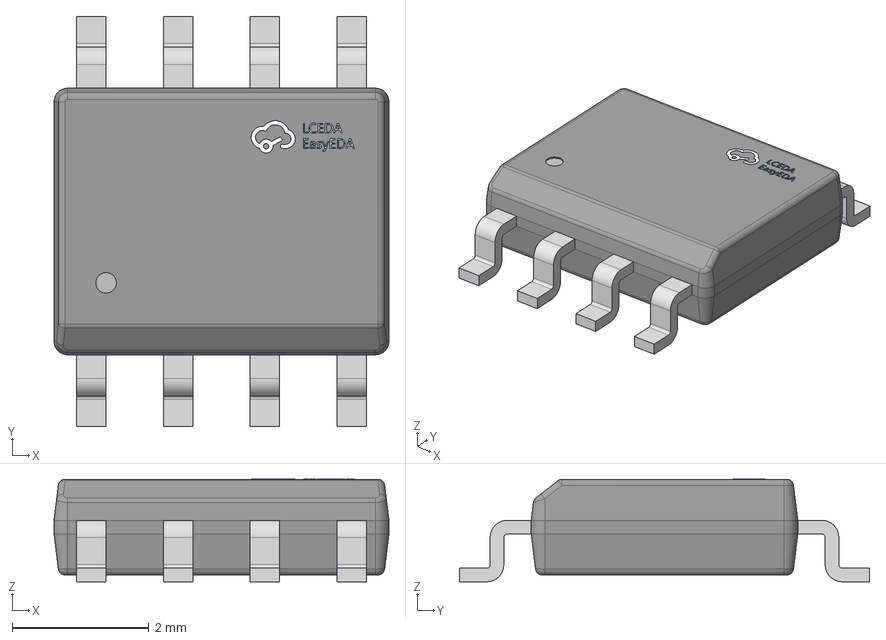
[picture p35: CAD file, 2026-10-06]
hardware/EASYEDA_MODELS/SOP-8_L4.9-W3.9-P1.27-LS6.0-BL-1.step
4.90 x 6.00 x 1.50 mm
