ooyang0325/Hi-Res-DAC/hardware/EASYEDA_MODELS/QFN-28_L5.0-W5.0-H0.9-P0.50.step

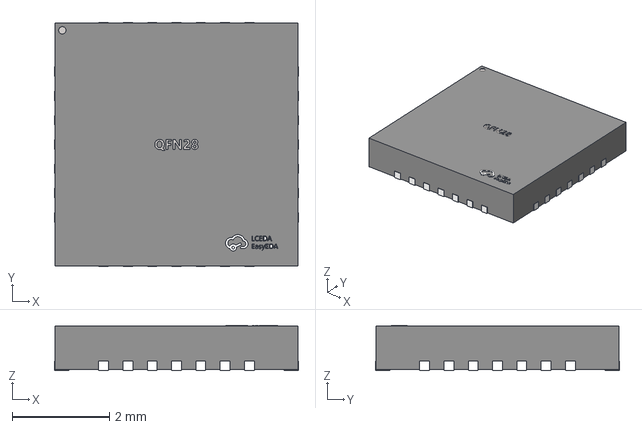
[picture p36: CAD file, 2026-10-06]
hardware/EASYEDA_MODELS/QFN-28_L5.0-W5.0-H0.9-P0.50.step
5.02 x 5.02 x 0.93 mm
