ooyang0325/Hi-Res-DAC/hardware/EASYEDA_MODELS/SOT-23-3P_L2.9-W1.3-H1.0-LS2.4-P0.95.step

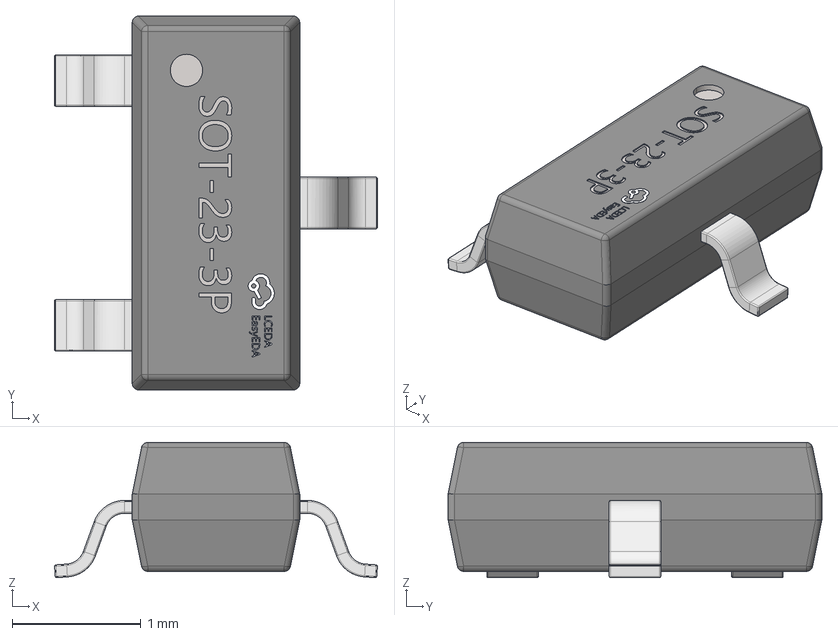
[picture p37: CAD file, 2026-10-06]
hardware/EASYEDA_MODELS/SOT-23-3P_L2.9-W1.3-H1.0-LS2.4-P0.95.step
2.51 x 2.90 x 1.05 mm
