ooyang0325/Hi-Res-DAC/hardware/EASYEDA_MODELS/TSSOP-14_L5.0-W4.4-H1.0-LS6.4-P0.65.step

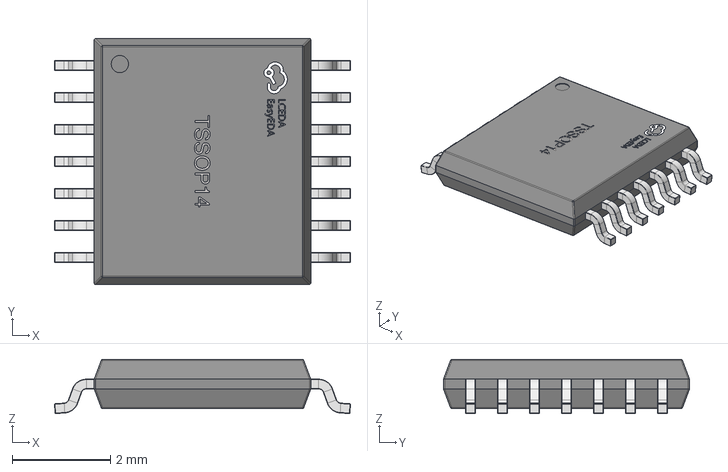
[picture p38: CAD file, 2026-10-06]
hardware/EASYEDA_MODELS/TSSOP-14_L5.0-W4.4-H1.0-LS6.4-P0.65.step
6.01 x 5.00 x 1.10 mm
