ooyang0325/Hi-Res-DAC/hardware/EASYEDA_MODELS/LED0805-RD.step

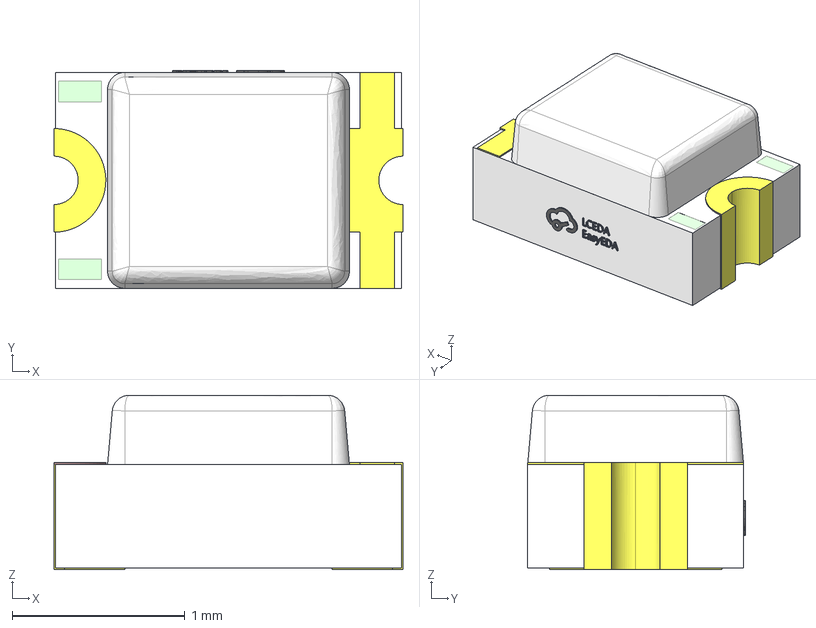
[picture p39: CAD file, 2026-10-06]
hardware/EASYEDA_MODELS/LED0805-RD.step
2.02 x 1.26 x 1.01 mm
