ooyang0325/Hi-Res-DAC/hardware/EASYEDA_MODELS/WSON-12_L3.0-W2.0-H0.8-P0.50.step

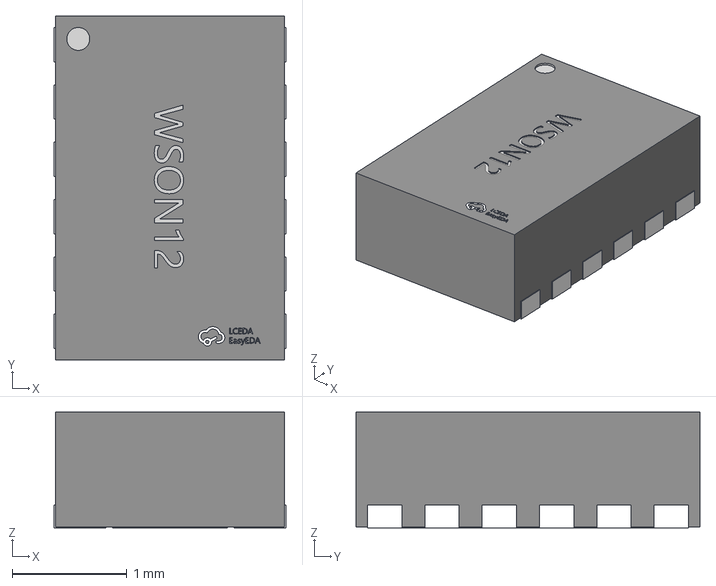
[picture p40: CAD file, 2026-10-06]
hardware/EASYEDA_MODELS/WSON-12_L3.0-W2.0-H0.8-P0.50.step
2.02 x 3.00 x 1.01 mm
