ooyang0325/Hi-Res-DAC/hardware/EASYEDA_MODELS/SOT-23-5_L2.9-W1.6-P0.95-LS2.8-BR.step

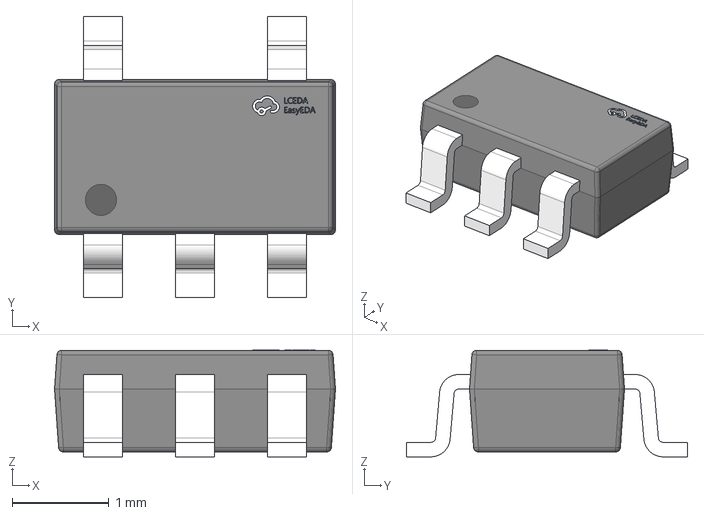
[picture p41: CAD file, 2026-10-06]
hardware/EASYEDA_MODELS/SOT-23-5_L2.9-W1.6-P0.95-LS2.8-BR.step
2.90 x 2.90 x 1.10 mm
