ooyang0325/Hi-Res-DAC/hardware/EASYEDA_MODELS/SOD-523_L1.2-W0.8-LS1.6-BI.step

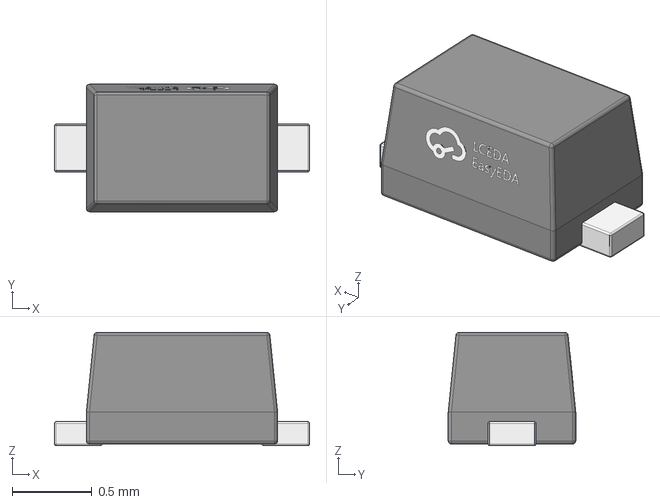
[picture p42: CAD file, 2026-10-06]
hardware/EASYEDA_MODELS/SOD-523_L1.2-W0.8-LS1.6-BI.step
1.60 x 0.8 x 0.71 mm
