ooyang0325/Hi-Res-DAC/hardware/EASYEDA_MODELS/SOT-363-6P_L2.0-W1.3-H1.1-LS2.0-P0.65.step

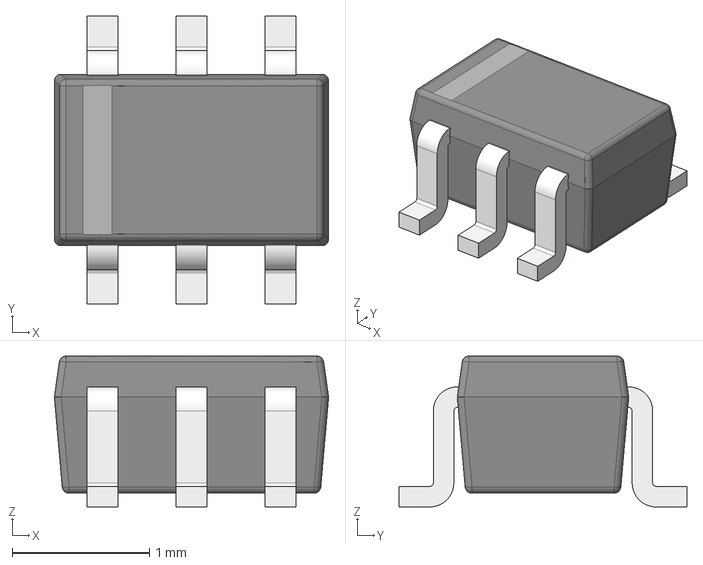
[picture p43: CAD file, 2026-10-06]
hardware/EASYEDA_MODELS/SOT-363-6P_L2.0-W1.3-H1.1-LS2.0-P0.65.step
2.00 x 2.10 x 1.10 mm
