ooyang0325/Hi-Res-DAC/hardware/EASYEDA_MODELS/AUDIO-TH_GT-3321667P-01.step

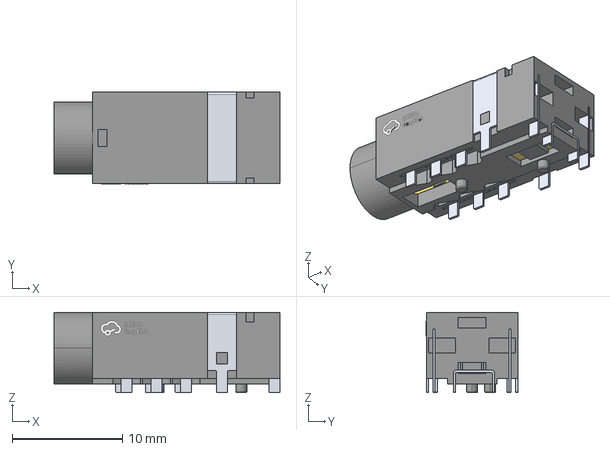
[picture p44: CAD file, 2026-10-06]
hardware/EASYEDA_MODELS/AUDIO-TH_GT-3321667P-01.step
20.5 x 8.31 x 7.30 mm
