ooyang0325/Hi-Res-DAC/hardware/EASYEDA_MODELS/VSSOP-8_L2.0-W2.3-H0.9-LS3.1-P0.50.step

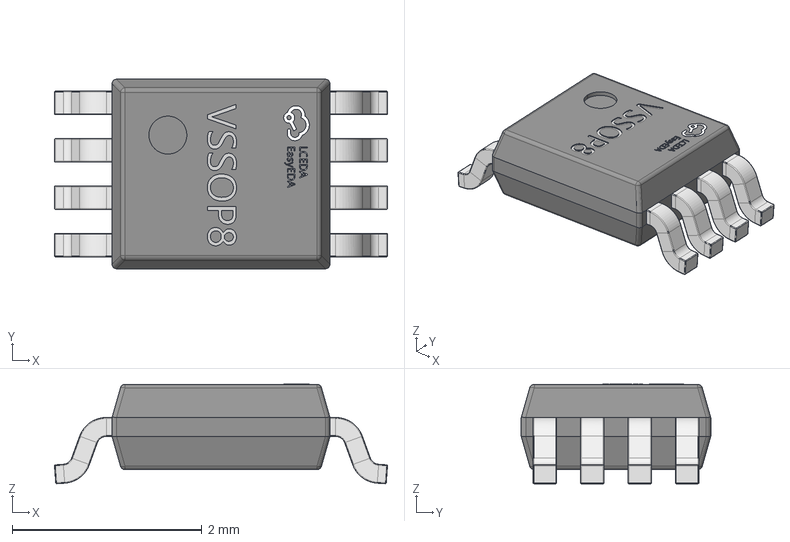
[picture p45: CAD file, 2026-10-06]
hardware/EASYEDA_MODELS/VSSOP-8_L2.0-W2.3-H0.9-LS3.1-P0.50.step
3.51 x 2.00 x 1.05 mm
