ooyang0325/Hi-Res-DAC/hardware/EASYEDA_MODELS/CASE-D_L7.3-W4.3-H2.9.step

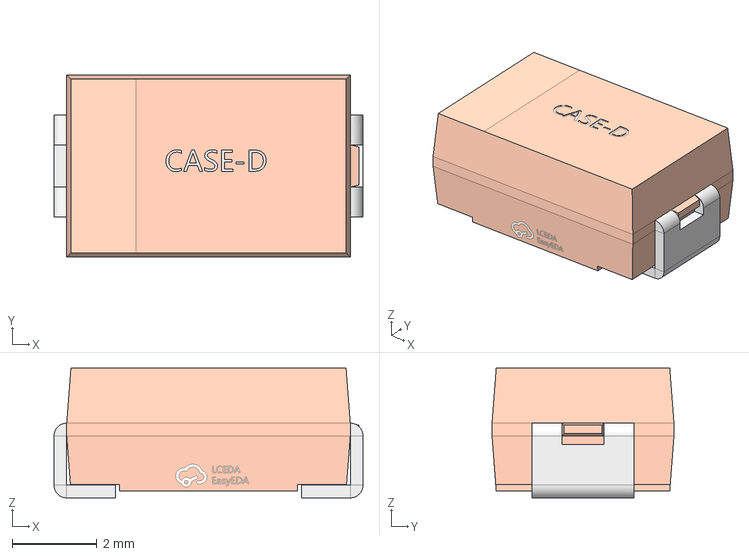
[picture p46: CAD file, 2026-10-06]
hardware/EASYEDA_MODELS/CASE-D_L7.3-W4.3-H2.9.step
7.30 x 4.30 x 3.07 mm
