ooyang0325/Hi-Res-DAC/hardware/EASYEDA_MODELS/SOT-23-5_L2.9-W1.6-H1.1-LS2.8-P0.95.step

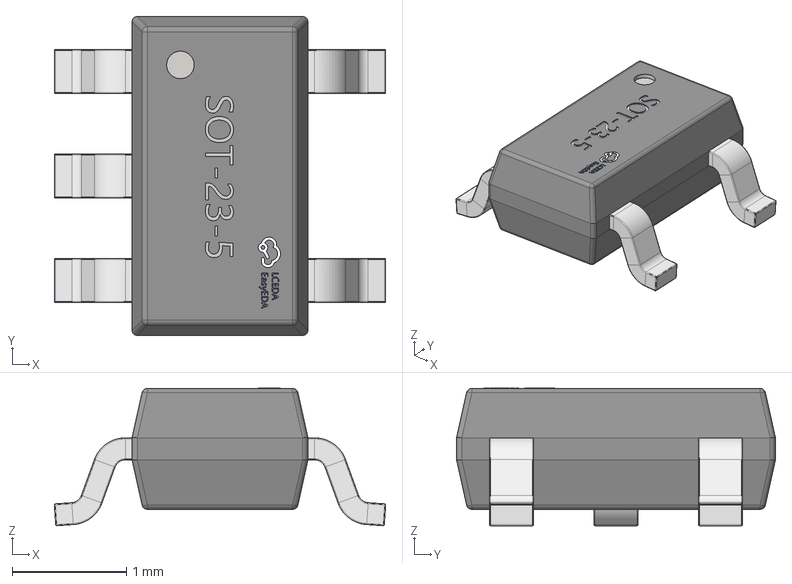
[picture p47: CAD file, 2026-10-06]
hardware/EASYEDA_MODELS/SOT-23-5_L2.9-W1.6-H1.1-LS2.8-P0.95.step
2.90 x 2.79 x 1.20 mm
