ooyang0325/Hi-Res-DAC/hardware/EASYEDA_MODELS/SOT-23-3L_L2.9-W1.6-H1.1-LS2.8-P0.95.step

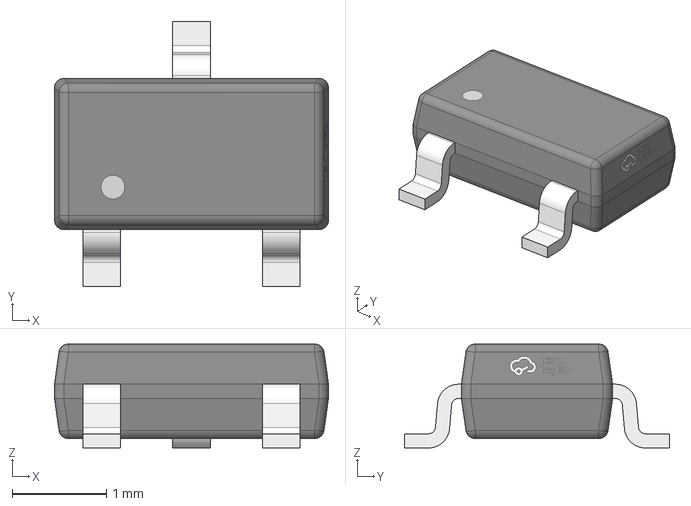
[picture p48: CAD file, 2026-10-06]
hardware/EASYEDA_MODELS/SOT-23-3L_L2.9-W1.6-H1.1-LS2.8-P0.95.step
2.90 x 2.80 x 1.10 mm
