ooyang0325/Hi-Res-DAC/hardware/signoff/out/spice/pdn_3V3A.cir

* PDN impedance at the worst-case 3V3A pin, from extracted layout.
* Element values: R from the solved copper network, L from the real
* via geometry and routed path, C from the placed part.
* h = outer-layer to first-plane dielectric height in mm (swept),
* because the board declares no stackup.
.param h=0.12
Itest 0 vdd AC 1
Rsrc vdd nsrc 0.01
Lsrc nsrc 0 {3.14159e-08*h}
* C302 0603 2200 nF, 2.6 mm from the pin
R0 vdd a0 0.0276447
L0 a0 b0 {1.6241e-08*h+5.5e-10}
C0 b0 0 2.2e-06
Rp0 b0 0 1G
* C441 0603 1000 nF, 50.6 mm from the pin
R1 vdd a1 0.112183
L1 a1 b1 {1.67409e-07*h+5.5e-10}
C1 b1 0 1e-06
Rp1 b1 0 1G
.step param h list 0.09 0.12 0.2
.ac dec 400 100000 1e+08
.meas ac zmax MAX mag(V(vdd)) FROM 100000 TO 1e+08
.meas ac zlow FIND mag(V(vdd)) AT=100000
.meas ac zcrit FIND mag(V(vdd)) AT=2.25792e+07
.meas ac zhigh FIND mag(V(vdd)) AT=1e+08
.meas ac fcross WHEN mag(V(vdd))=0.33 RISE=1
.end
